jnahuel-developer/Probador-de-cables/Cables/02. Terminados - PDF/MAZ000157 - Diagrama eléctrico.pdf

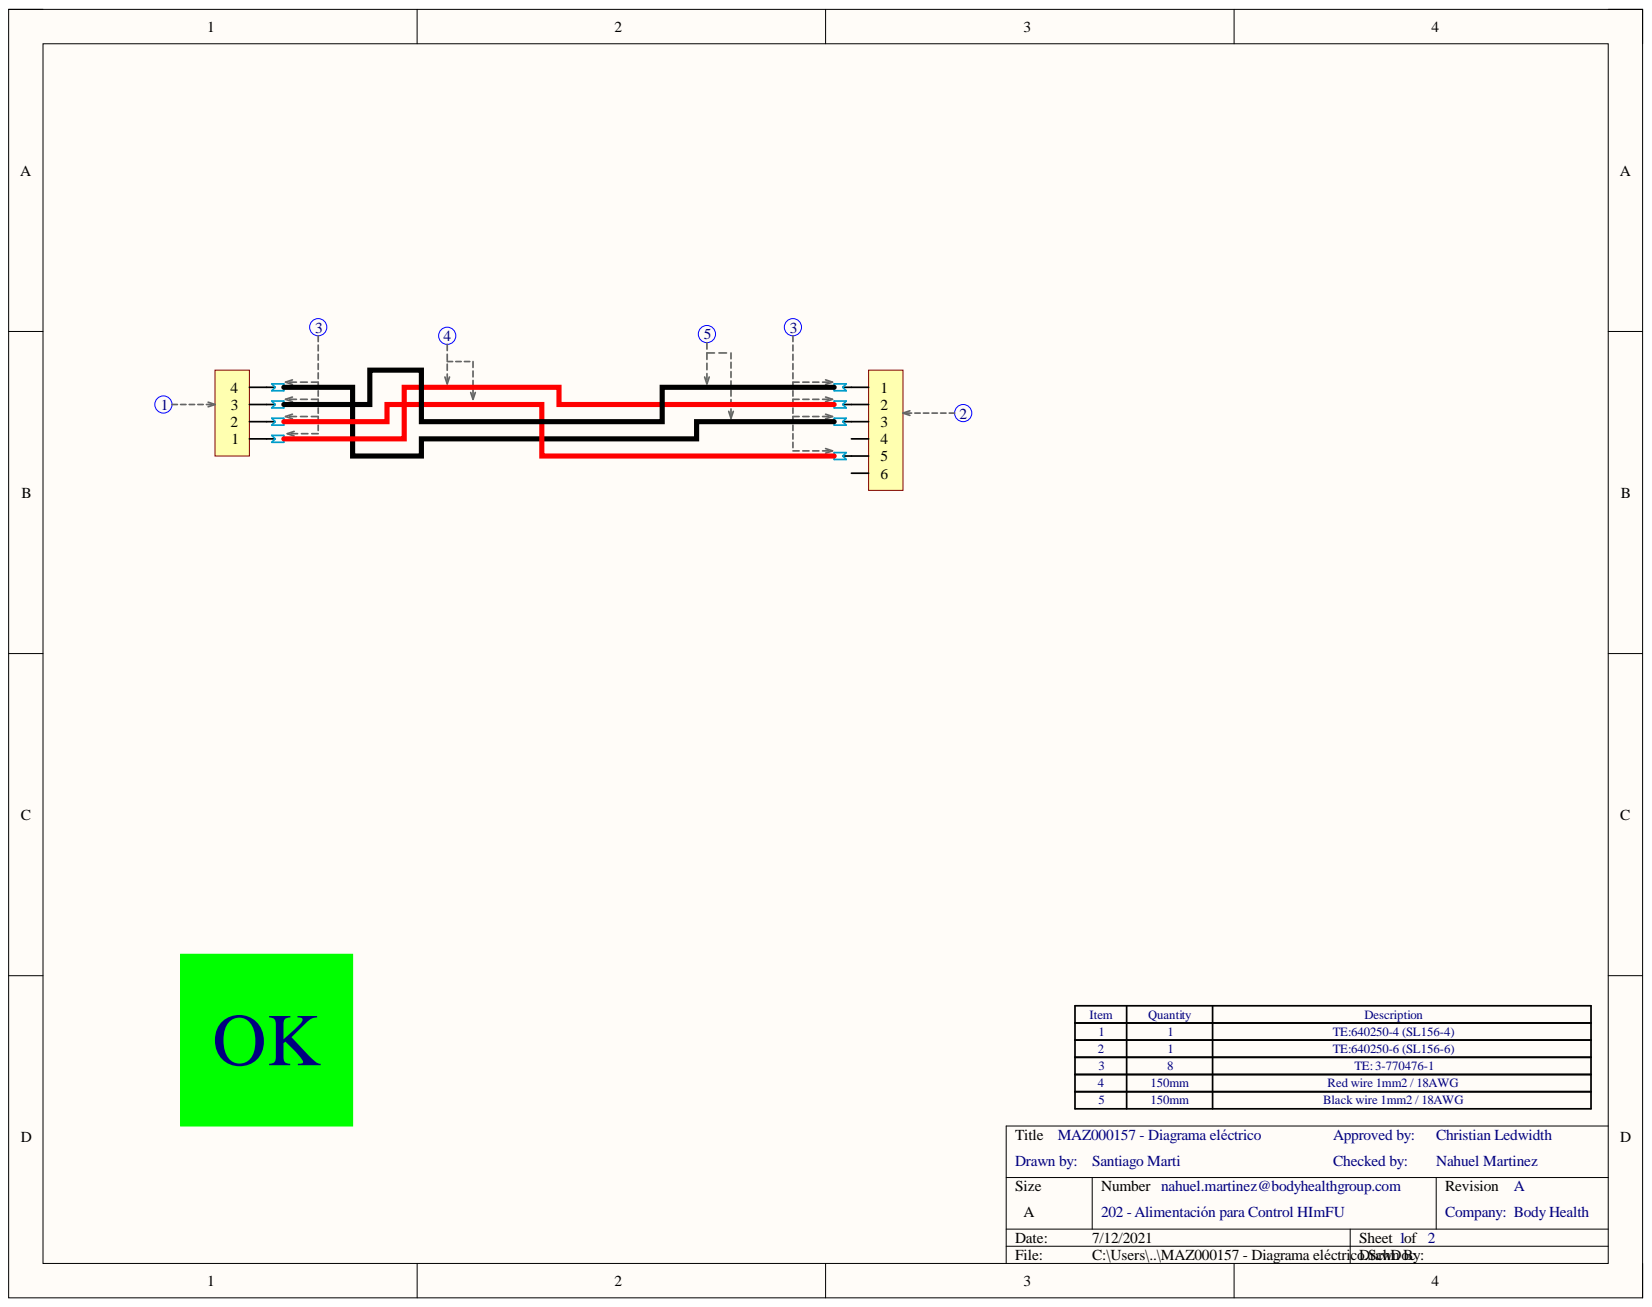
[picture p18: page 1]

Item | Quantity | Description
1 | 1 | TE:640250-4 (SL156-4)
2 | 1 | TE:640250-6 (SL156-6)
3 | 8 | TE: 3-770476-1
4 | 150mm | Red wire 1mm2 / 18AWG
5 | 150mm | Black wire 1mm2 / 18AWG

Size A | Number nahuel.martinez@bodyhealthgroup.com 202 - Alimentación para Control HImFU | Revision A Company: Body Health

Date: 7/12/2021 | Sheet of 1 2
File: C:\Users\..\MAZ000157 - Diagrama eléctricoDr.ScawhDon Bcy:
