jnahuel-developer/Probador-de-cables/Cables/02. Terminados - PDF/MAZ000158 - Diagrama eléctrico.pdf

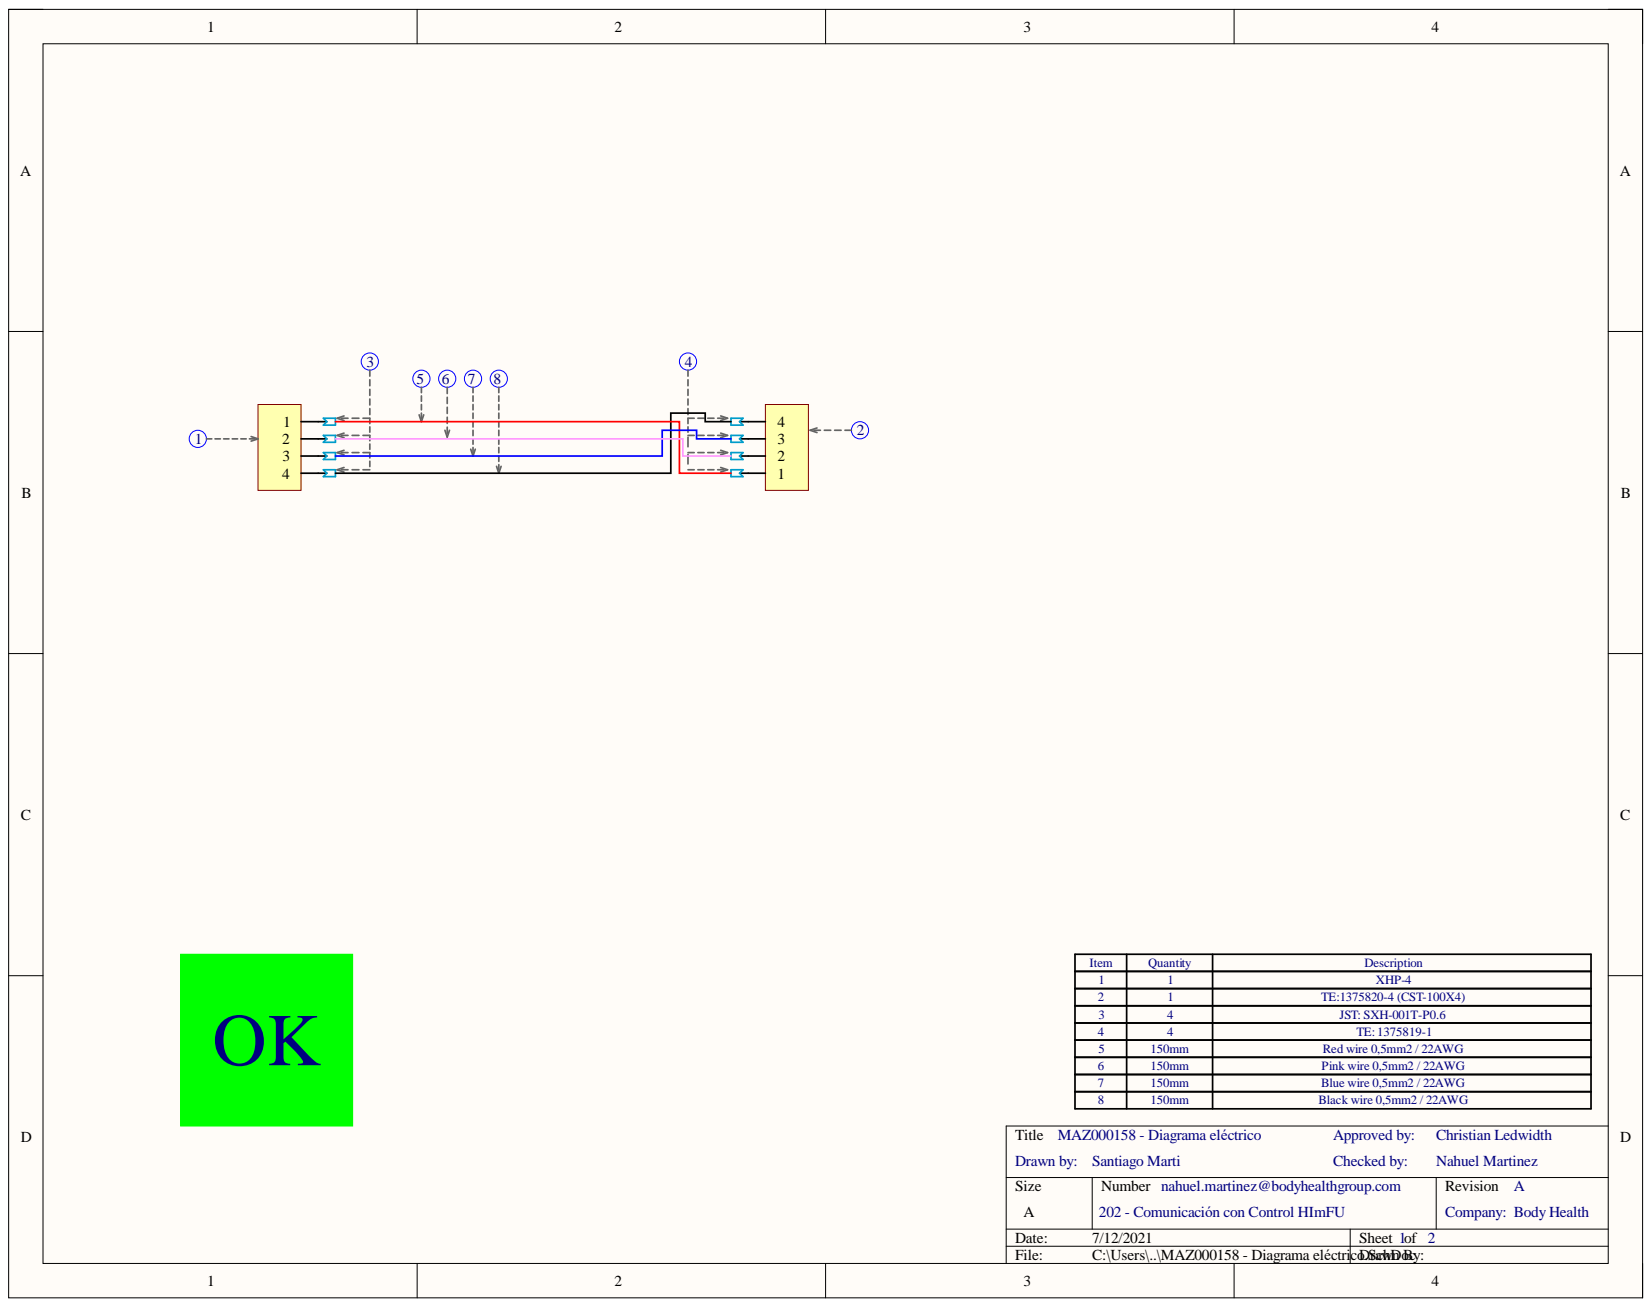
[picture p20: page 1]

1 | 1 | XHP-4
2 | 1 | TE:1375820-4 (CST-100X4)
3 | 4 | JST: SXH-001T-P0.6
4 | 4 | TE: 1375819-1
5 | 150mm | Red wire 0,5mm2 / 22AWG
6 | 150mm | Pink wire 0,5mm2 / 22AWG
7 | 150mm | Blue wire 0,5mm2 / 22AWG
8 | 150mm | Black wire 0,5mm2 / 22AWG

Size A | Number nahuel.martinez@bodyhealthgroup.com 202 - Comunicación con Control HImFU | Revision A Company: Body Health

Date: 7/12/2021 | Sheet of 1 2
File: C:\Users\..\MAZ000158 - Diagrama eléctricoDr.ScawhDon Bcy:
