jnahuel-developer/Probador-de-cables/Cables/02. Terminados - PDF/MAZ000159 - Diagrama eléctrico.pdf

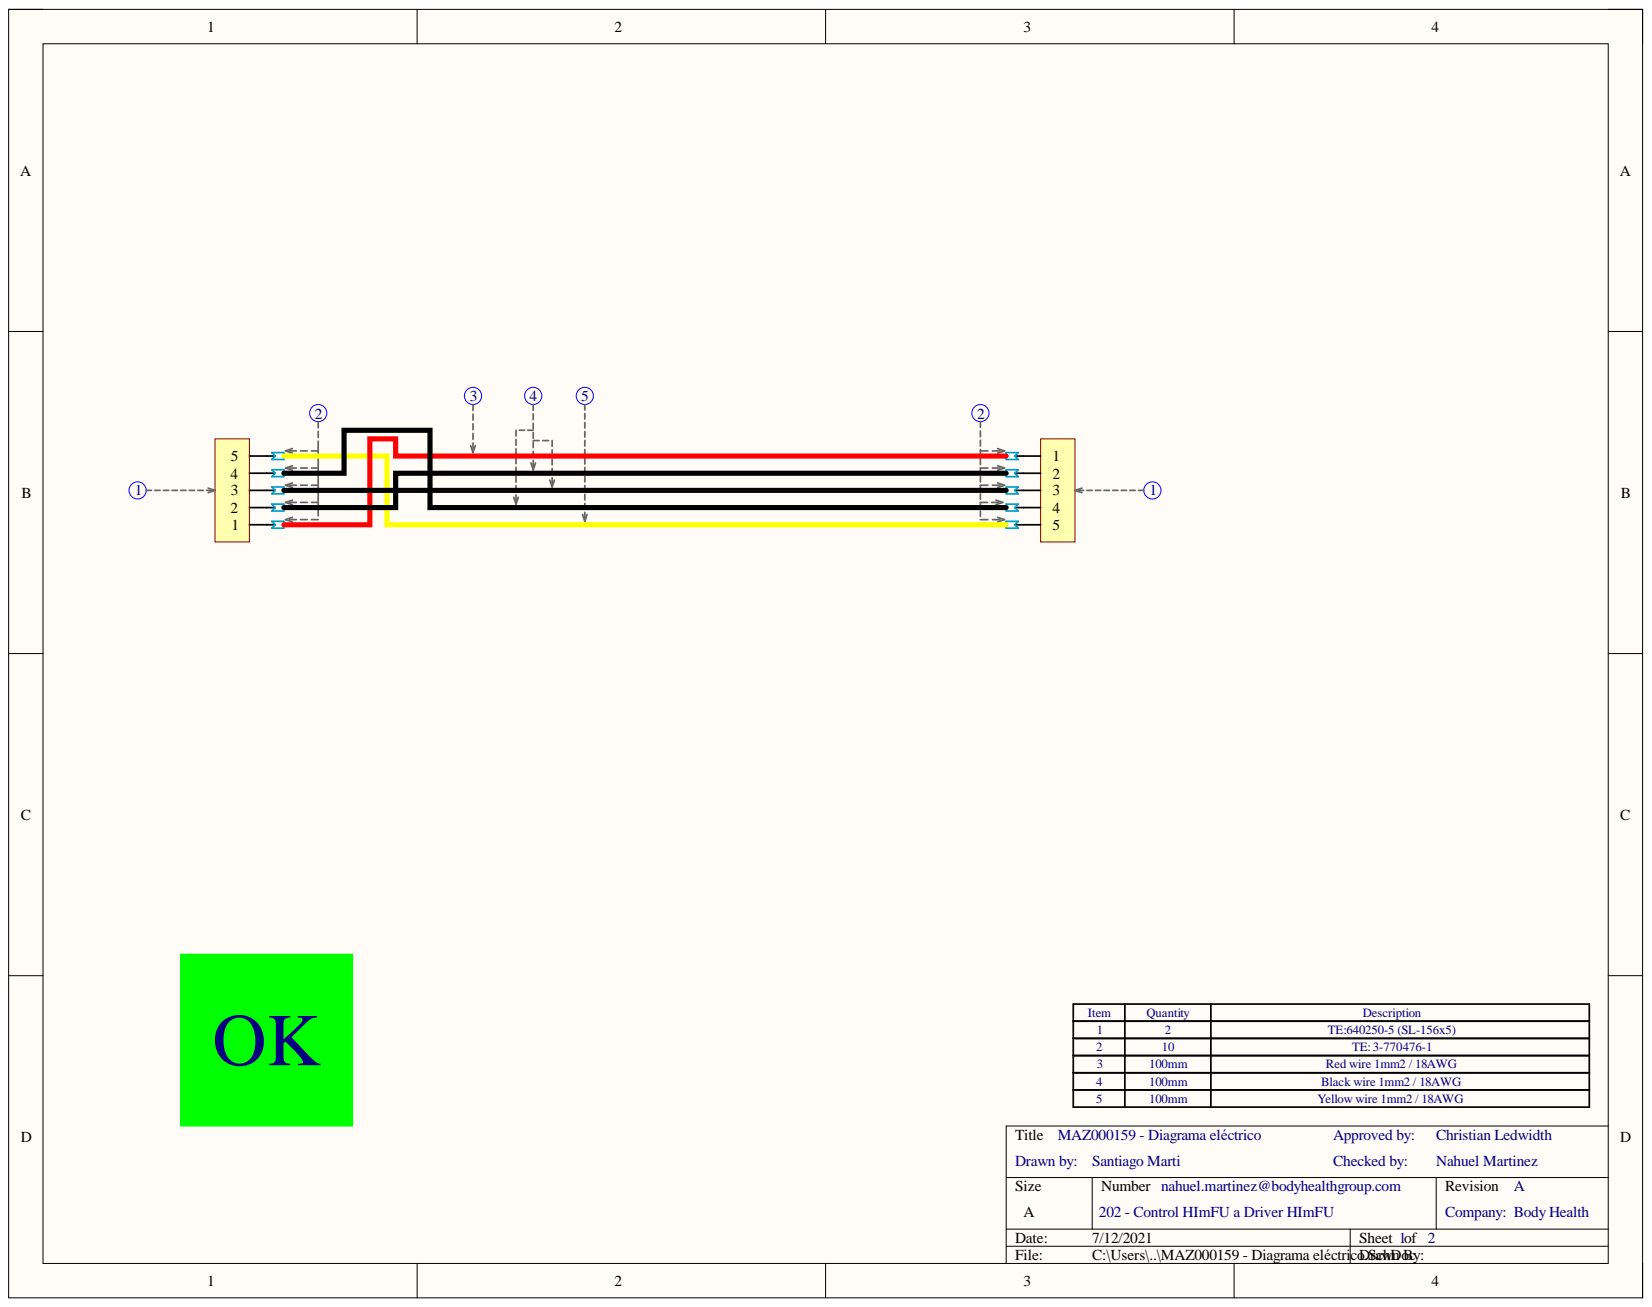
[picture p21: page 1]

Item | Quantity | Description
1 | 2 | TE:640250-5 (SL-156x5)
2 | 10 | TE: 3-770476-1
3 | 100mm | Red wire 1mm2 / 18AWG
4 | 100mm | Black wire 1mm2 / 18AWG
5 | 100mm | Yellow wire 1mm2 / 18AWG

Size A | Number nahuel.martinez@bodyhealthgroup.com 202 - Control HImFU a Driver HImFU | Revision A Company: Body Health

Date: 7/12/2021 | Sheet of 1 2
File: C:\Users\..\MAZ000159 - Diagrama eléctricoDr.ScawhDon Bcy:
