jnahuel-developer/Probador-de-cables/Cables/02. Terminados - PDF/MAZ000159 - Diagrama físico.pdf

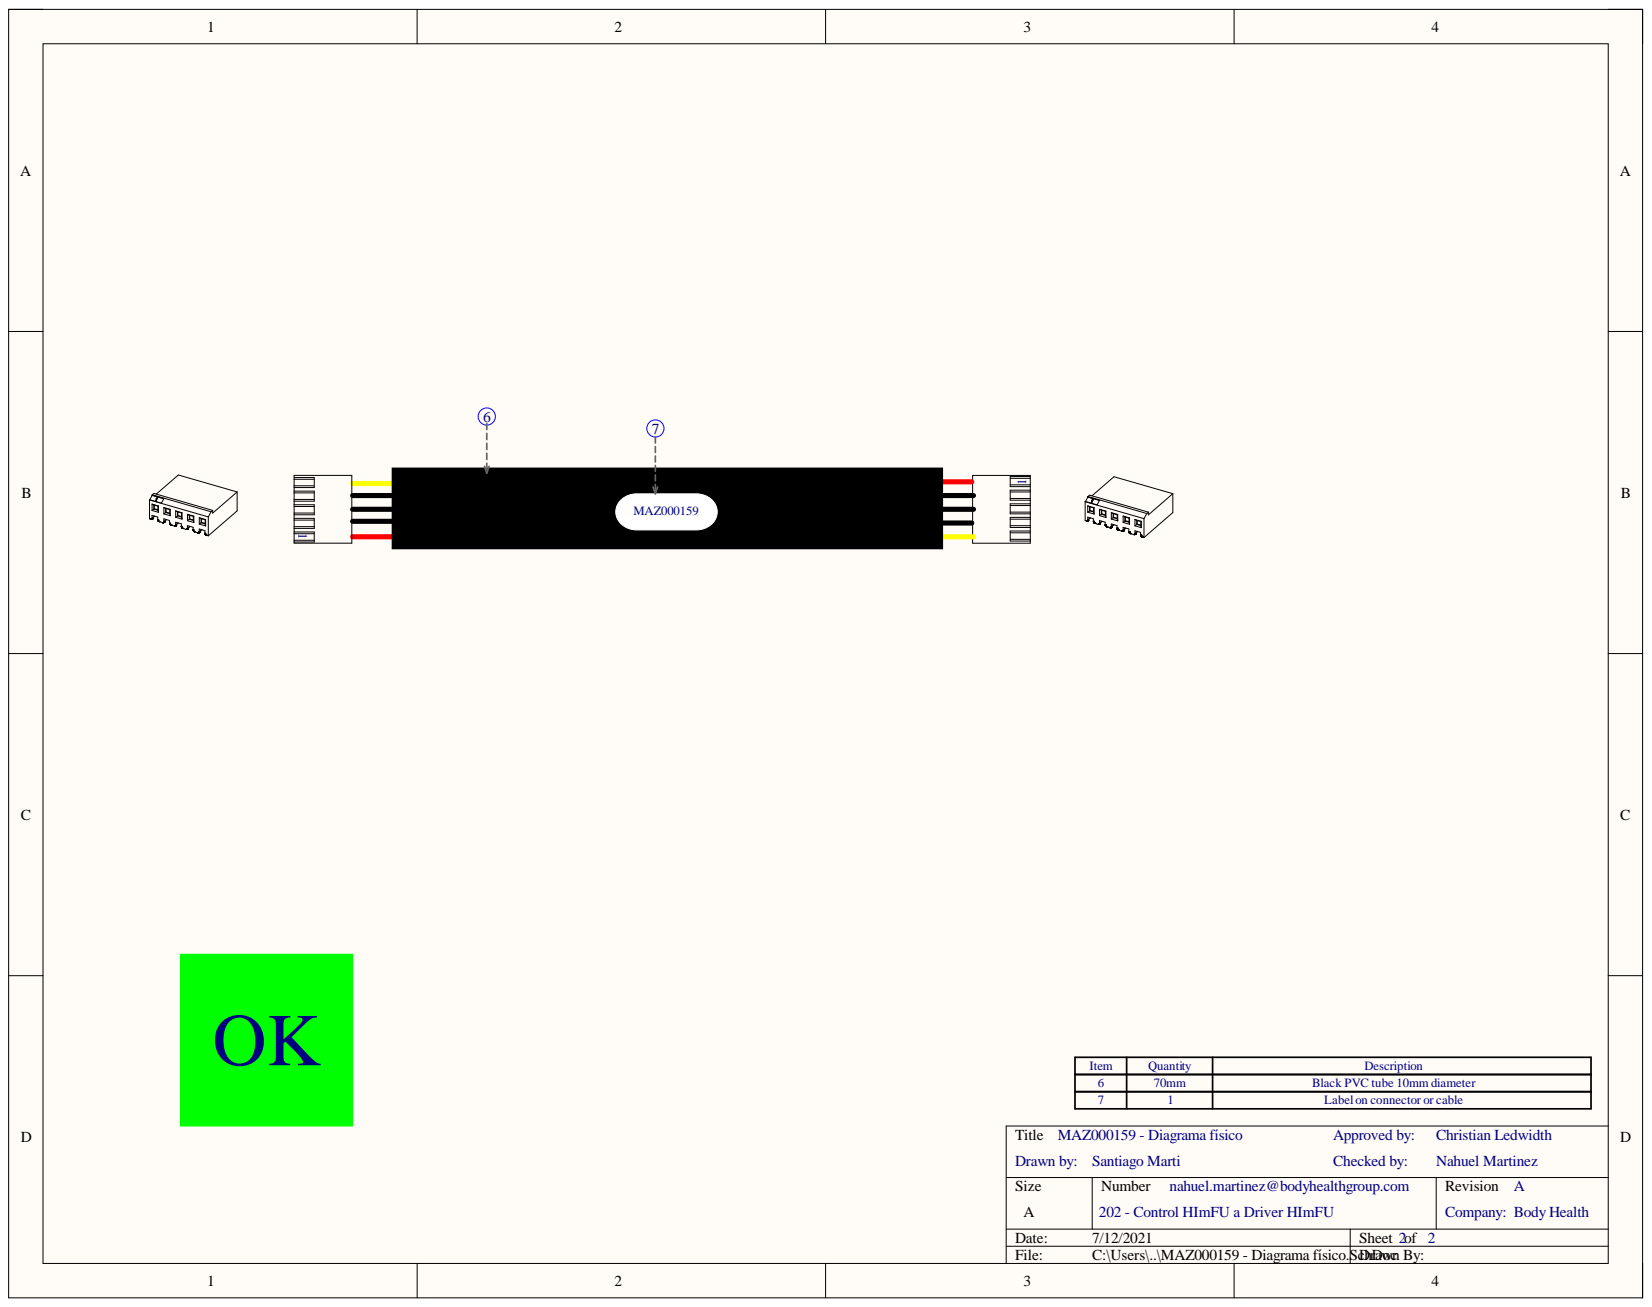
[picture p22: page 1]

Item | Quantity | Description
6 | 70mm | Black PVC tube 10mm diameter
7 | 1 | Label on connector or cable

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

Date: 7/12/2021 | Sheet of 2 2
File: C:\Users\..\MAZ000159 - Diagrama físico.ScDrhDoawcn By:
