jnahuel-developer/Probador-de-cables/Cables/02. Terminados - PDF/MAZ000160 - Diagrama eléctrico.pdf

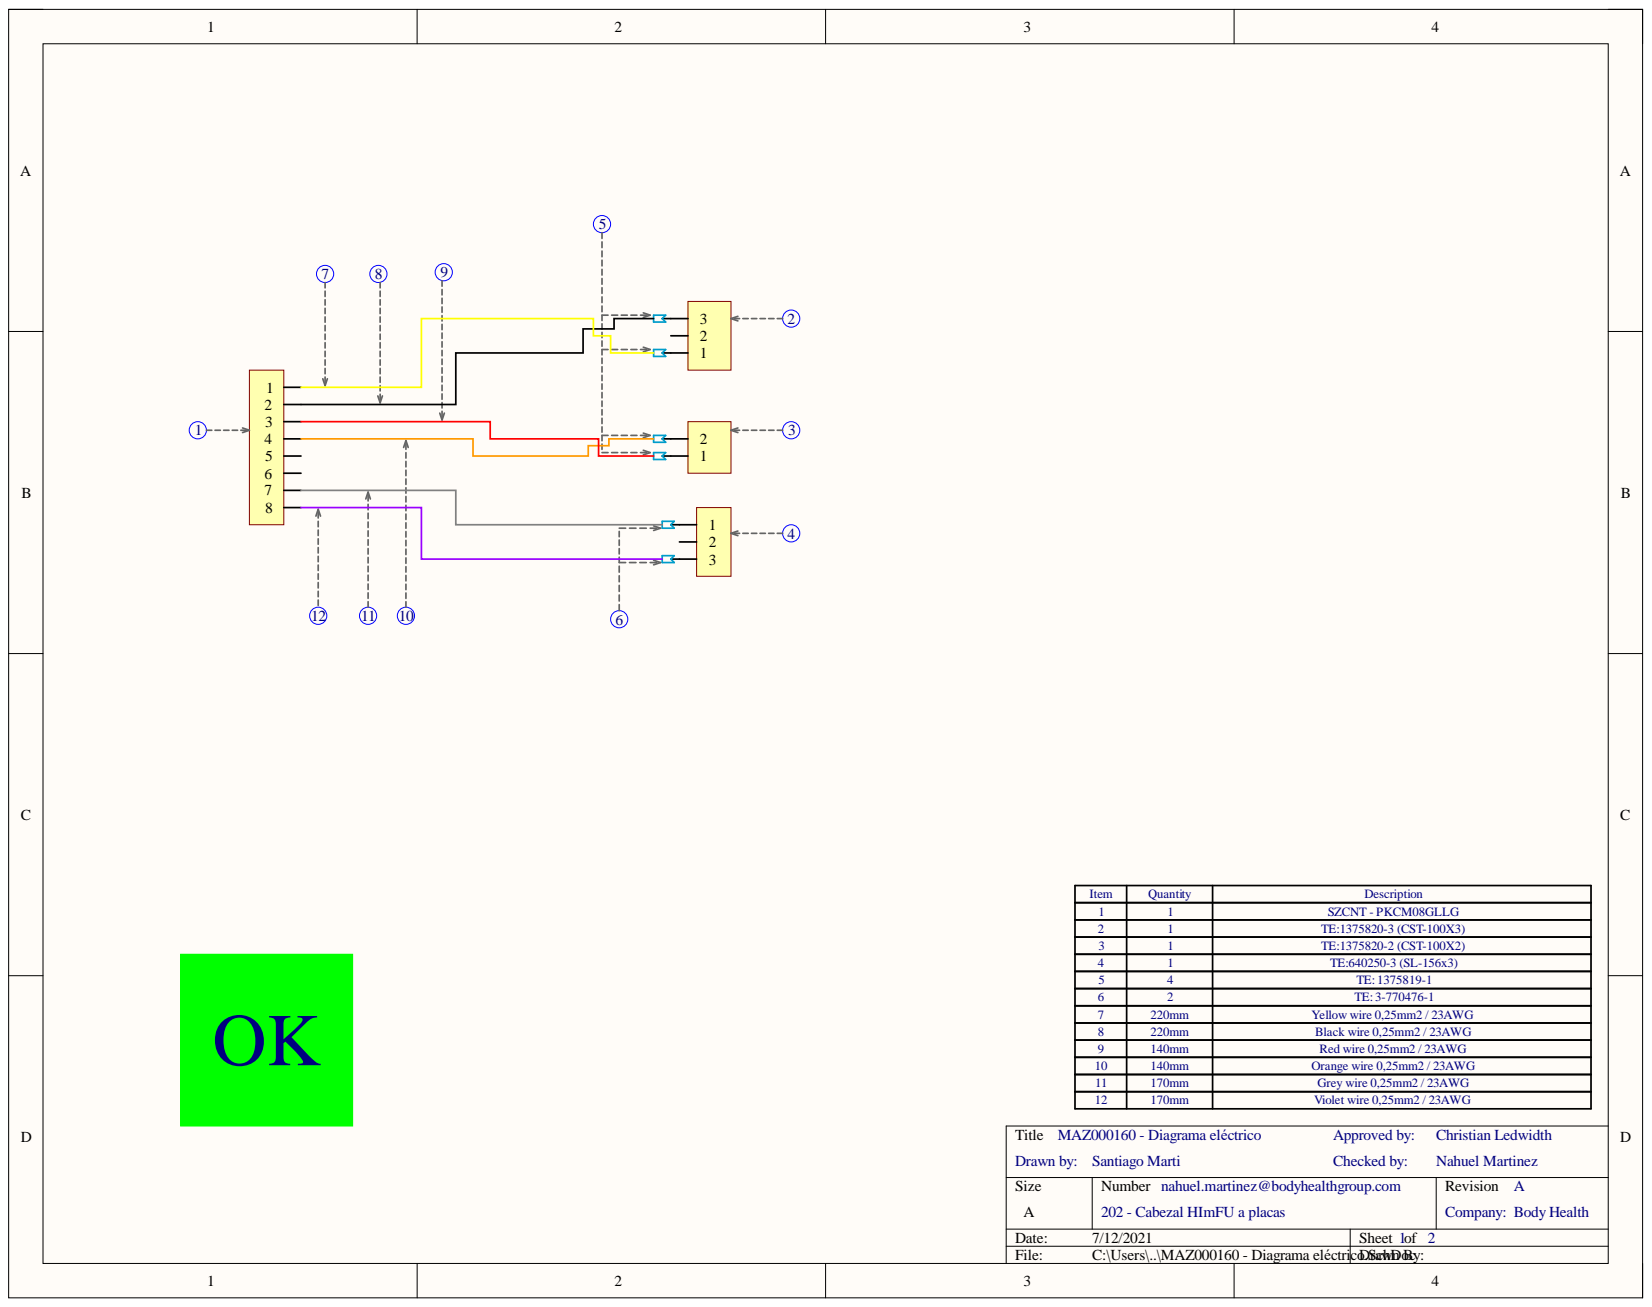
[picture p23: page 1]

Item | Quantity | Description
1 | 1 | SZCNT - PKCM08GLLG
2 | 1 | TE:1375820-3 (CST-100X3)
3 | 1 | TE:1375820-2 (CST-100X2)

5 | 4 | TE: 1375819-1
6 | 2 | TE: 3-770476-1
7 | 220mm | Yellow wire 0,25mm2 / 23AWG
8 | 220mm | Black wire 0,25mm2 / 23AWG
9 | 140mm | Red wire 0,25mm2 / 23AWG
10 | 140mm | Orange wire 0,25mm2 / 23AWG
11 | 170mm | Grey wire 0,25mm2 / 23AWG
12 | 170mm | Violet wire 0,25mm2 / 23AWG

Size A | Number nahuel.martinez@bodyhealthgroup.com 202 - Cabezal HImFU a placas | Revision A Company: Body Health

Date: 7/12/2021 | Sheet of 1 2
File: C:\Users\..\MAZ000160 - Diagrama eléctricoDr.ScawhDon Bcy:
