jnahuel-developer/Probador-de-cables/Cables/02. Terminados - PDF/MAZ000160 - Diagrama físico.pdf

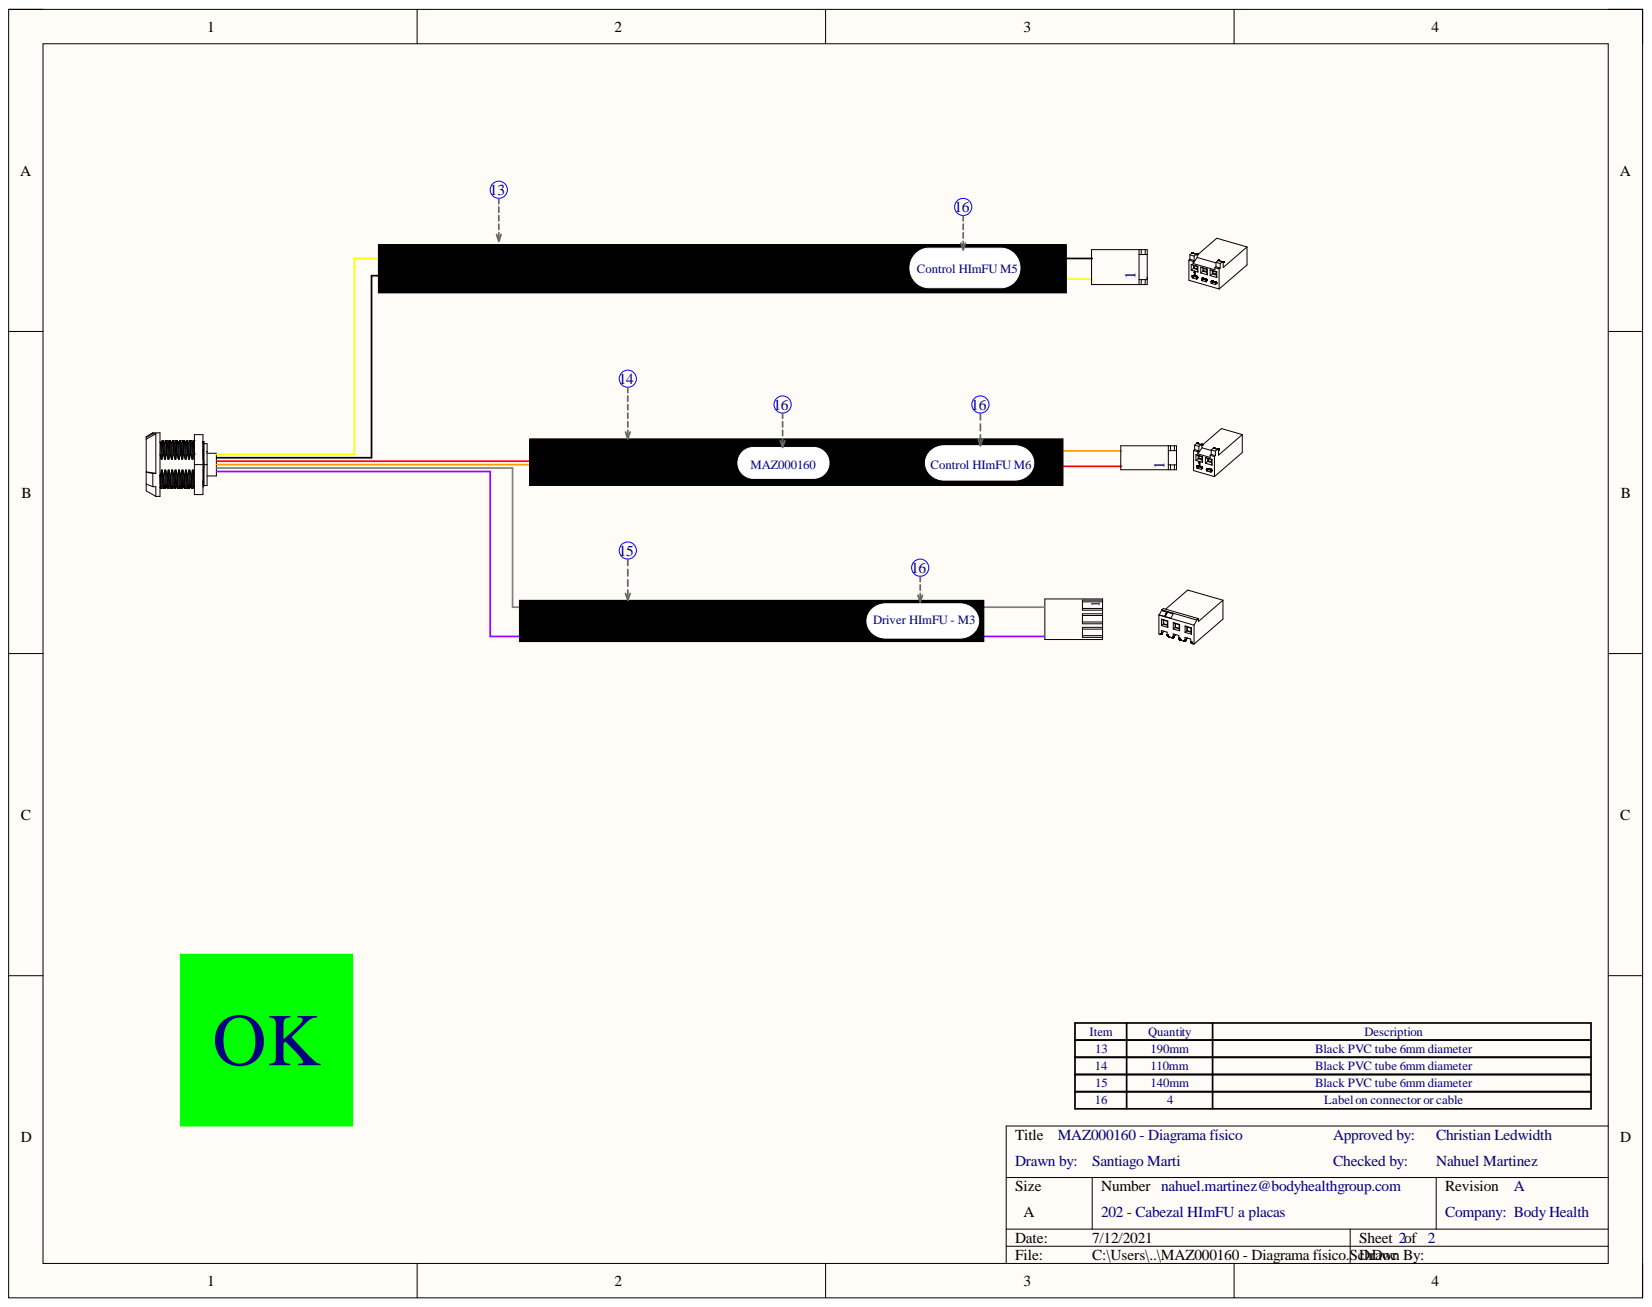
[picture p24: page 1]

Item | Quantity | Description
13 | 190mm | Black PVC tube 6mm diameter
14 | 110mm | Black PVC tube 6mm diameter
15 | 140mm | Black PVC tube 6mm diameter
16 | 4 | Label on connector or cable

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

Date: 7/12/2021 | Sheet of 2 2
File: C:\Users\..\MAZ000160 - Diagrama físico.ScDrhDoawcn By:
