jnahuel-developer/Probador-de-cables/Cables/02. Terminados - PDF/MAZ000161 - Diagrama eléctrico.pdf

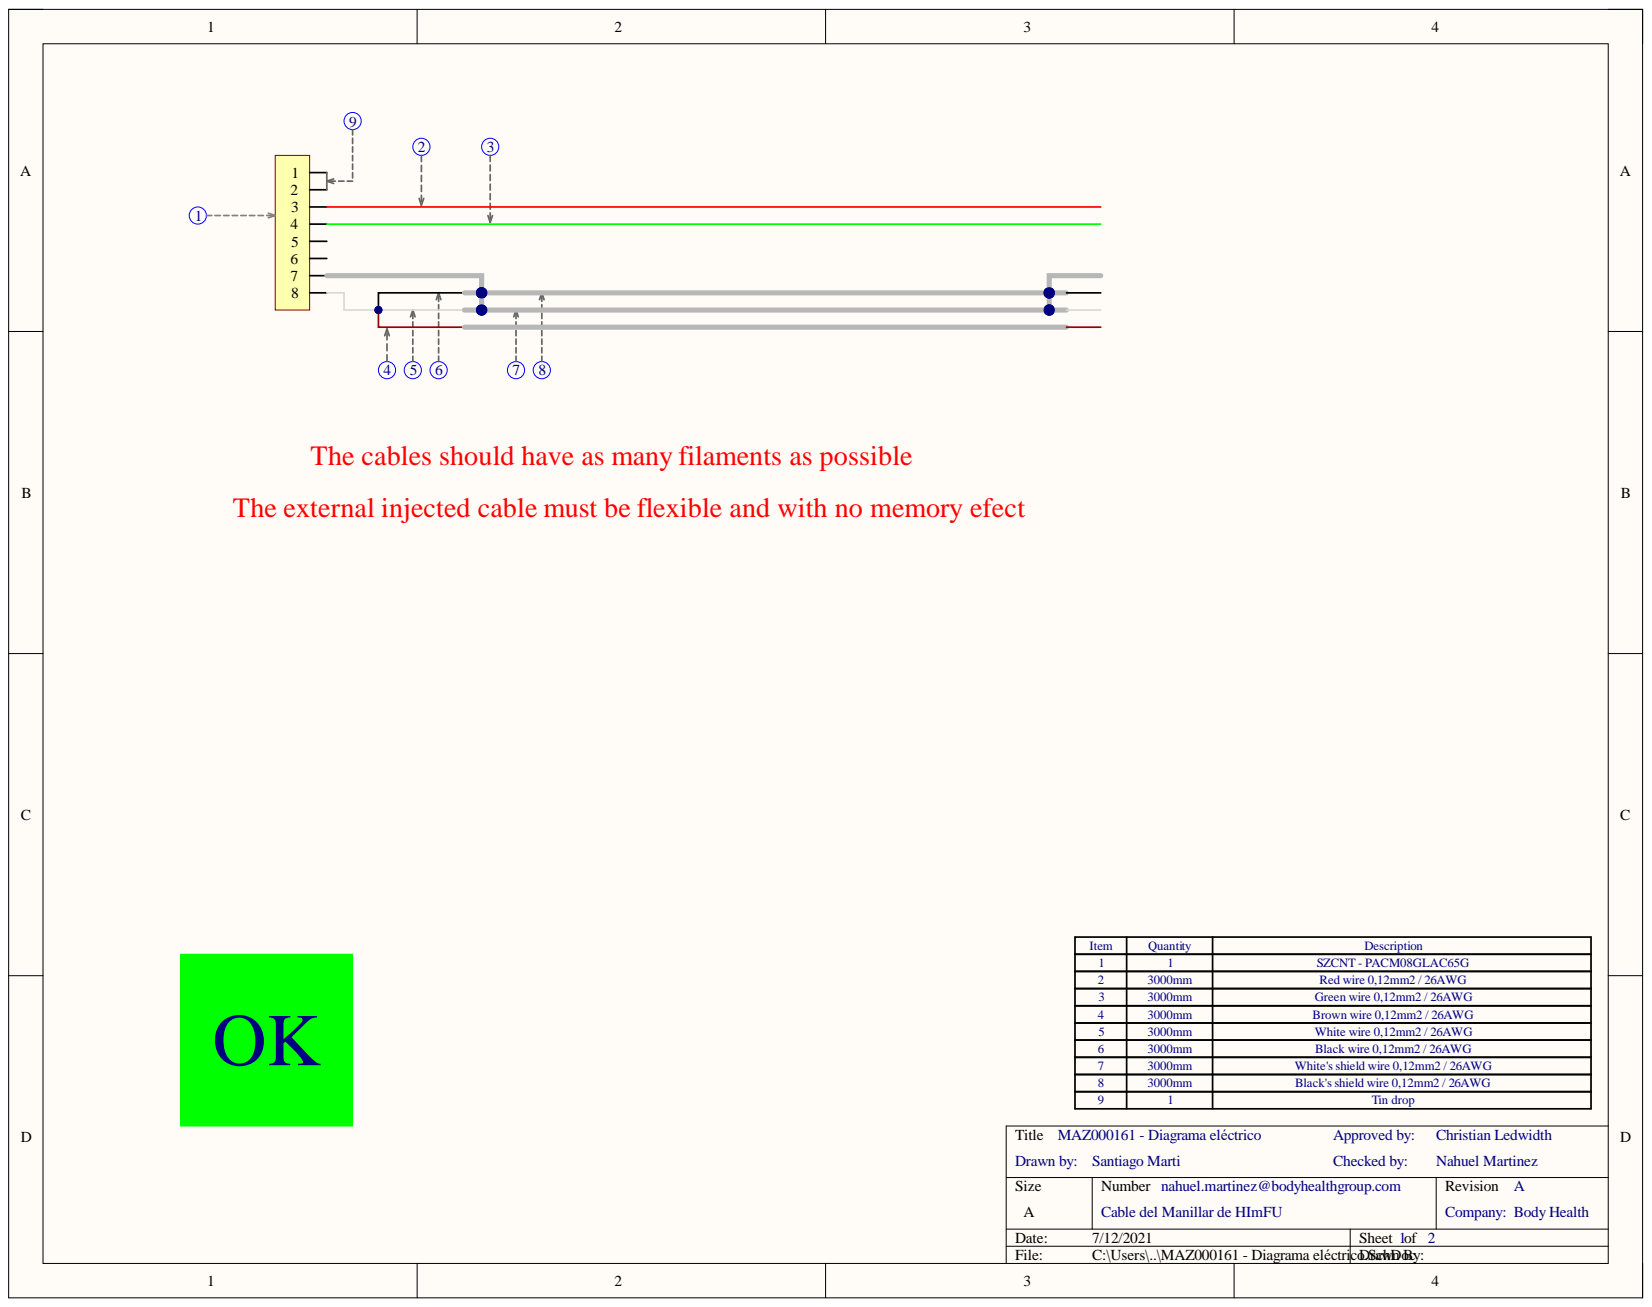
[picture p25: page 1]

The cables should have as many filaments as possible

The external injected cable must be flexible and with no memory efect

2 | 3000mm | Red wire 0,12mm2 / 26AWG
3 | 3000mm | Green wire 0,12mm2 / 26AWG
4 | 3000mm | Brown wire 0,12mm2 / 26AWG
5 | 3000mm | White wire 0,12mm2 / 26AWG
6 | 3000mm | Black wire 0,12mm2 / 26AWG
7 | 3000mm | White'sshield wire 0,12mm2 / 26AWG
8 | 3000mm | Black'sshield wire 0,12mm2 / 26AWG
9 | 1 | Tin drop

Size A | Number nahuel.martinez@bodyhealthgroup.com Cable del Manillar de HImFU | Revision A Company: Body Health

Date: 7/12/2021 | Sheet of 1 2
File: C:\Users\..\MAZ000161 - Diagrama eléctricoDr.ScawhDon Bcy:
