jnahuel-developer/Probador-de-cables/Cables/02. Terminados - PDF/MAZ000163 - Diagrama eléctrico.pdf

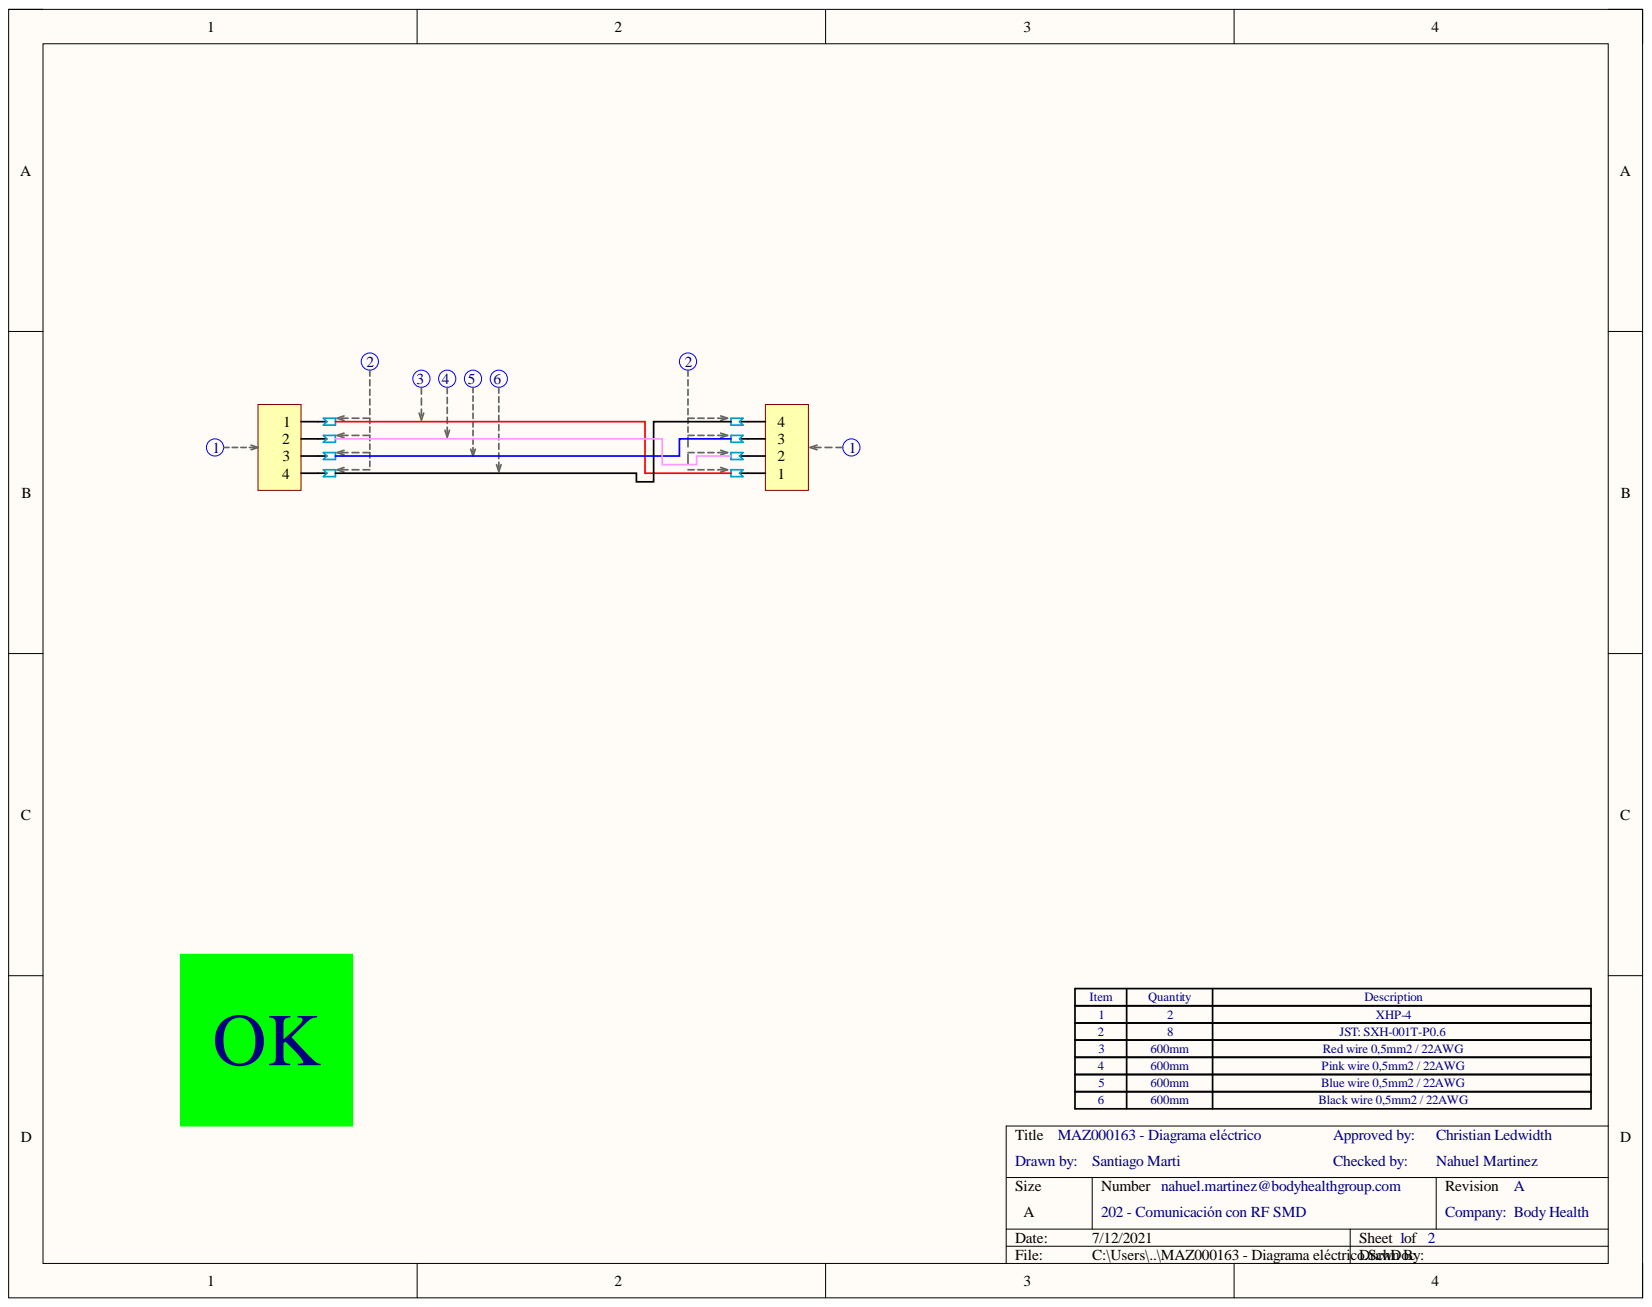
[picture p28: page 1]

Item | Quantity | Description
1 | 2 | XHP-4
2 | 8 | JST: SXH-001T-P0.6
3 | 600mm | Red wire 0,5mm2 / 22AWG
4 | 600mm | Pink wire 0,5mm2 / 22AWG
5 | 600mm | Blue wire 0,5mm2 / 22AWG
6 | 600mm | Black wire 0,5mm2 / 22AWG

Size A | Number nahuel.martinez@bodyhealthgroup.com 202 - Comunicación con RF SMD | Revision A Company: Body Health

Date: 7/12/2021 | Sheet of 1 2
File: C:\Users\..\MAZ000163 - Diagrama eléctricoDr.ScawhDon Bcy:
