jnahuel-developer/Probador-de-cables/Cables/02. Terminados - PDF/MAZ000164 - Diagrama eléctrico.pdf

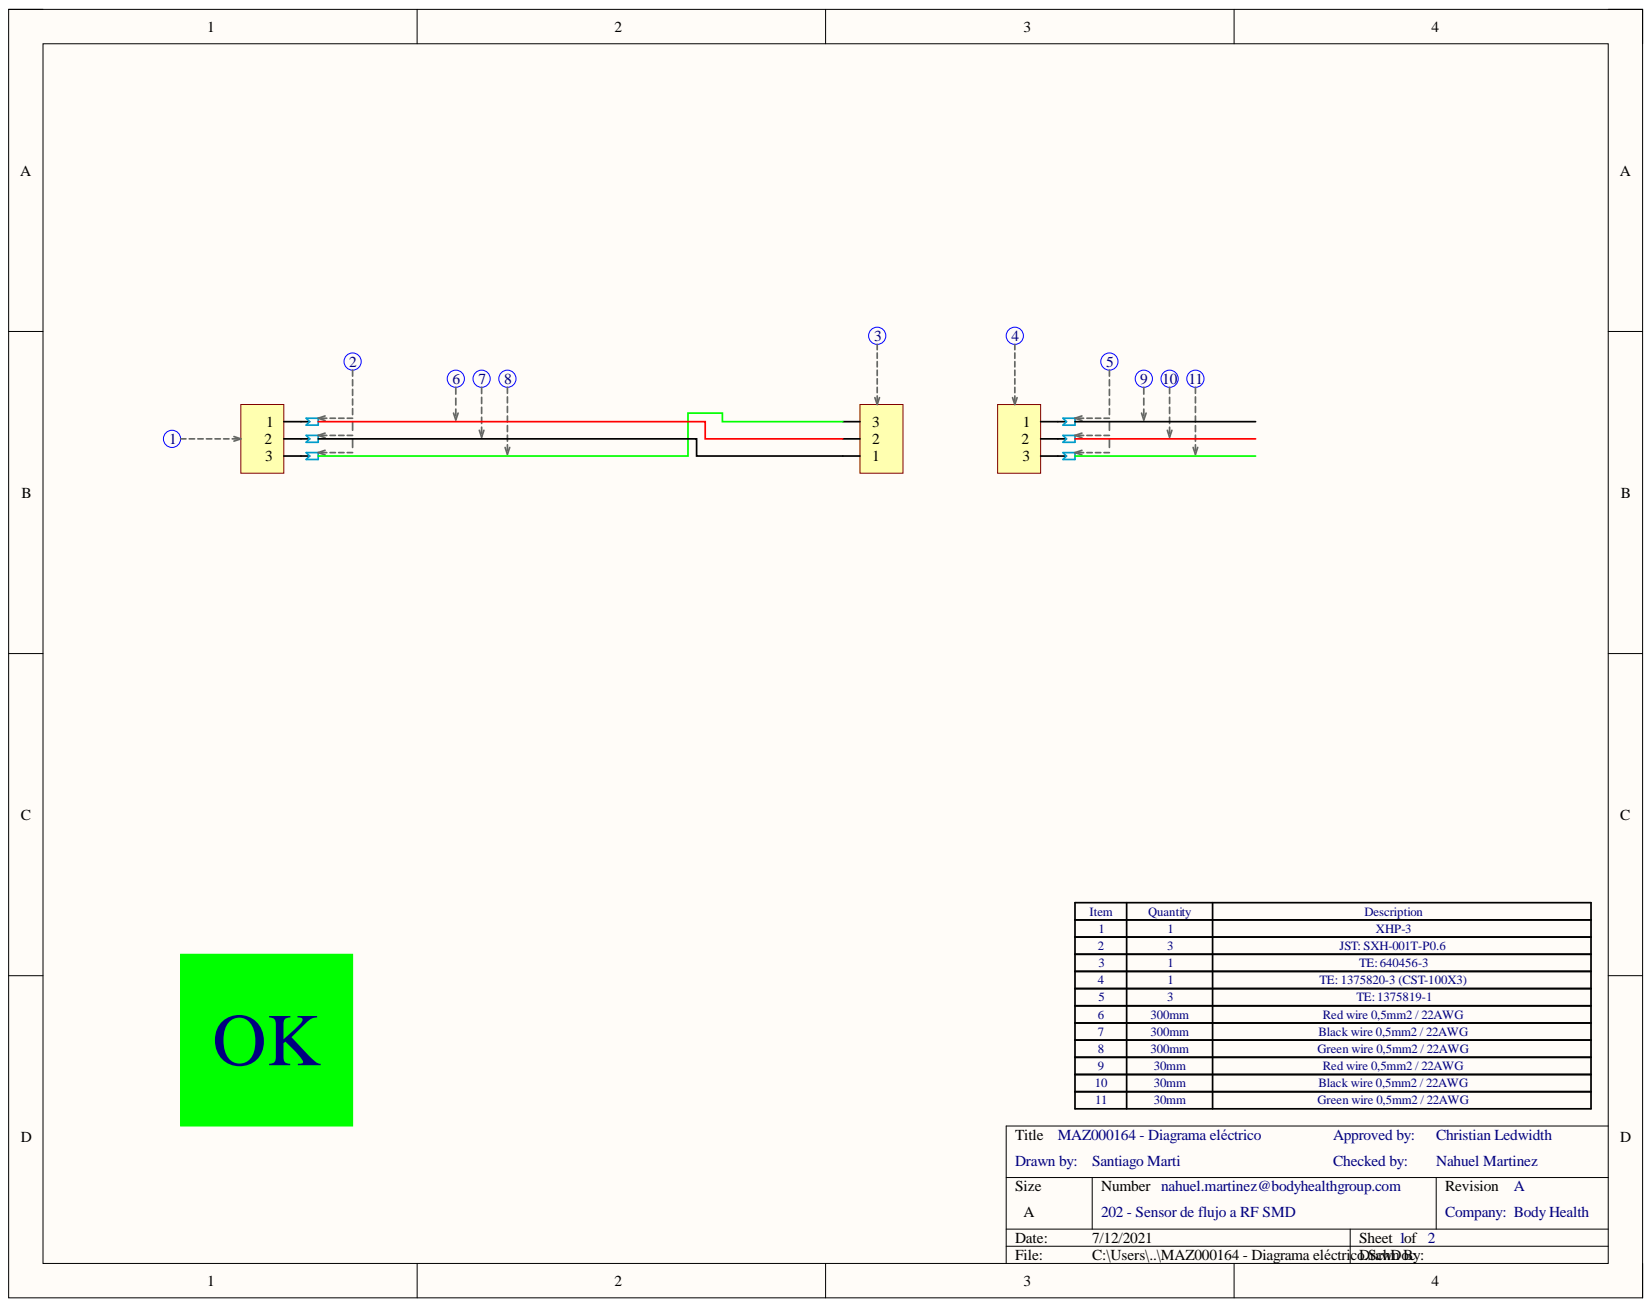
[picture p30: page 1]

Item | Quantity | Description
1 | 1 | XHP-3
2 | 3 | JST: SXH-001T-P0.6

4 | 1 | TE: 1375820-3 (CST-100X3)
5 | 3 | TE: 1375819-1
6 | 300mm | Red wire 0,5mm2 / 22AWG
7 | 300mm | Black wire 0,5mm2 / 22AWG
8 | 300mm | Green wire 0,5mm2 / 22AWG
9 | 30mm | Red wire 0,5mm2 / 22AWG
10 | 30mm | Black wire 0,5mm2 / 22AWG
11 | 30mm | Green wire 0,5mm2 / 22AWG

Size A | Number nahuel.martinez@bodyhealthgroup.com 202 - Sensor de flujo a RF SMD | Revision A Company: Body Health

Date: 7/12/2021 | Sheet of 1 2
File: C:\Users\..\MAZ000164 - Diagrama eléctricoDr.ScawhDon Bcy:
