jnahuel-developer/Probador-de-cables/Cables/02. Terminados - PDF/MAZ000165 - Diagrama eléctrico.pdf

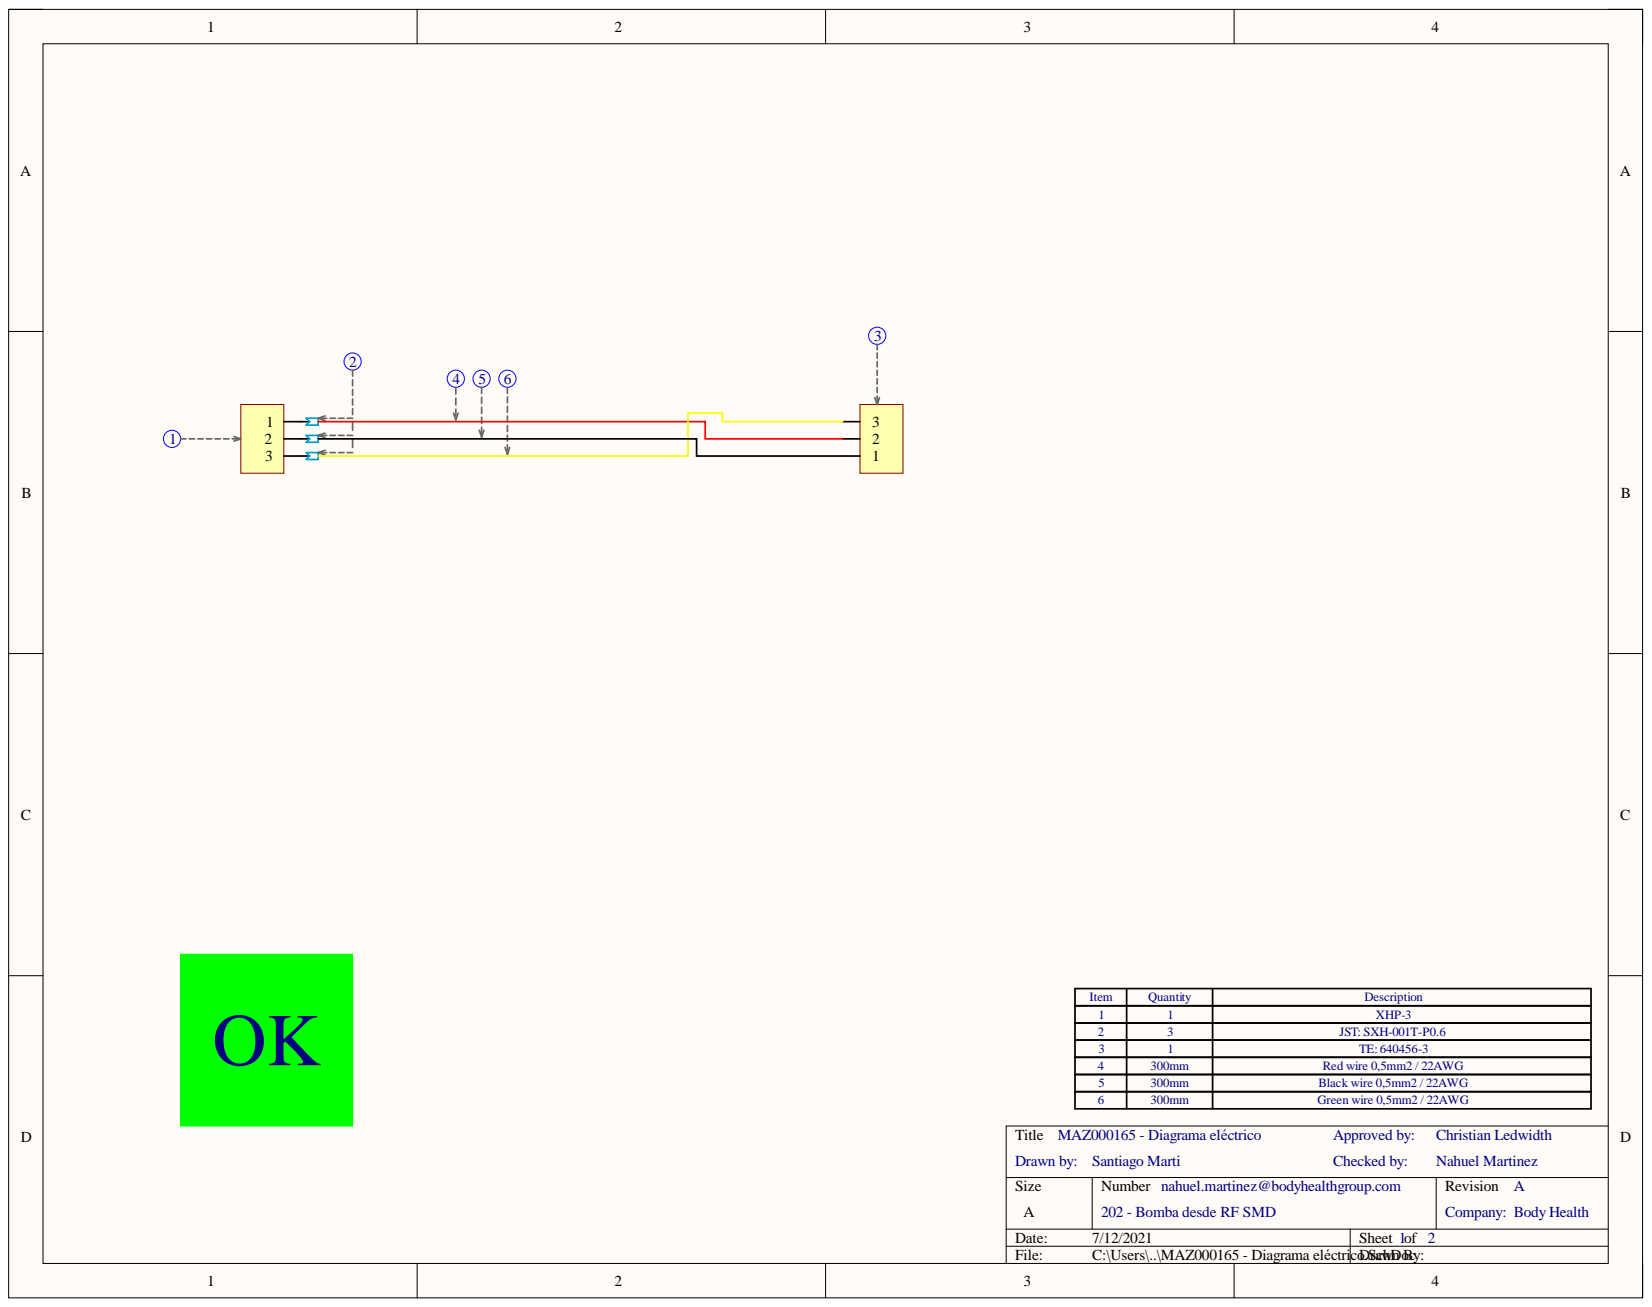
[picture p32: page 1]

Item | Quantity | Description
1 | 1 | XHP-3
2 | 3 | JST: SXH-001T-P0.6
3 | 1 | TE: 640456-3
4 | 300mm | Red wire 0,5mm2 / 22AWG
5 | 300mm | Black wire 0,5mm2 / 22AWG
6 | 300mm | Green wire 0,5mm2 / 22AWG

Size A | Number nahuel.martinez@bodyhealthgroup.com 202 - Bomba desde RF SMD | Revision A Company: Body Health

Date: 7/12/2021 | Sheet of 1 2
File: C:\Users\..\MAZ000165 - Diagrama eléctricoDr.ScawhDon Bcy:
