jnahuel-developer/Probador-de-cables/Cables/02. Terminados - PDF/MAZ000165 - Diagrama físico.pdf

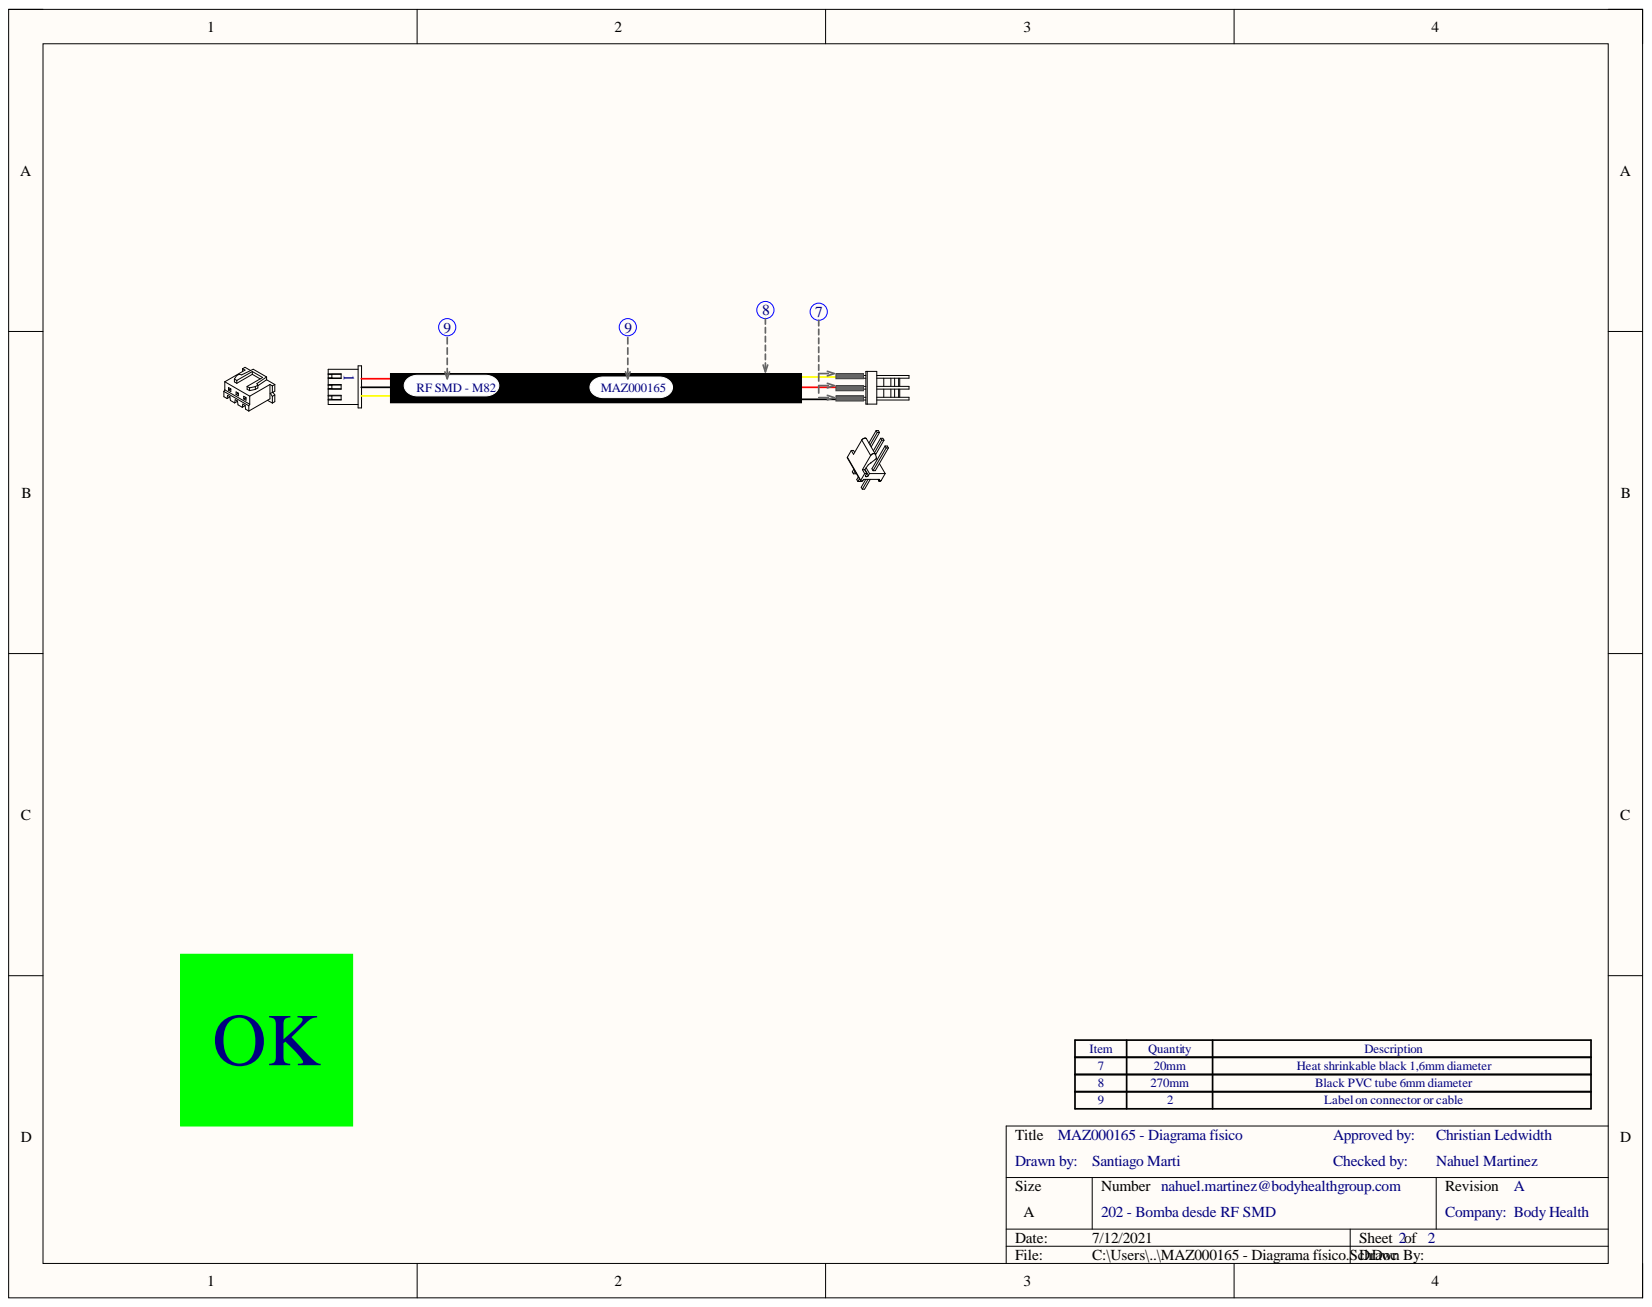
[picture p33: page 1]

Item | Quantity | Description
7 | 20mm | Heat shrinkable black 1,6mm diameter
8 | 270mm | Black PVC tube 6mm diameter
9 | 2 | Label on connector or cable

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

Date: 7/12/2021 | Sheet of 2 2
File: C:\Users\..\MAZ000165 - Diagrama físico.ScDrhDoawcn By:
