jnahuel-developer/Probador-de-cables/Cables/02. Terminados - PDF/MAZ000166 - Diagrama eléctrico.pdf

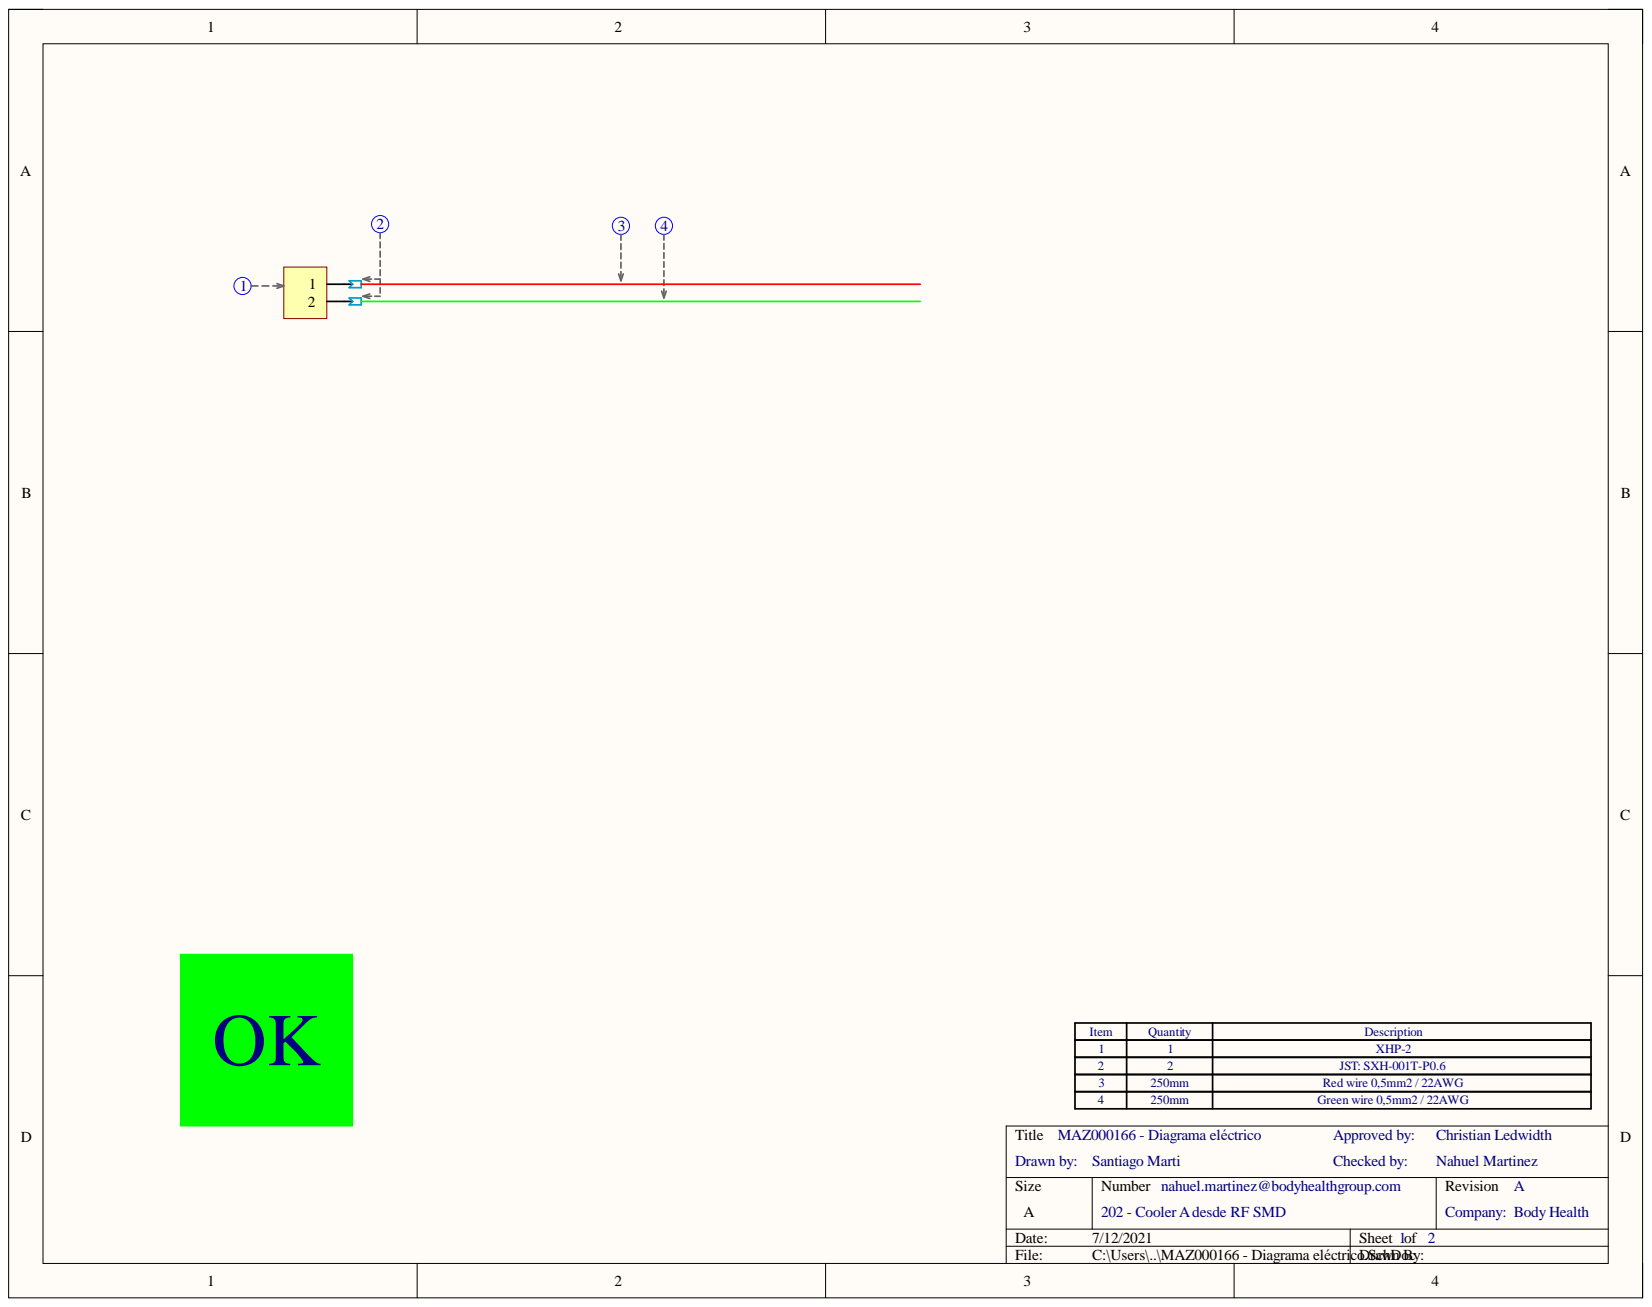
[picture p34: page 1]

Item | Quantity | Description
1 | 1 | XHP-2
2 | 2 | JST: SXH-001T-P0.6
3 | 250mm | Red wire 0,5mm2 / 22AWG
4 | 250mm | Green wire 0,5mm2 / 22AWG

Size A | Number nahuel.martinez@bodyhealthgroup.com 202 - Cooler A desde RF SMD | Revision A Company: Body Health

Date: 7/12/2021 | Sheet of 1 2
File: C:\Users\..\MAZ000166 - Diagrama eléctricoDr.ScawhDon Bcy:
