jnahuel-developer/Probador-de-cables/Cables/02. Terminados - PDF/MAZ000166 - Diagrama físico.pdf

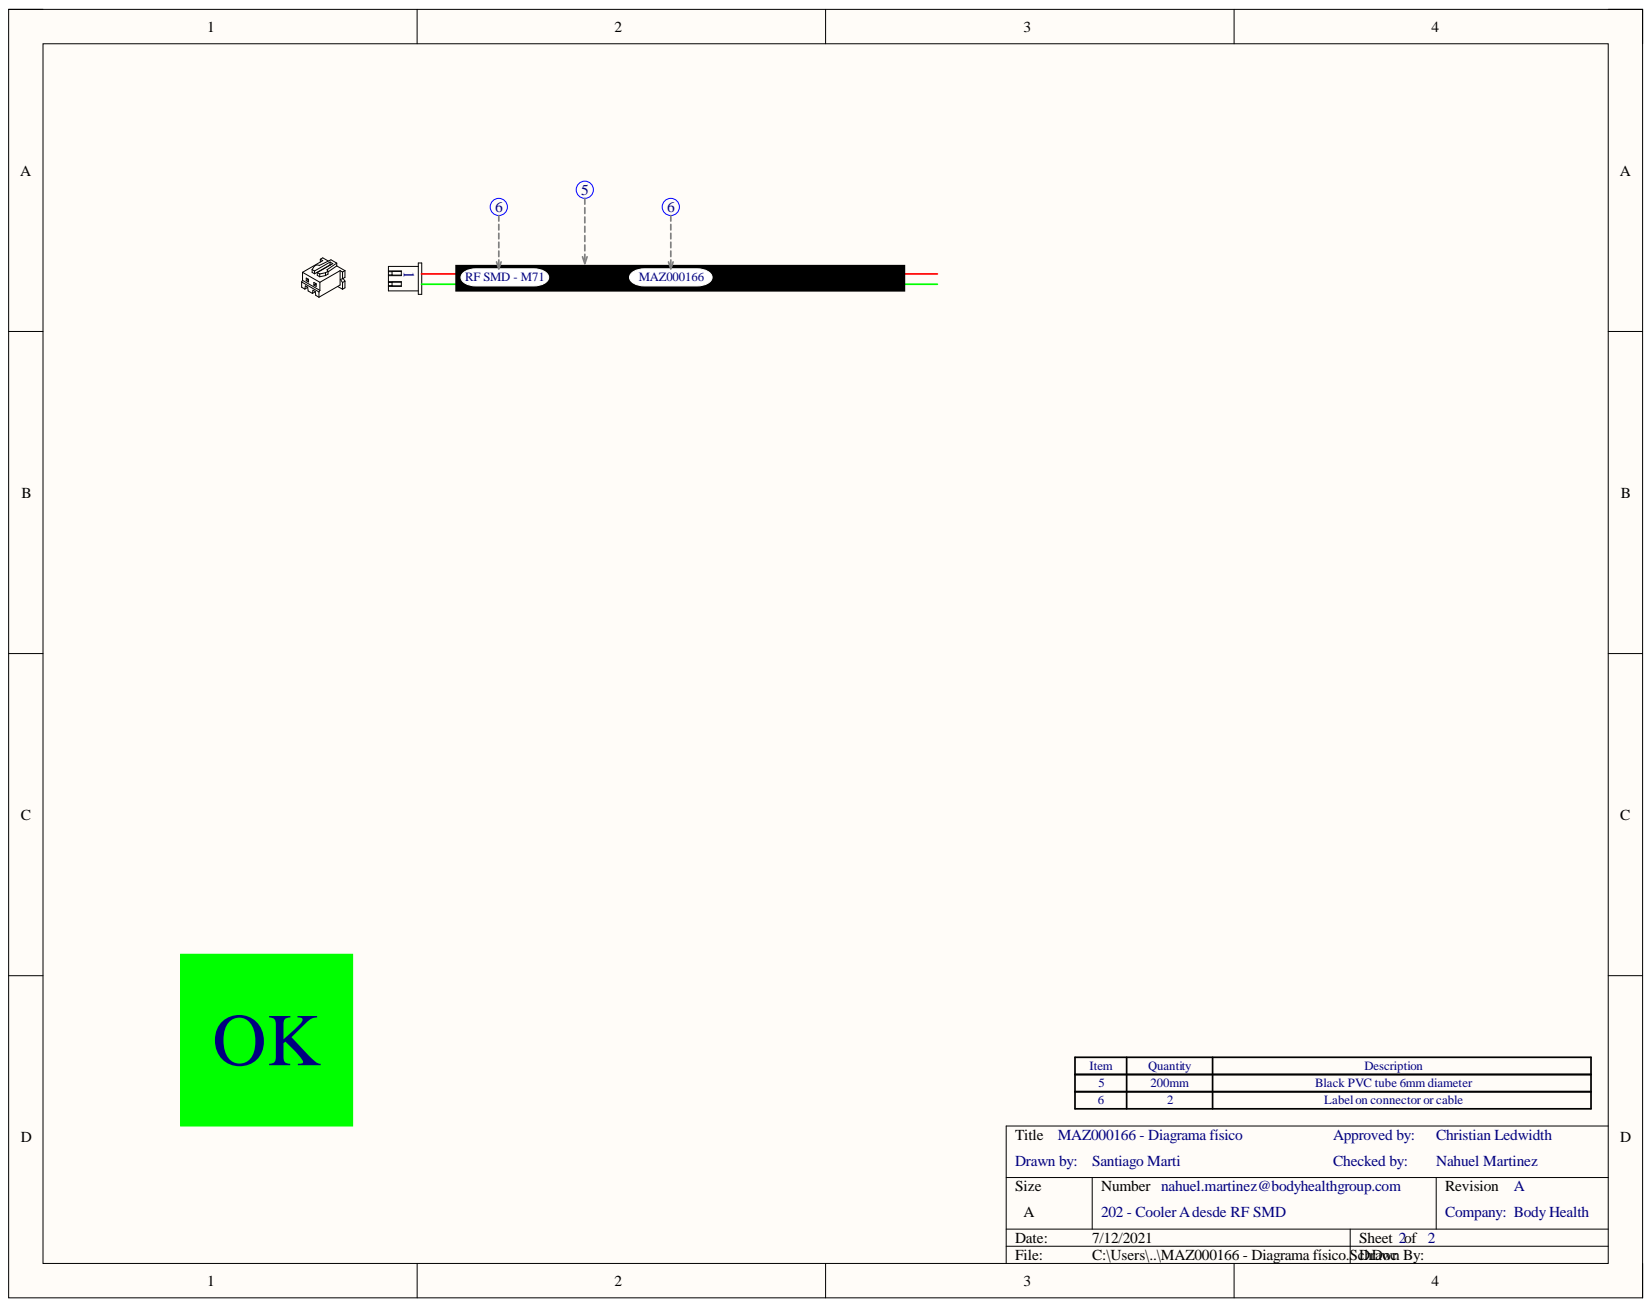
[picture p35: page 1]

Item | Quantity | Description
5 | 200mm | Black PVC tube 6mm diameter
6 | 2 | Label on connector or cable

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

Date: 7/12/2021 | Sheet of 2 2
File: C:\Users\..\MAZ000166 - Diagrama físico.ScDrhDoawcn By:
