jnahuel-developer/Probador-de-cables/Cables/02. Terminados - PDF/MAZ000168 - Diagrama físico.pdf

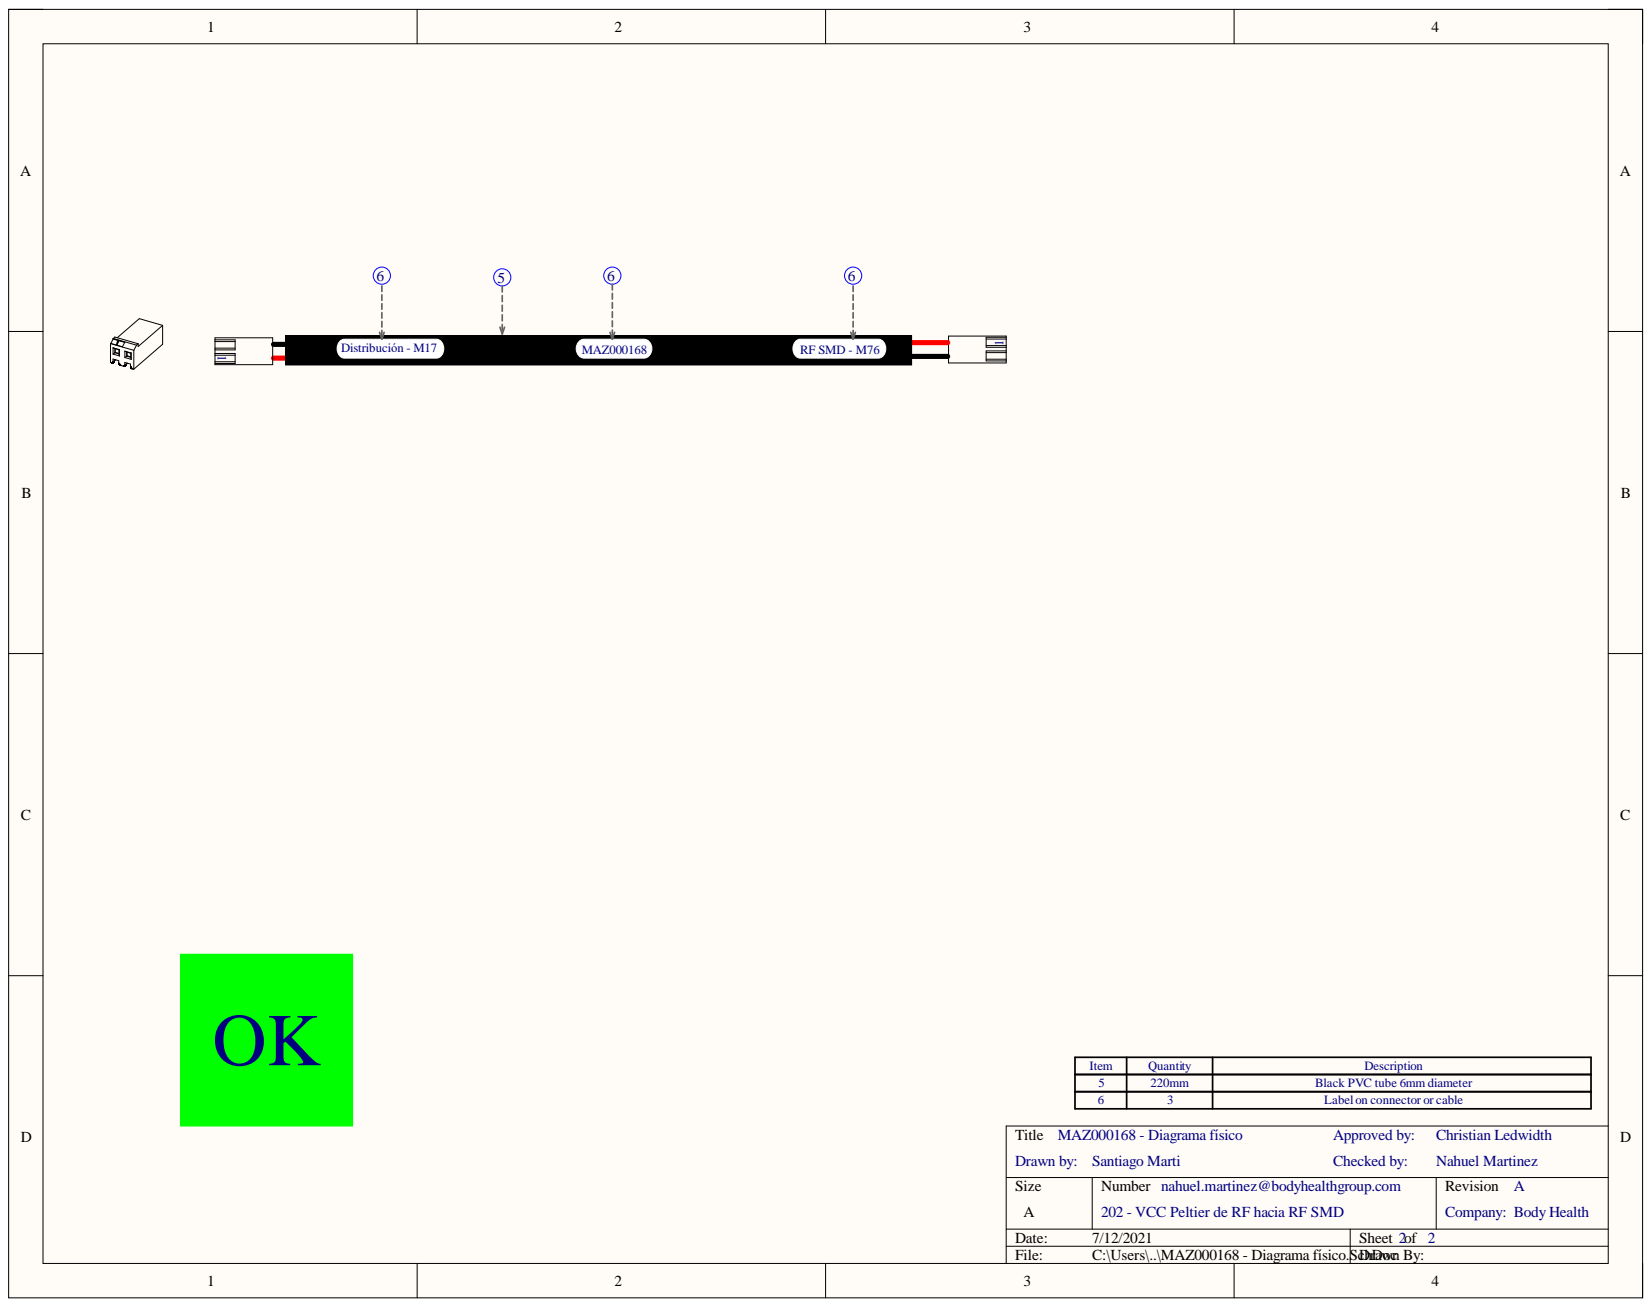
[picture p36: page 1]
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

Size A | Number nahuel.martinez@bodyhealthgroup.com 202 - VCC Peltier de RF hacia RF SMD | Revision A Company: Body Health

Date: 7/12/2021 | Sheet of 2 2
File: C:\Users\..\MAZ000168 - Diagrama físico.ScDrhDoawcn By:
