jnahuel-developer/Probador-de-cables/Cables/02. Terminados - PDF/MAZ000169 - Diagrama eléctrico.pdf

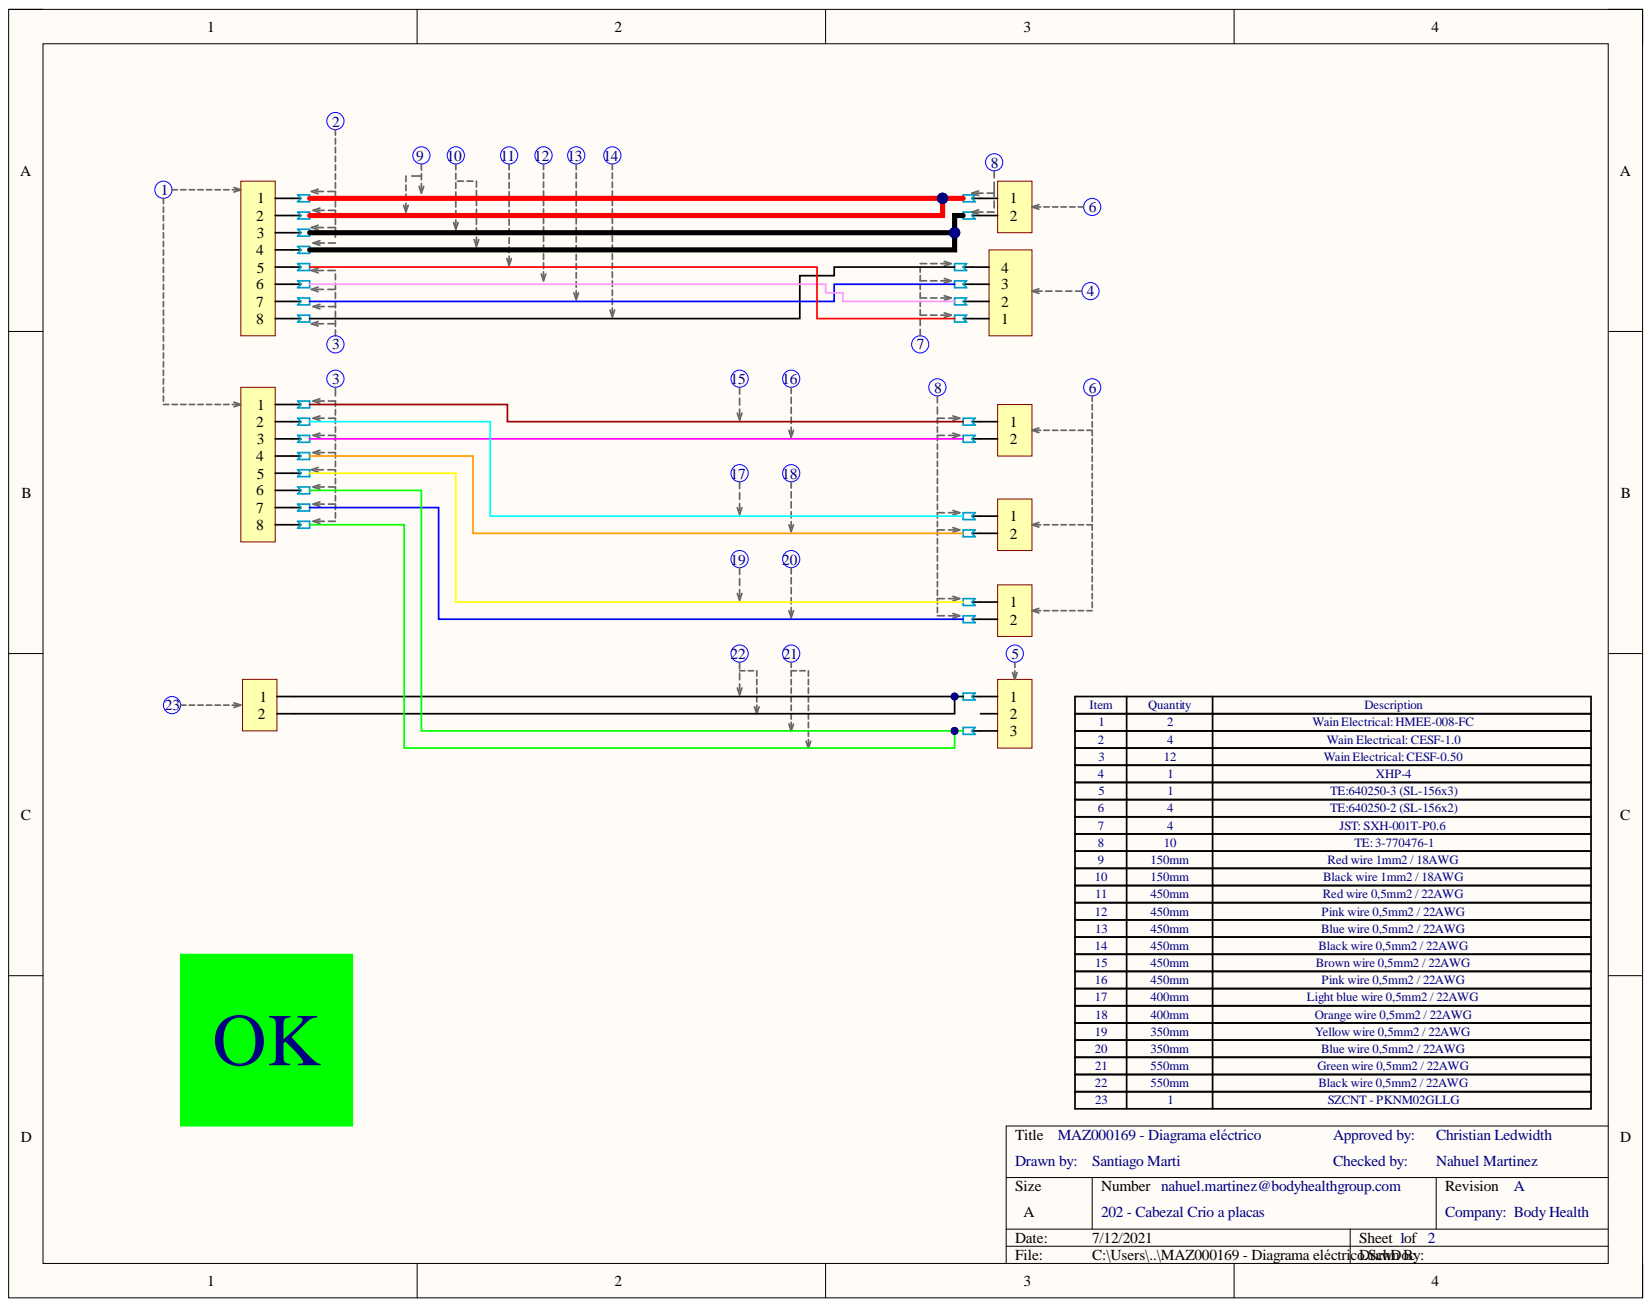
[picture p37: page 1]

Item | Quantity | Description
1 | 2 | Wain Electrical:HMEE-008-FC
2 | 4 | Wain Electrical: CESF-1.0
3 | 12 | Wain Electrical:CESF-0.50
4 | 1 | XHP-4
5 | 1 | TE:640250-3 (SL-156x3)
6 | 4 | TE:640250-2 (SL-156x2)
7 | 4 | JST: SXH-001T-P0.6
8 | 10 | TE: 3-770476-1
9 | 150mm | Red wire 1mm2 / 18AWG
10 | 150mm | Black wire 1mm2 / 18AWG
11 | 450mm | Red wire 0,5mm2 / 22AWG
12 | 450mm | Pink wire 0,5mm2 / 22AWG
13 | 450mm | Blue wire 0,5mm2 / 22AWG
14 | 450mm | Black wire 0,5mm2 / 22AWG

16 | 450mm | Pink wire 0,5mm2 / 22AWG
17 | 400mm | Light blue wire 0,5mm2 / 22AWG
18 | 400mm | Orange wire 0,5mm2 / 22AWG

20 | 350mm | Blue wire 0,5mm2 / 22AWG
21 | 550mm | Green wire 0,5mm2 / 22AWG

Size A | Number nahuel.martinez@bodyhealthgroup.com 202 - Cabezal Crio a placas | Revision A Company: Body Health

Date: 7/12/2021 | Sheet of 1 2
File: C:\Users\..\MAZ000169 - Diagrama eléctricoDr.ScawhDon Bcy:
