jnahuel-developer/Probador-de-cables/Cables/02. Terminados - PDF/MAZ000169 - Diagrama físico.pdf

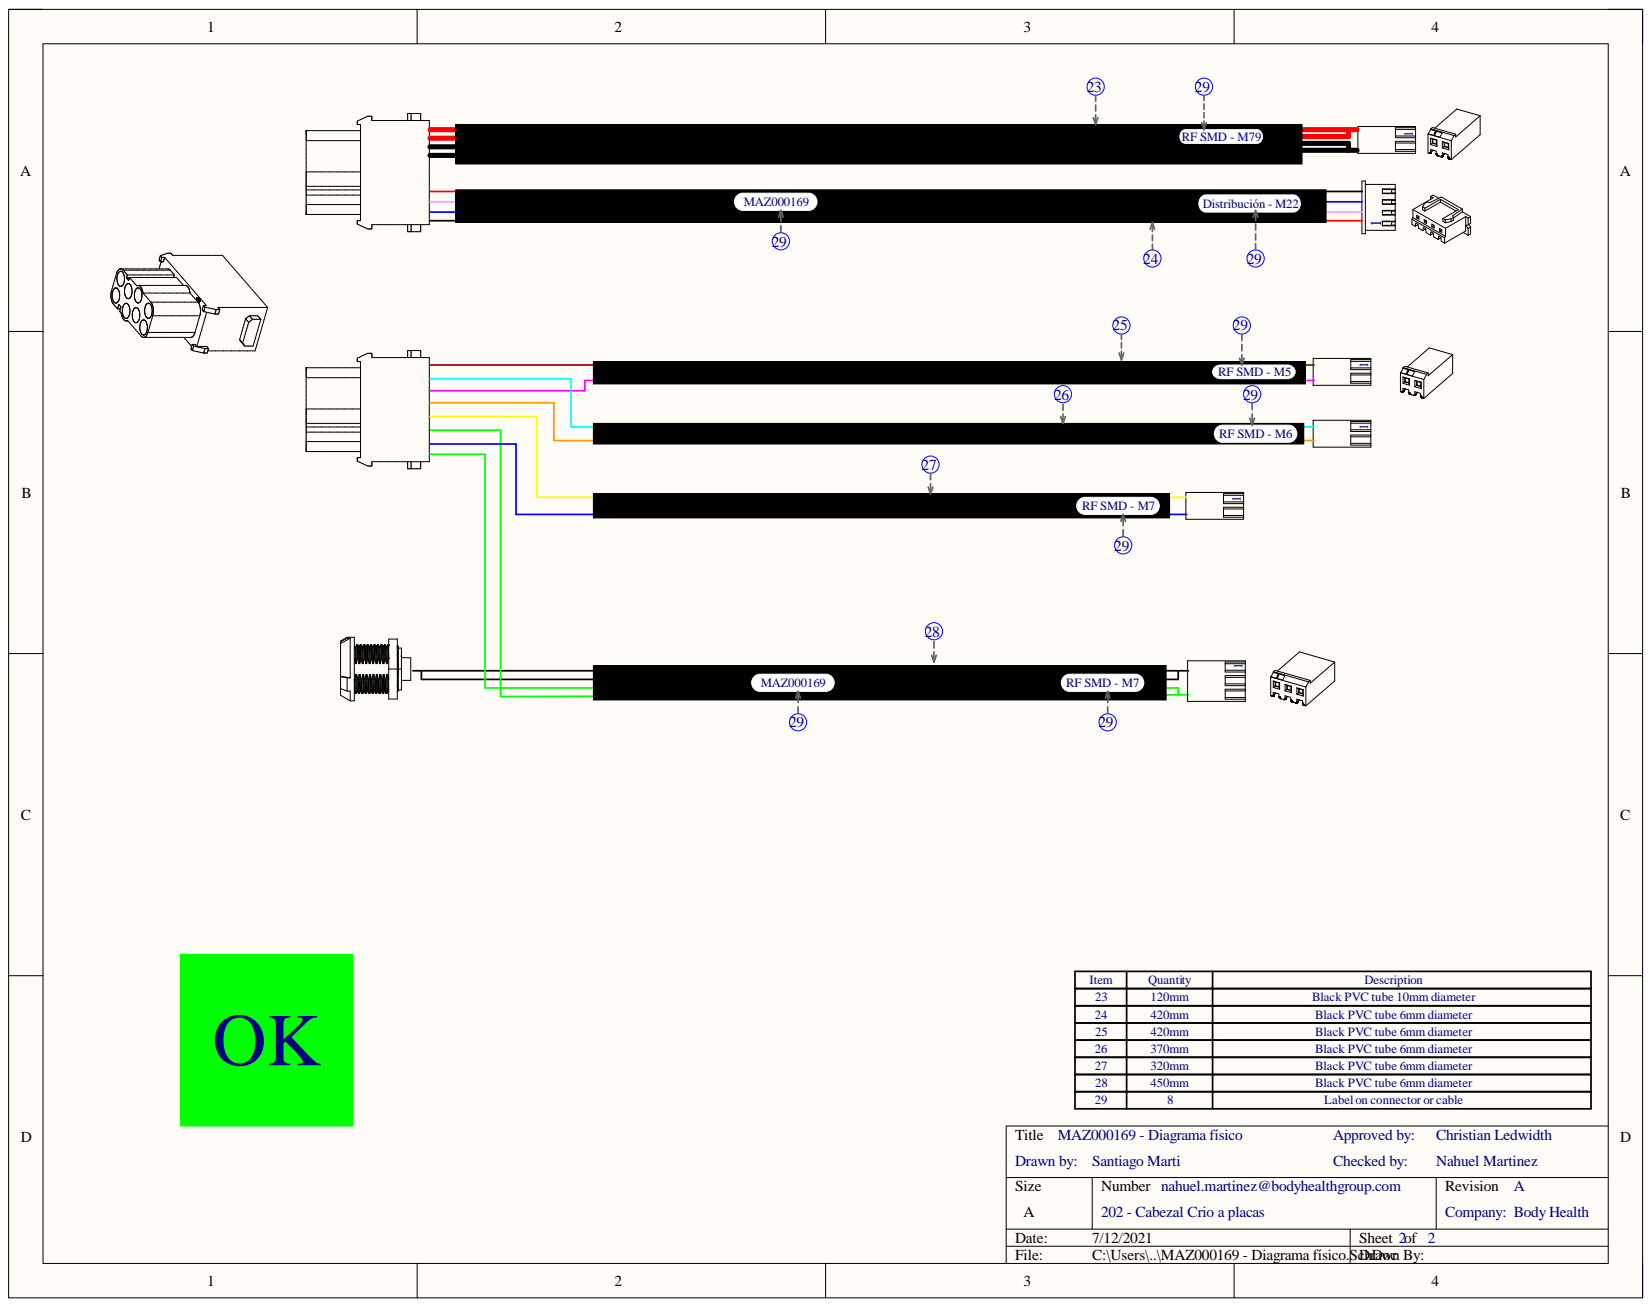
[picture p38: page 1]

MAZ000169

Distribución - M22

Item | Quantity | Description
23 | 120mm | Black PVC tube 10mm diameter
24 | 420mm | Black PVC tube 6mm diameter
25 | 420mm | Black PVC tube 6mm diameter

Black PVC tube 6mm diameter

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

Date: 7/12/2021 | Sheet of 2 2
File: C:\Users\..\MAZ000169 - Diagrama físico.ScDrhDoawcn By:
