jnahuel-developer/Probador-de-cables/Cables/02. Terminados - PDF/MAZ000170 - Diagrama eléctrico.pdf

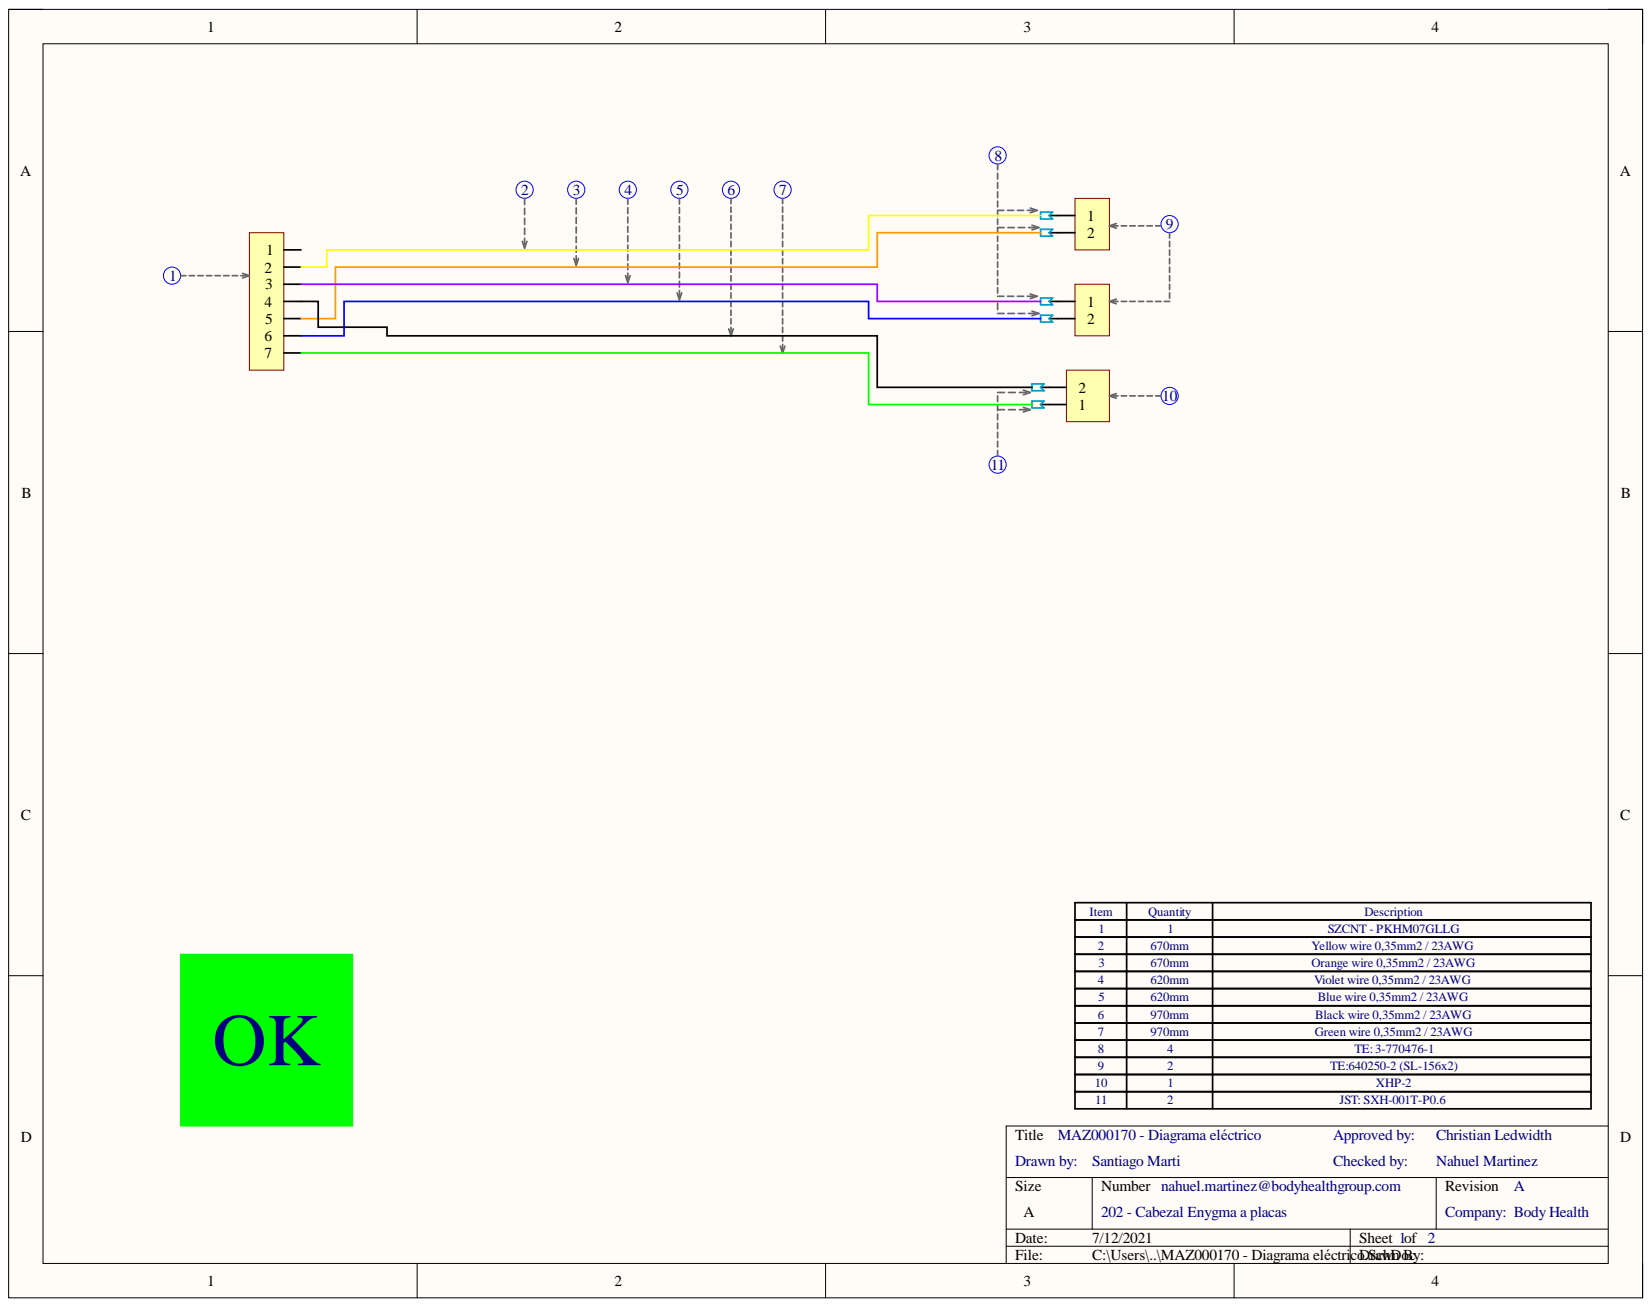
[picture p39: page 1]

Item | Quantity | Description
1 | 1 | SZCNT - PKHM07GLLG
2 | 670mm | Yellow wire 0,35mm2 / 23AWG

4 | 620mm | Violet wire 0,35mm2 / 23AWG
5 | 620mm | Blue wire 0,35mm2 / 23AWG
6 | 970mm | Black wire 0,35mm2 / 23AWG
7 | 970mm | Green wire 0,35mm2 / 23AWG
8 | 4 | TE: 3-770476-1
9 | 2 | TE:640250-2 (SL-156x2)
10 | 1 | XHP-2
11 | 2 | JST: SXH-001T-P0.6

Size A | Number nahuel.martinez@bodyhealthgroup.com 202 - Cabezal Enygma a placas | Revision A Company: Body Health

Date: 7/12/2021 | Sheet of 1 2
File: C:\Users\..\MAZ000170 - Diagrama eléctricoDr.ScawhDon Bcy:
