jnahuel-developer/Probador-de-cables/Cables/02. Terminados - PDF/MAZ000170 - Diagrama físico.pdf

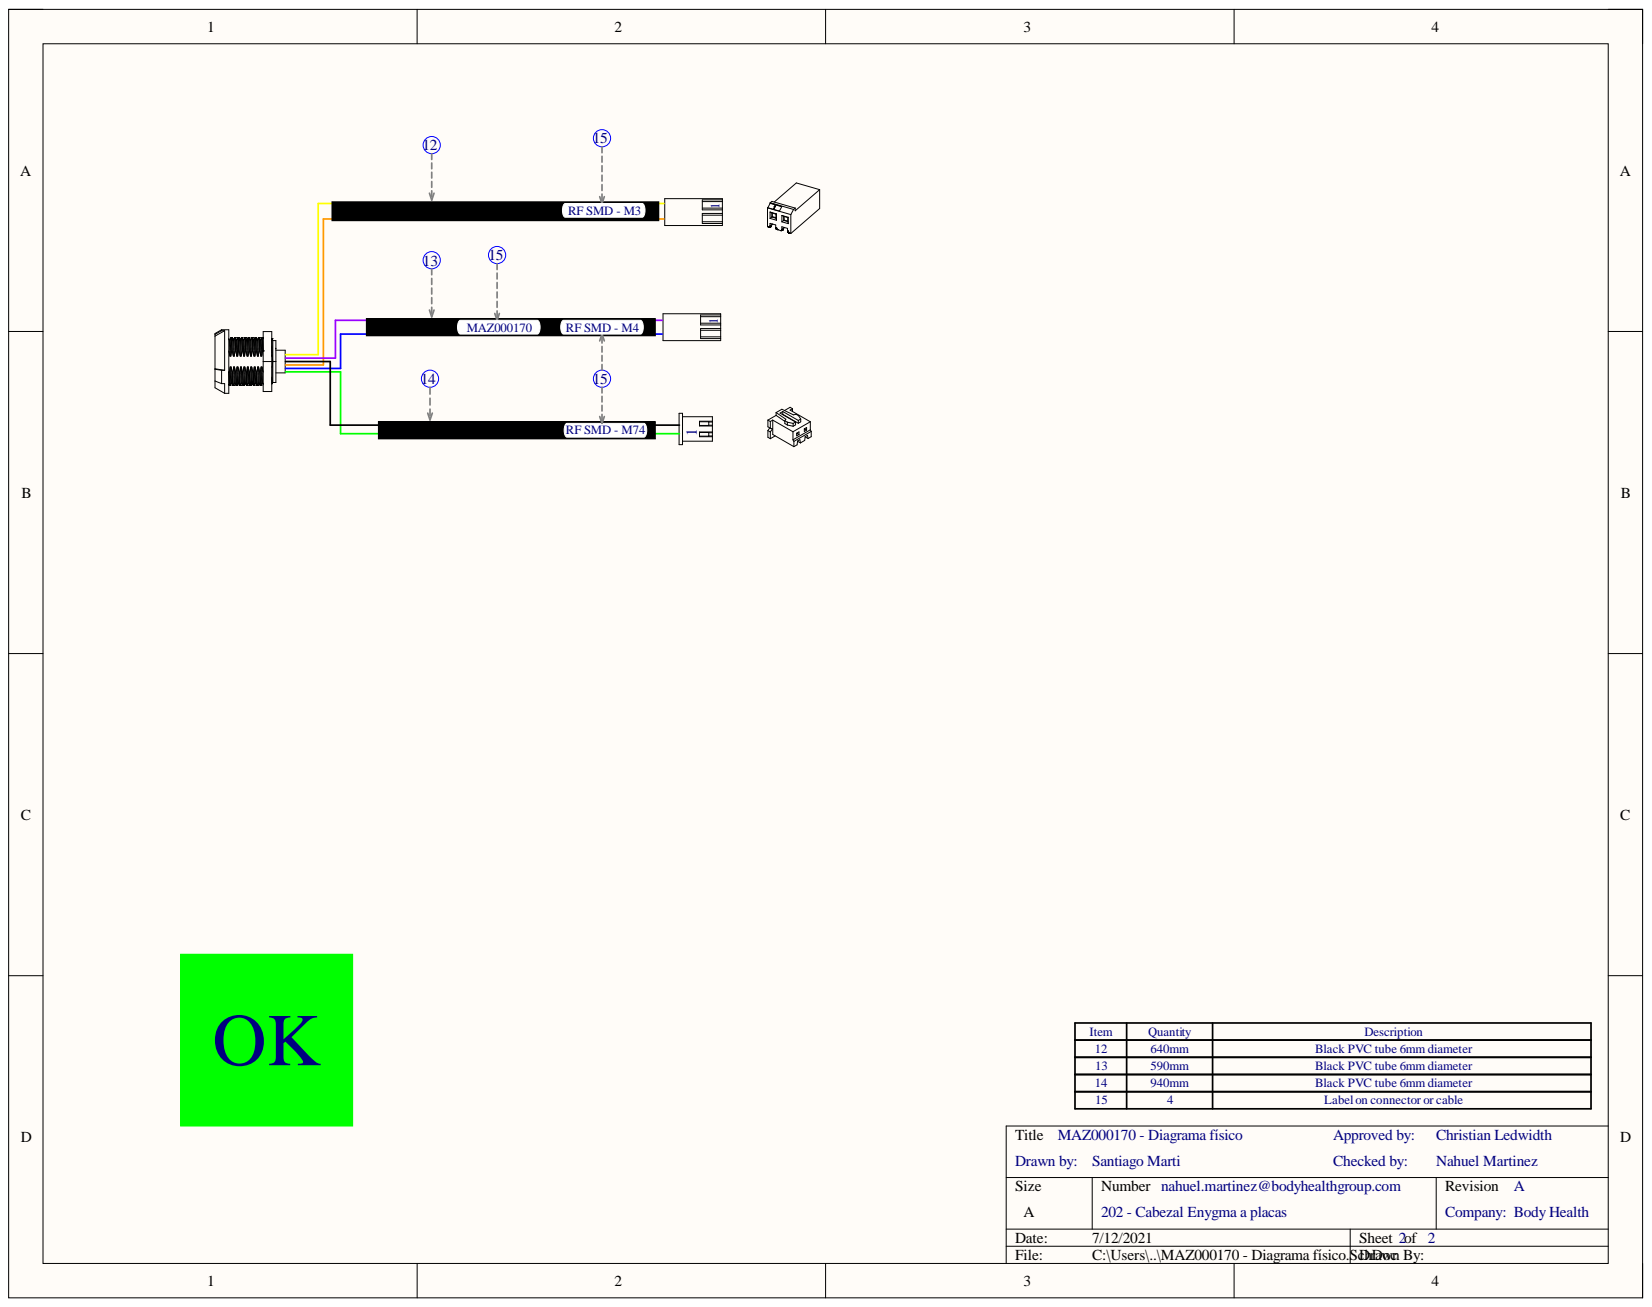
[picture p40: page 1]

Item | Quantity | Description
12 | 640mm | Black PVC tube 6mm diameter
13 | 590mm | Black PVC tube 6mm diameter
14 | 940mm | Black PVC tube 6mm diameter
15 | 4 | Label on connector or cable

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

Date: 7/12/2021 | Sheet of 2 2
File: C:\Users\..\MAZ000170 - Diagrama físico.ScDrhDoawcn By:
