jnahuel-developer/Probador-de-cables/Cables/02. Terminados - PDF/MAZ000171 - Diagrama eléctrico.pdf

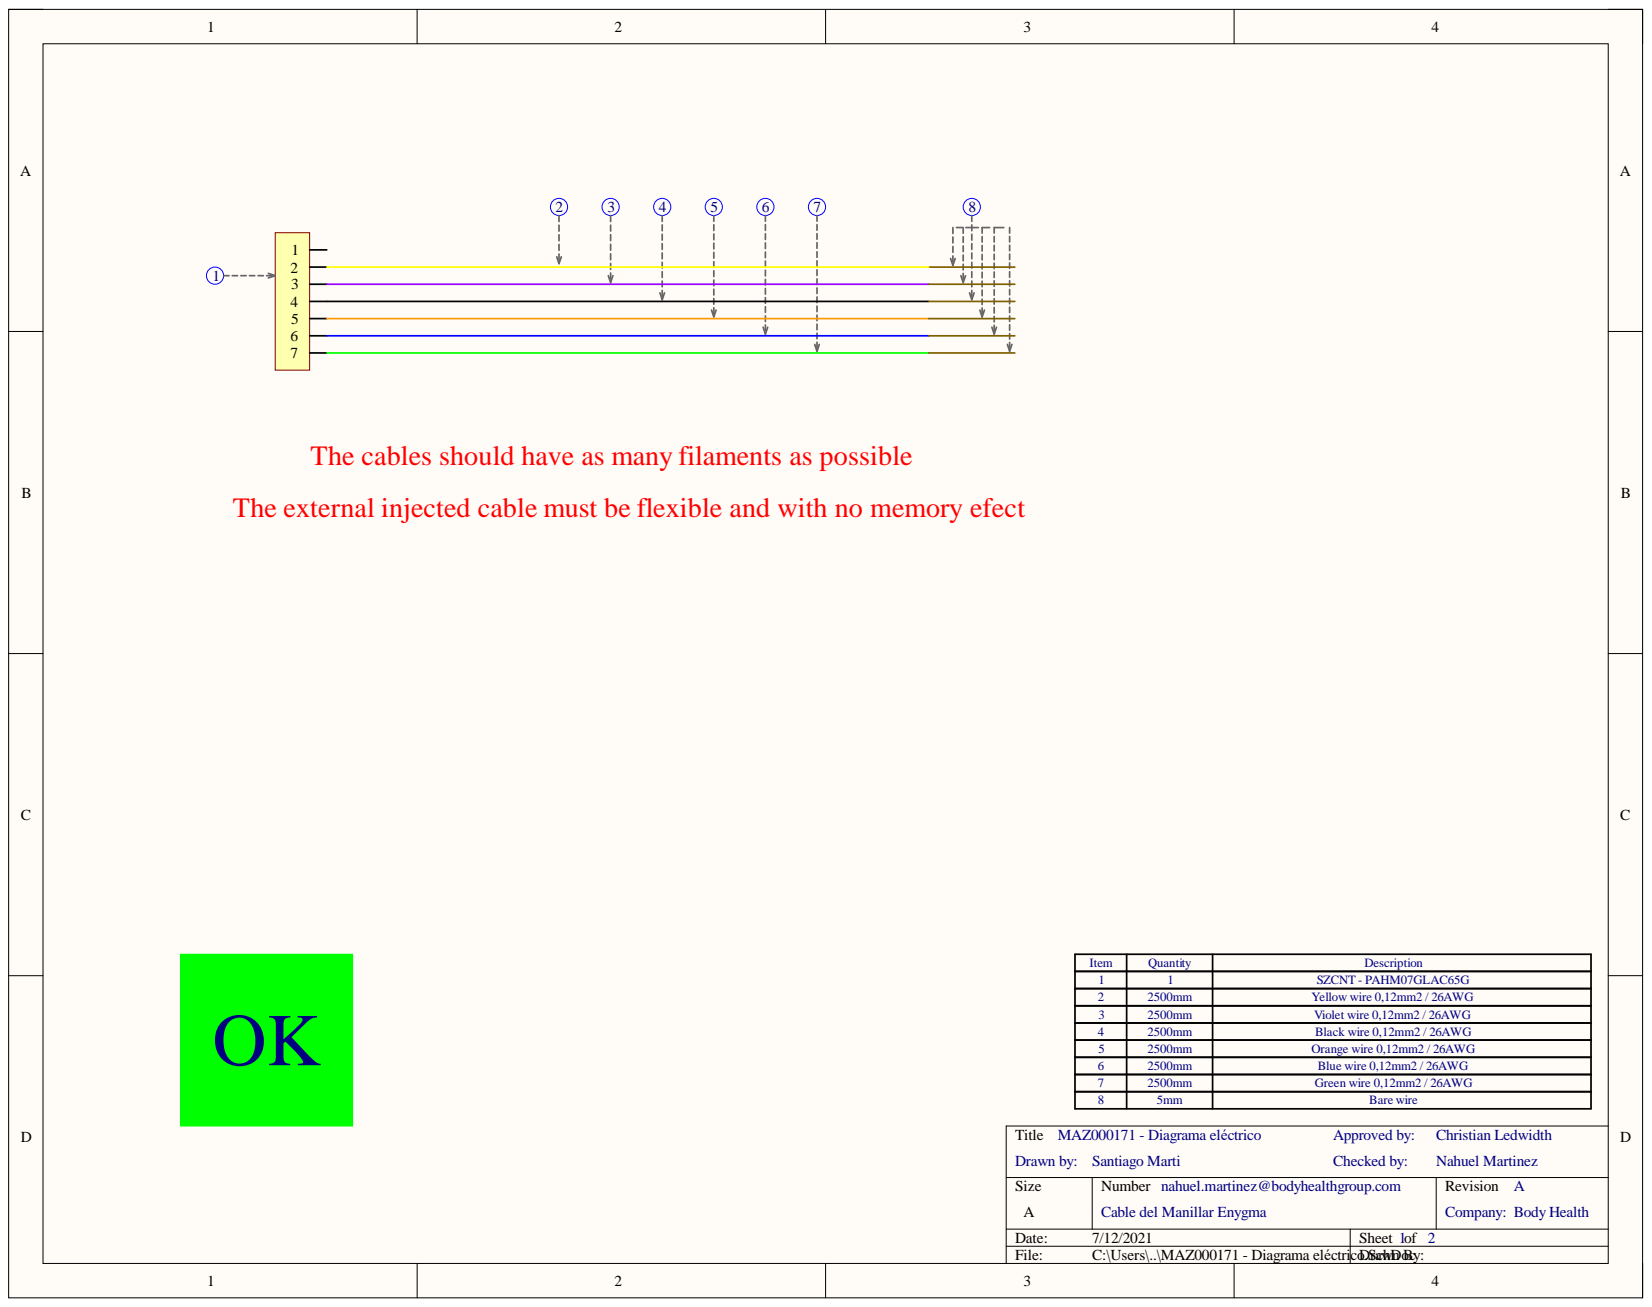
[picture p41: page 1]

The cables should have as many filaments as possible

The external injected cable must be flexible and with no memory efect

1 | 1 | SZCNT - PAHM07GLAC65G
2 | 2500mm | Yellow wire 0,12mm2 / 26AWG
3 | 2500mm | Violet wire 0,12mm2 / 26AWG
4 | 2500mm | Black wire 0,12mm2 / 26AWG
5 | 2500mm | Orange wire 0,12mm2 / 26AWG
6 | 2500mm | Blue wire 0,12mm2 / 26AWG
7 | 2500mm | Green wire 0,12mm2 / 26AWG
8 | 5mm | Bare wire

Size A | Number nahuel.martinez@bodyhealthgroup.com Cable del Manillar Enygma | Revision A Company: Body Health

Date: 7/12/2021 | Sheet of 1 2
File: C:\Users\..\MAZ000171 - Diagrama eléctricoDr.ScawhDon Bcy:
