jnahuel-developer/Probador-de-cables/Cables/02. Terminados - PDF/MAZ000171 - Diagrama físico.pdf

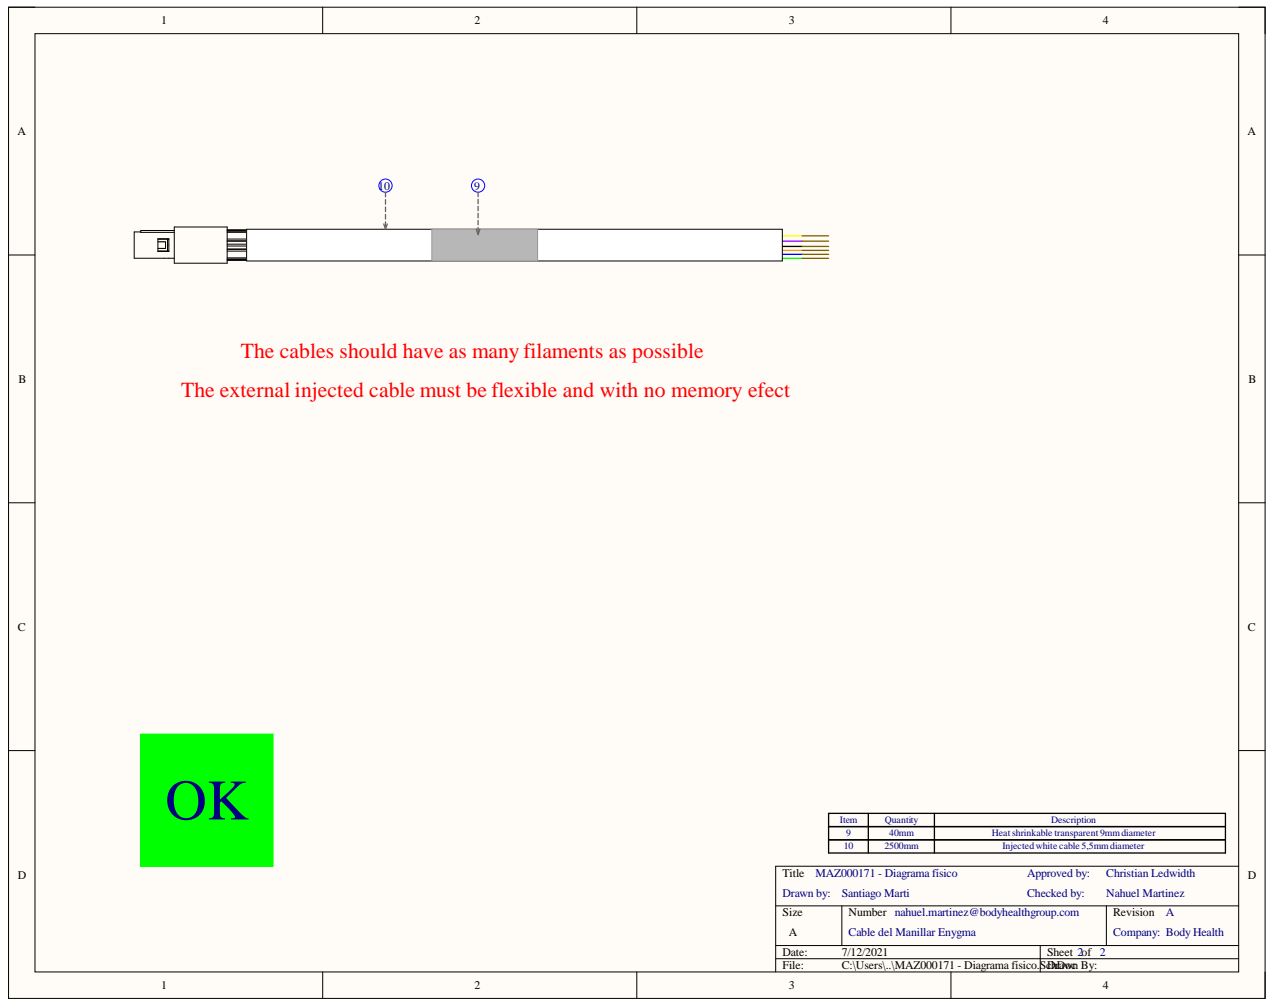
[picture p42: page 1]

The cables should have as many filaments as possible

The external injected cable must be flexible and with no memory efect

Item | Quantity | Description
9 | 40mm | Heatshrinkable transparent 9mmdiameter
10 | 2500mm | Injected white cable 5,5mmdiameter

Size A | Number nahuel.martinez@bodyhealthgroup.com Cable del Manillar Enygma | Revision A Company: Body Health

Date: 7/12/2021 | Sheet of 2 2
File: C:\Users\..\MAZ000171 - Diagrama físico.ScDrhDoawcn By:
