jnahuel-developer/Probador-de-cables/Cables/02. Terminados - PDF/MAZ000172 - Diagrama eléctrico.pdf

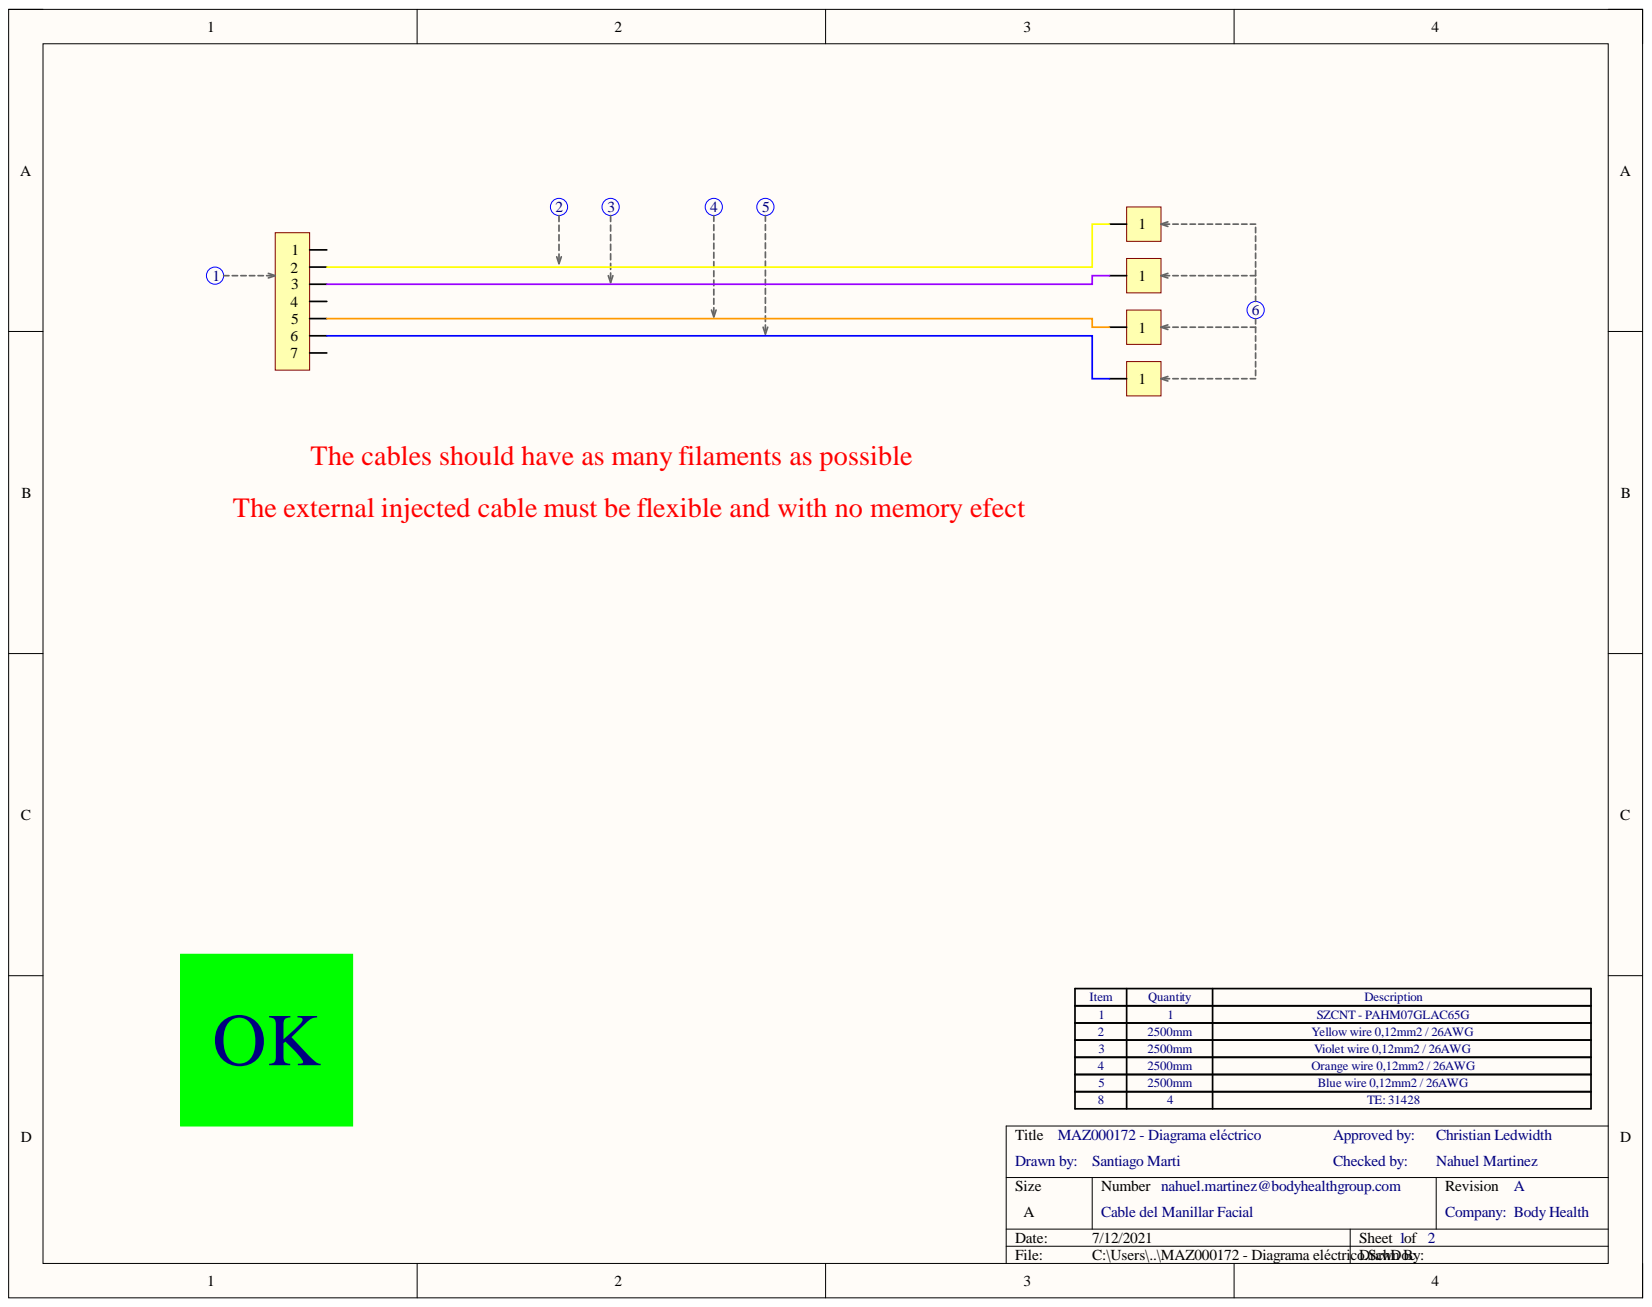
[picture p43: page 1]

The cables should have as many filaments as possible

The external injected cable must be flexible and with no memory efect

Item | Quantity | Description
1 | 1 | SZCNT - PAHM07GLAC65G
2 | 2500mm | Yellow wire 0,12mm2 / 26AWG
3 | 2500mm | Violet wire 0,12mm2 / 26AWG
4 | 2500mm | Orange wire 0,12mm2 / 26AWG
5 | 2500mm | Blue wire 0,12mm2 / 26AWG
8 | 4 | TE: 31428

Size A | Number nahuel.martinez@bodyhealthgroup.com Cable del Manillar Facial | Revision A Company: Body Health

Date: 7/12/2021 | Sheet of 1 2
File: C:\Users\..\MAZ000172 - Diagrama eléctricoDr.ScawhDon Bcy:
