jnahuel-developer/Probador-de-cables/Cables/02. Terminados - PDF/MAZ000173 - Diagrama eléctrico.pdf

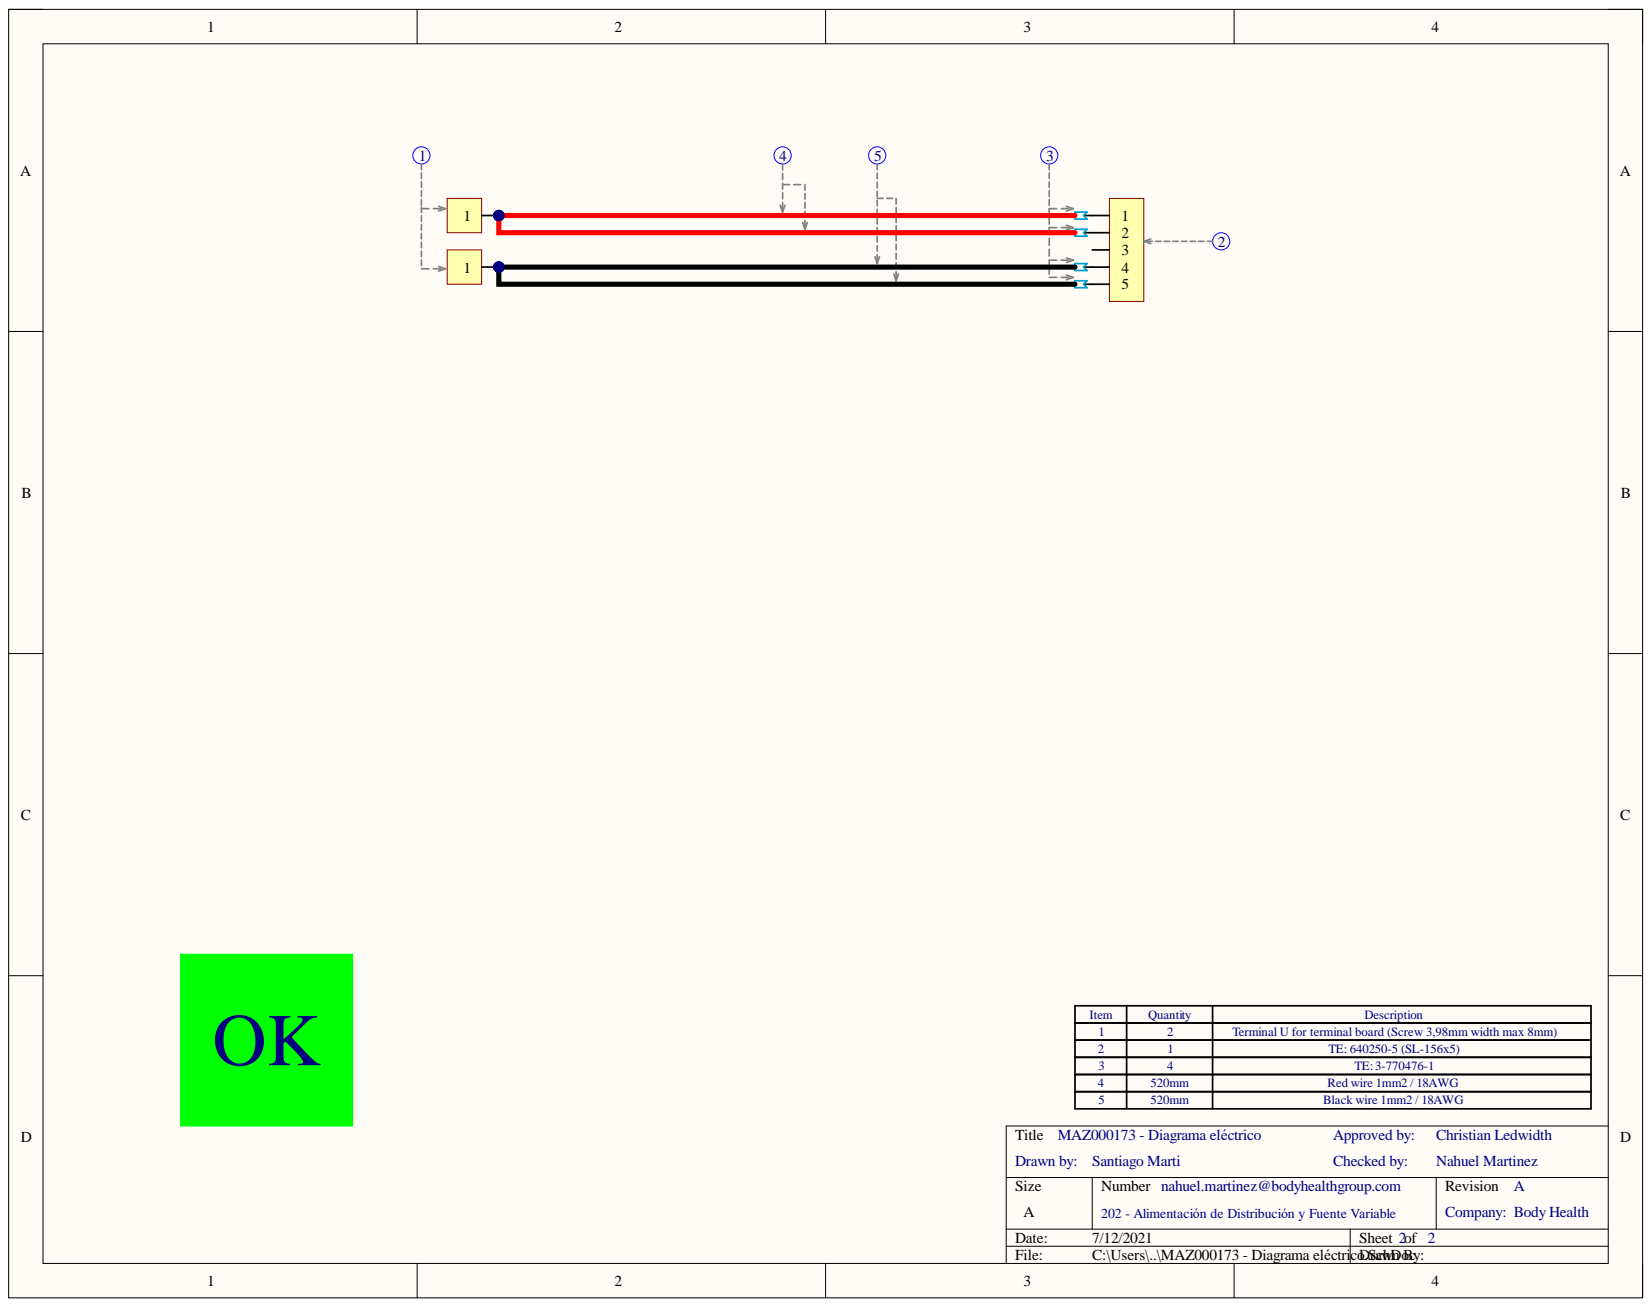
[picture p44: page 1]

Item | Quantity | Description
1 | 2 | Terminal U for terminal board (Screw 3,98mm width max 8mm)
2 | 1 | TE: 640250-5 (SL-156x5)
3 | 4 | TE: 3-770476-1
4 | 520mm | Red wire 1mm2 / 18AWG
5 | 520mm | Black wire 1mm2 / 18AWG

Size A | Number nahuel.martinez@bodyhealthgroup.com 202 - Alimentación de Distribución y Fuente Variable | Revision A Company: Body Health

Date: 7/12/2021 | Sheet of 2 2
File: C:\Users\..\MAZ000173 - Diagrama eléctricoDr.ScawhDon Bcy:
