jnahuel-developer/Probador-de-cables/Cables/02. Terminados - PDF/MAZ000173 - Diagrama físico.pdf

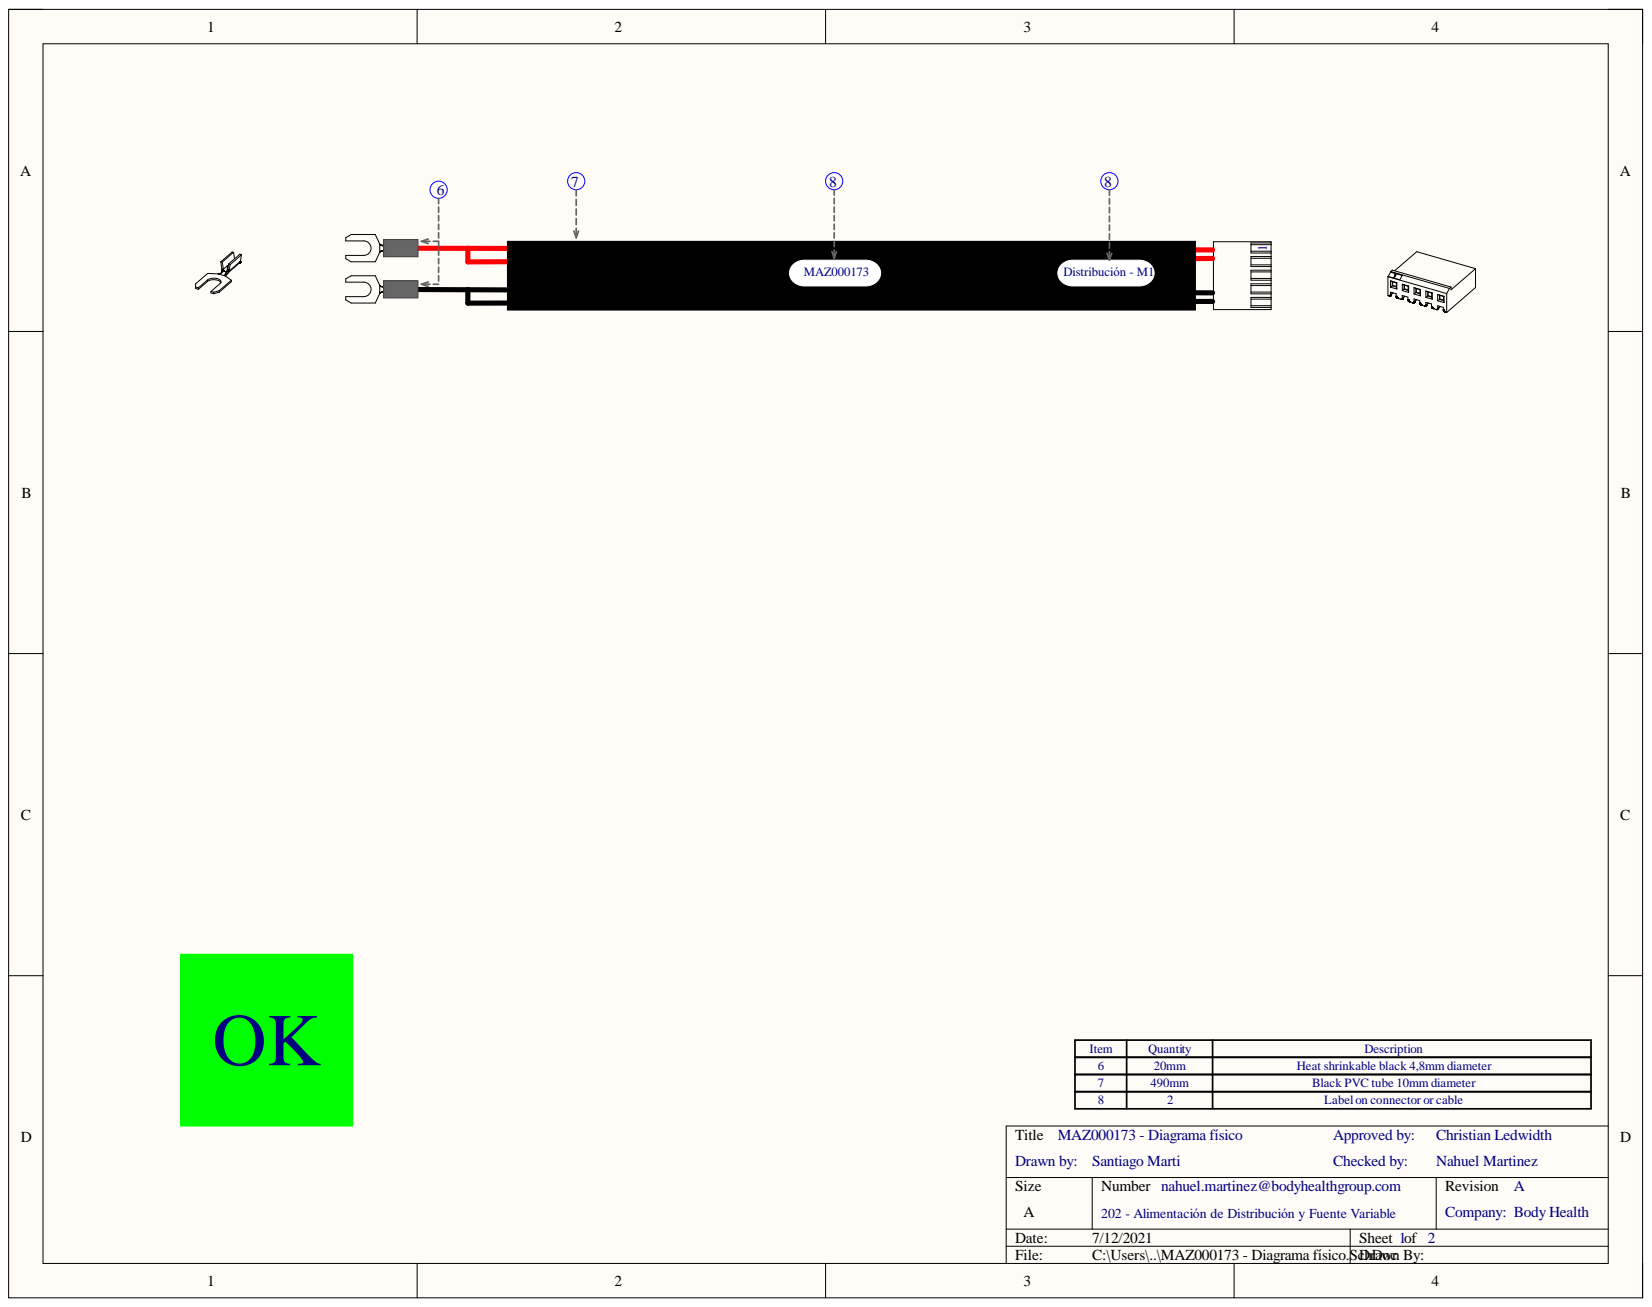
[picture p45: page 1]

Item | Quantity | Description
6 | 20mm | Heat shrinkable black 4,8mm diameter
7 | 490mm | Black PVC tube 10mm diameter
8 | 2 | Label on connector or cable

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

Date: 7/12/2021 | Sheet of 1 2
File: C:\Users\..\MAZ000173 - Diagrama físico.ScDrhDoawcn By:
