jnahuel-developer/Probador-de-cables/Cables/02. Terminados - PDF/MAZ000174 - Diagrama eléctrico.pdf

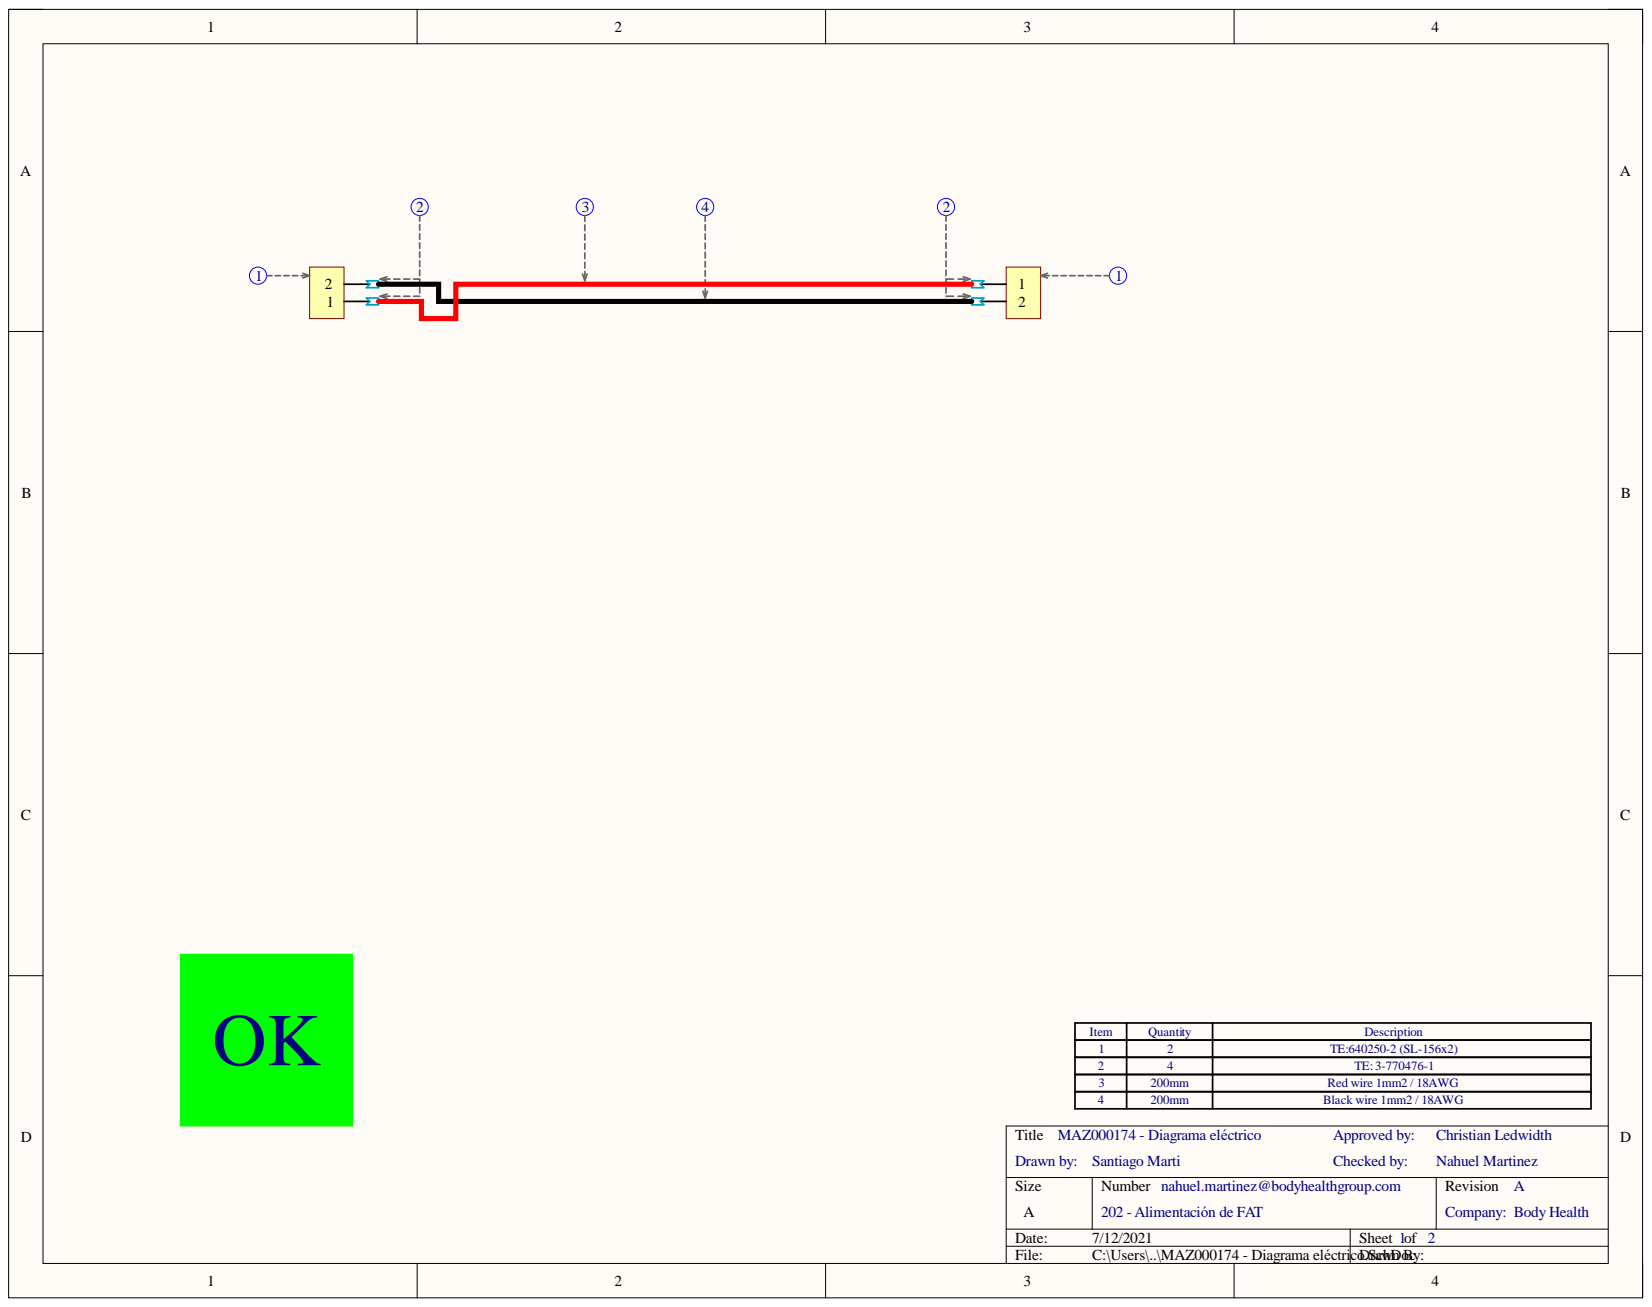
[picture p46: page 1]

Item | Quantity | Description
1 | 2 | TE:640250-2 (SL-156x2)
2 | 4 | TE: 3-770476-1
3 | 200mm | Red wire 1mm2 / 18AWG
4 | 200mm | Black wire 1mm2 / 18AWG

Size A | Number nahuel.martinez@bodyhealthgroup.com 202 - Alimentación de FAT | Revision A Company: Body Health

Date: 7/12/2021 | Sheet of 1 2
File: C:\Users\..\MAZ000174 - Diagrama eléctricoDr.ScawhDon Bcy:
