jnahuel-developer/Probador-de-cables/Cables/02. Terminados - PDF/MAZ000175 - Diagrama eléctrico.pdf

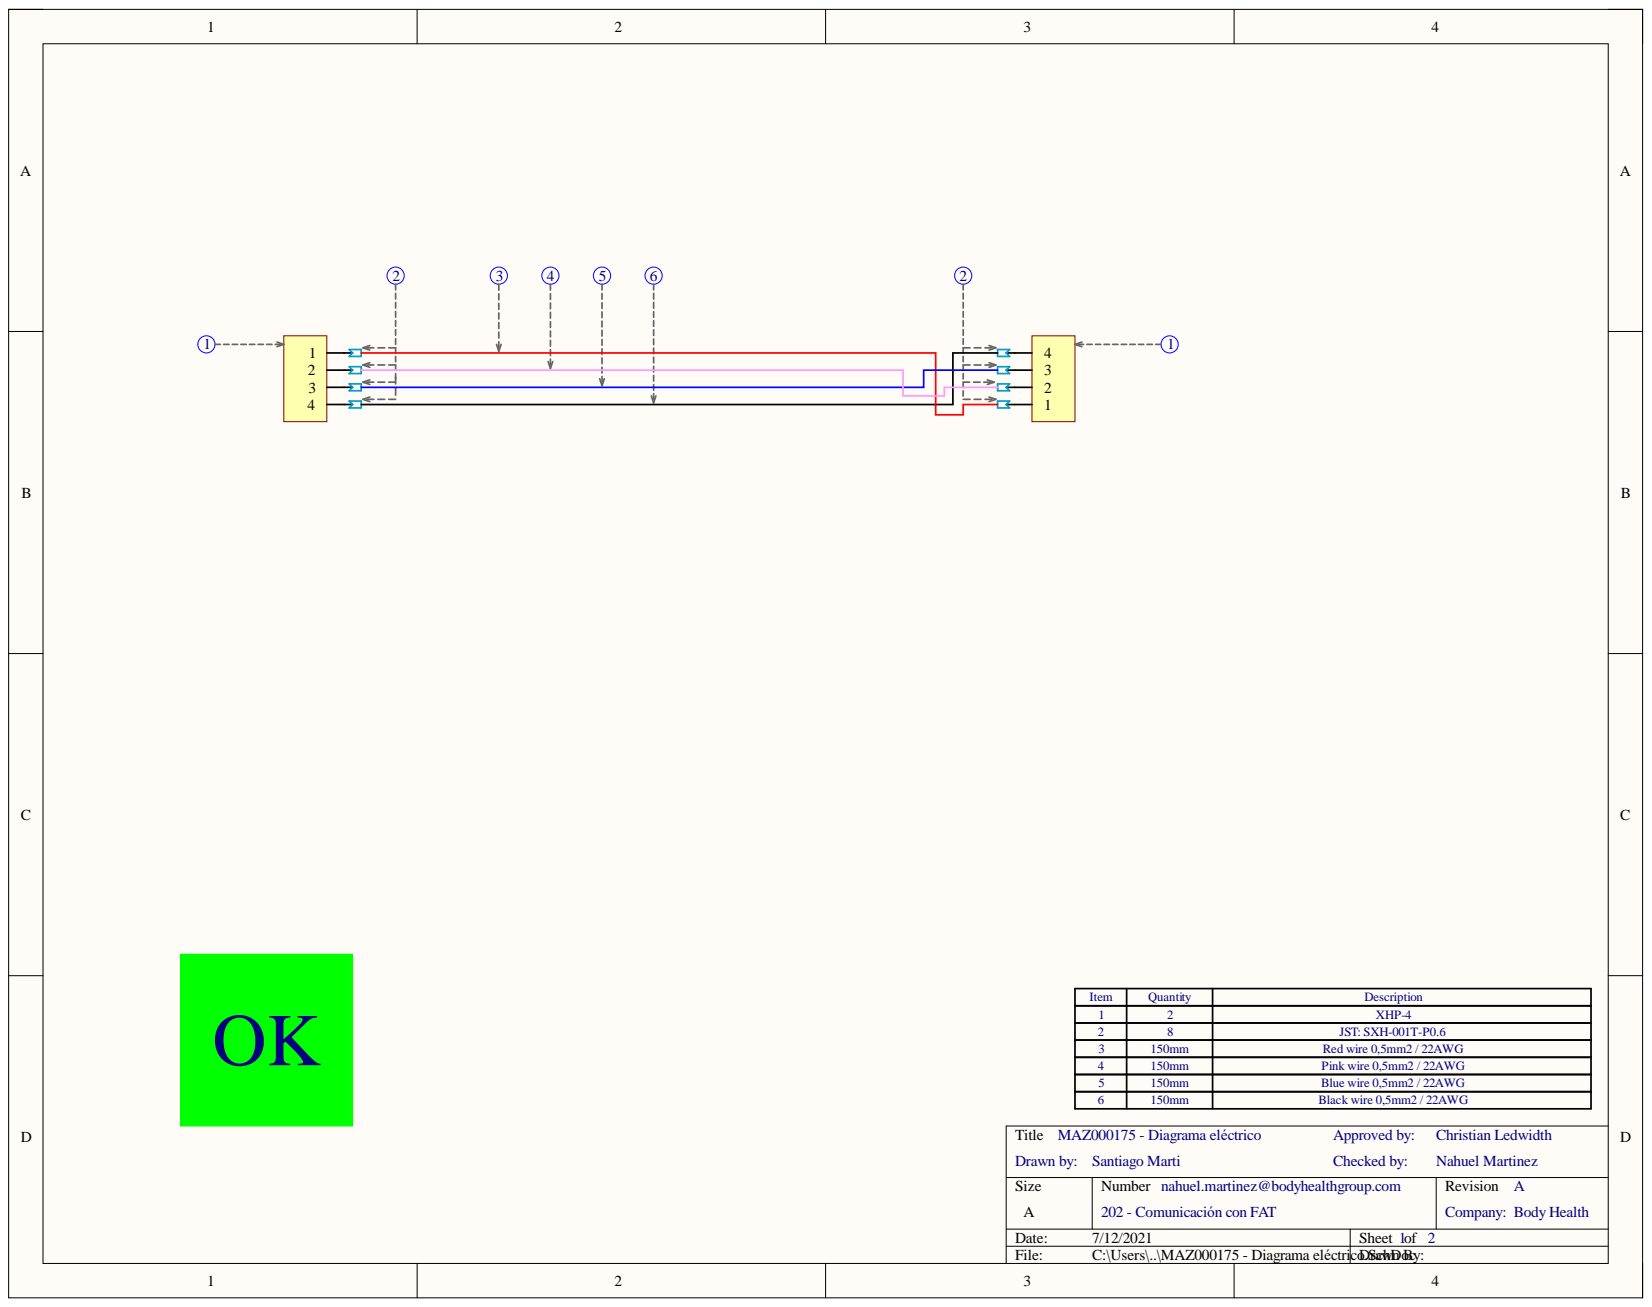
[picture p47: page 1]

Item | Quantity | Description
1 | 2 | XHP-4
2 | 8 | JST: SXH-001T-P0.6
3 | 150mm | Red wire 0,5mm2 / 22AWG
4 | 150mm | Pink wire 0,5mm2 / 22AWG
5 | 150mm | Blue wire 0,5mm2 / 22AWG
6 | 150mm | Black wire 0,5mm2 / 22AWG

Size A | Number nahuel.martinez@bodyhealthgroup.com 202 - Comunicación con FAT | Revision A Company: Body Health

Date: 7/12/2021 | Sheet of 1 2
File: C:\Users\..\MAZ000175 - Diagrama eléctricoDr.ScawhDon Bcy:
