jnahuel-developer/Probador-de-cables/Cables/02. Terminados - PDF/MAZ000175 - Diagrama físico.pdf

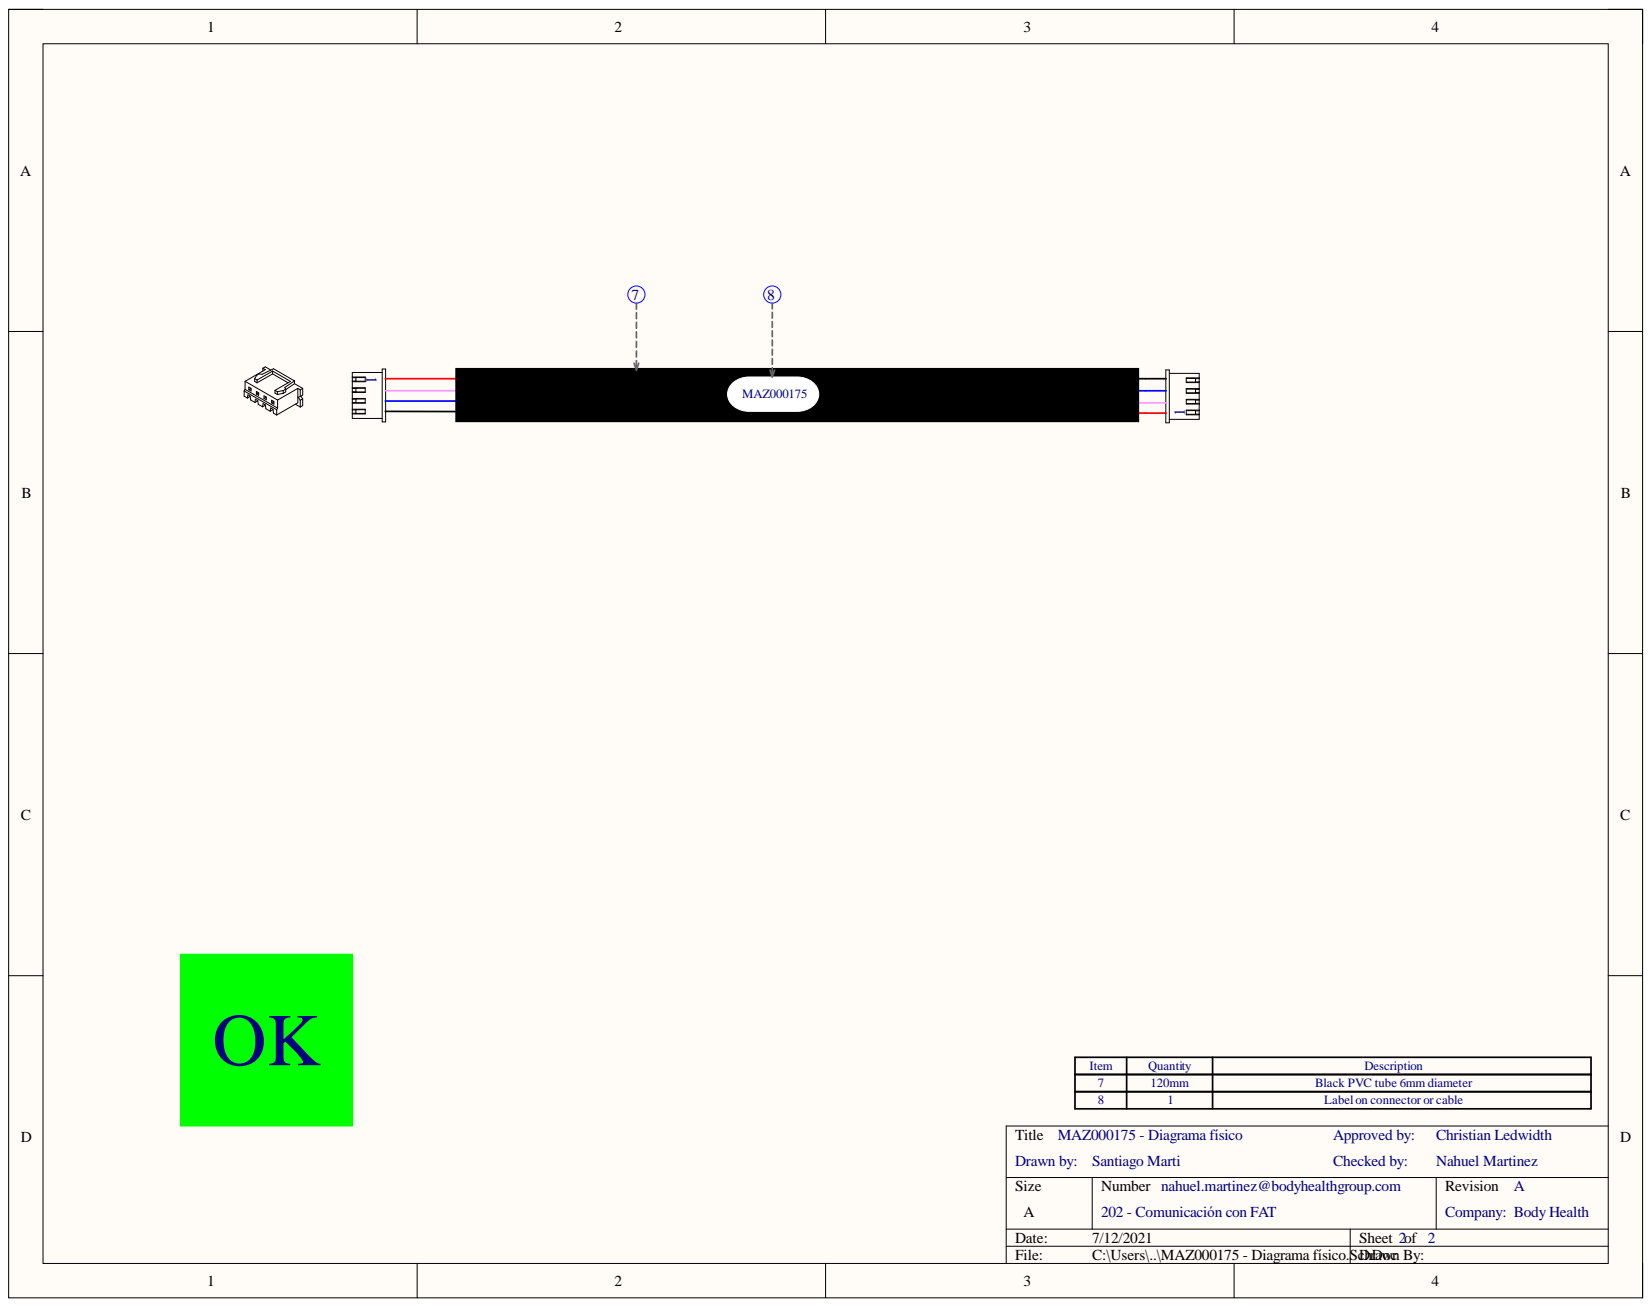
[picture p48: page 1]

Item | Quantity | Description
7 | 120mm | Black PVC tube 6mm diameter
8 | 1 | Label on connector or cable

Size A | Number nahuel.martinez@bodyhealthgroup.com 202 - Comunicación con FAT | Revision A Company: Body Health

Date: 7/12/2021 | Sheet of 2 2
File: C:\Users\..\MAZ000175 - Diagrama físico.ScDrhDoawcn By:
