jnahuel-developer/Probador-de-cables/Cables/02. Terminados - PDF/MAZ000176 - Diagrama eléctrico.pdf

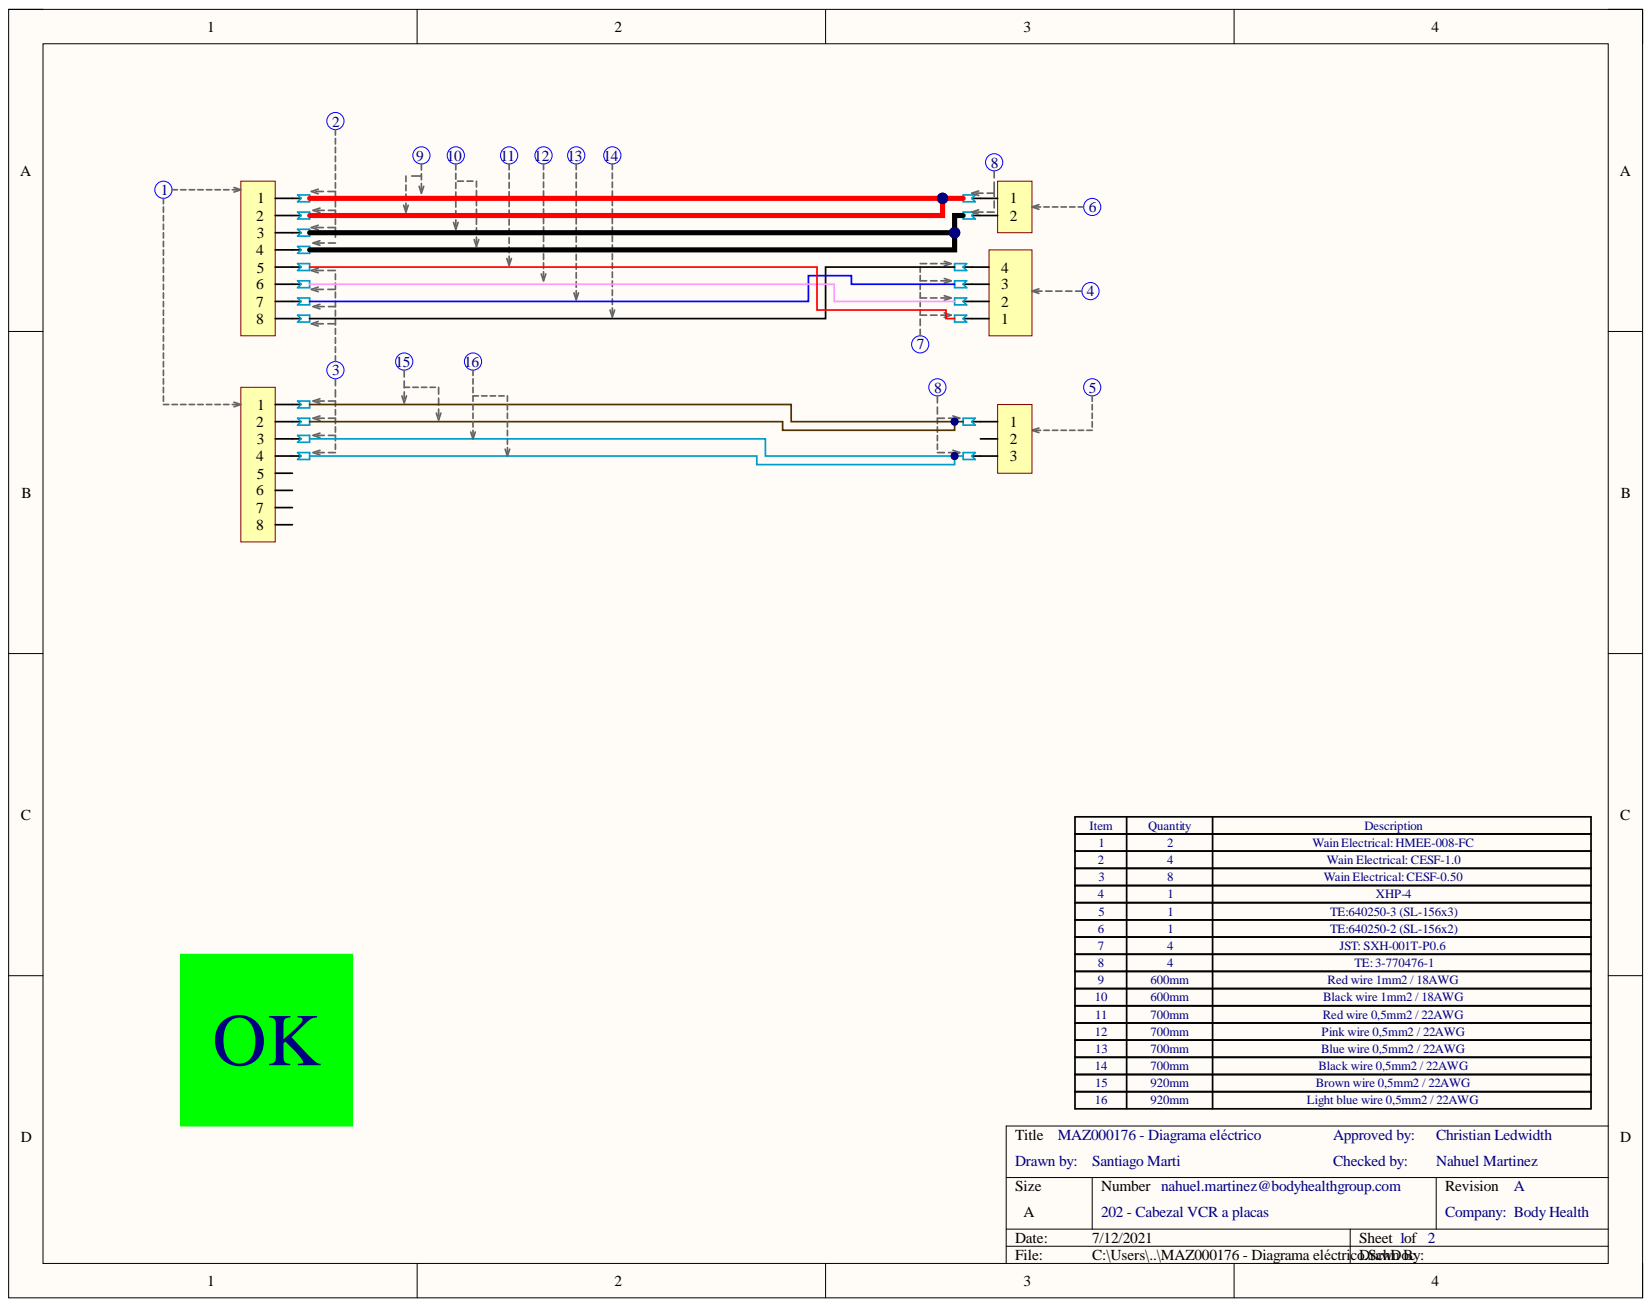
[picture p49: page 1]

Item | Quantity | Description
1 | 2 | Wain Electrical:HMEE-008-FC
2 | 4 | Wain Electrical: CESF-1.0
3 | 8 | Wain Electrical:CESF-0.50
4 | 1 | XHP-4
5 | 1 | TE:640250-3 (SL-156x3)
6 | 1 | TE:640250-2 (SL-156x2)
7 | 4 | JST: SXH-001T-P0.6

9 | 600mm | Red wire 1mm2 / 18AWG
10 | 600mm | Black wire 1mm2 / 18AWG
11 | 700mm | Red wire 0,5mm2 / 22AWG
12 | 700mm | Pink wire 0,5mm2 / 22AWG
13 | 700mm | Blue wire 0,5mm2 / 22AWG
14 | 700mm | Black wire 0,5mm2 / 22AWG
15 | 920mm | Brown wire 0,5mm2 / 22AWG
16 | 920mm | Light blue wire 0,5mm2 / 22AWG

Size A | Number nahuel.martinez@bodyhealthgroup.com 202 - Cabezal VCR a placas | Revision A Company: Body Health

Date: 7/12/2021 | Sheet of 1 2
File: C:\Users\..\MAZ000176 - Diagrama eléctricoDr.ScawhDon Bcy:
