jnahuel-developer/Probador-de-cables/Cables/02. Terminados - PDF/MAZ000176 - Diagrama físico.pdf

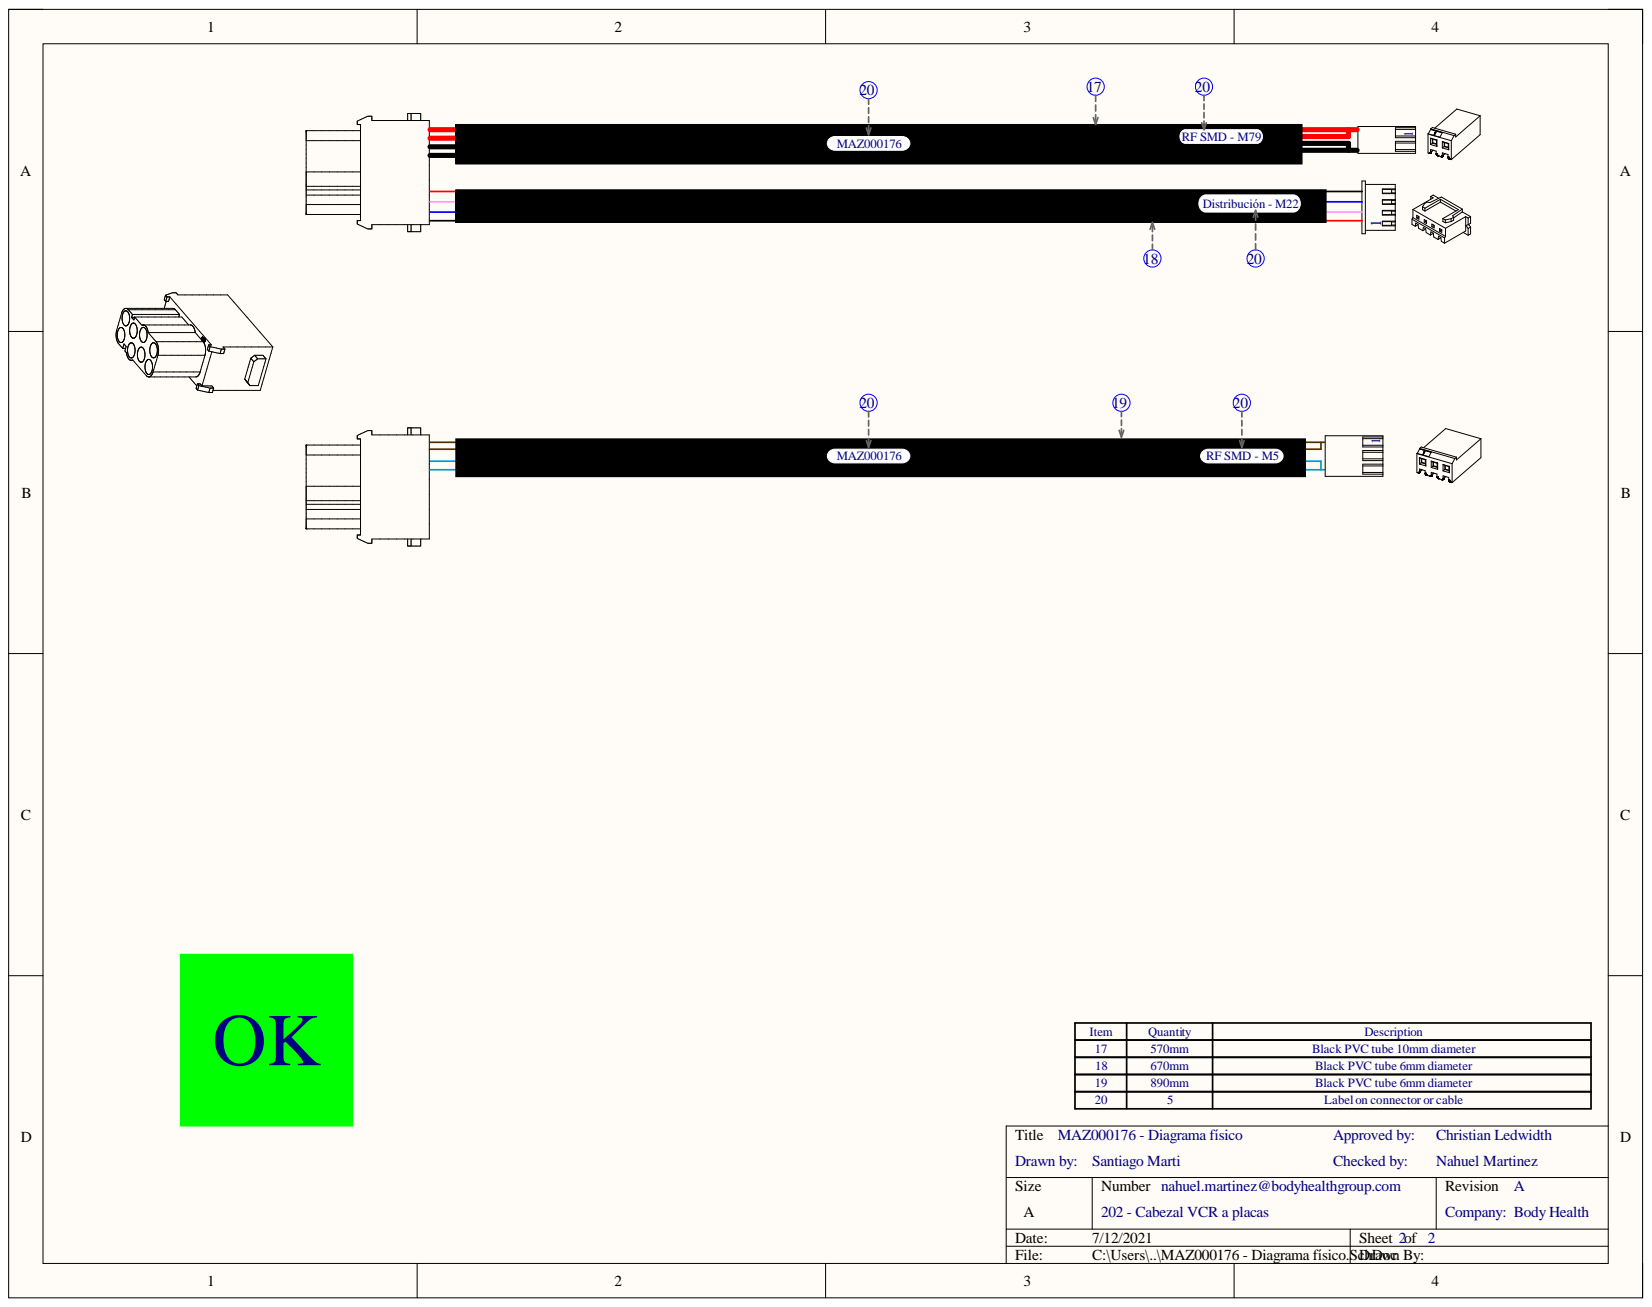
[picture p50: page 1]

RF SMD - M79

MAZ000176

Item | Quantity | Description
17 | 570mm | Black PVC tube 10mm diameter
18 | 670mm | Black PVC tube 6mm diameter
19 | 890mm | Black PVC tube 6mm diameter
20 | 5 | Label on connector or cable

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

Date: 7/12/2021 | Sheet of 2 2
File: C:\Users\..\MAZ000176 - Diagrama físico.ScDrhDoawcn By:
