jnahuel-developer/Probador-de-cables/Cables/02. Terminados - PDF/MAZ000177 - Diagrama eléctrico.pdf

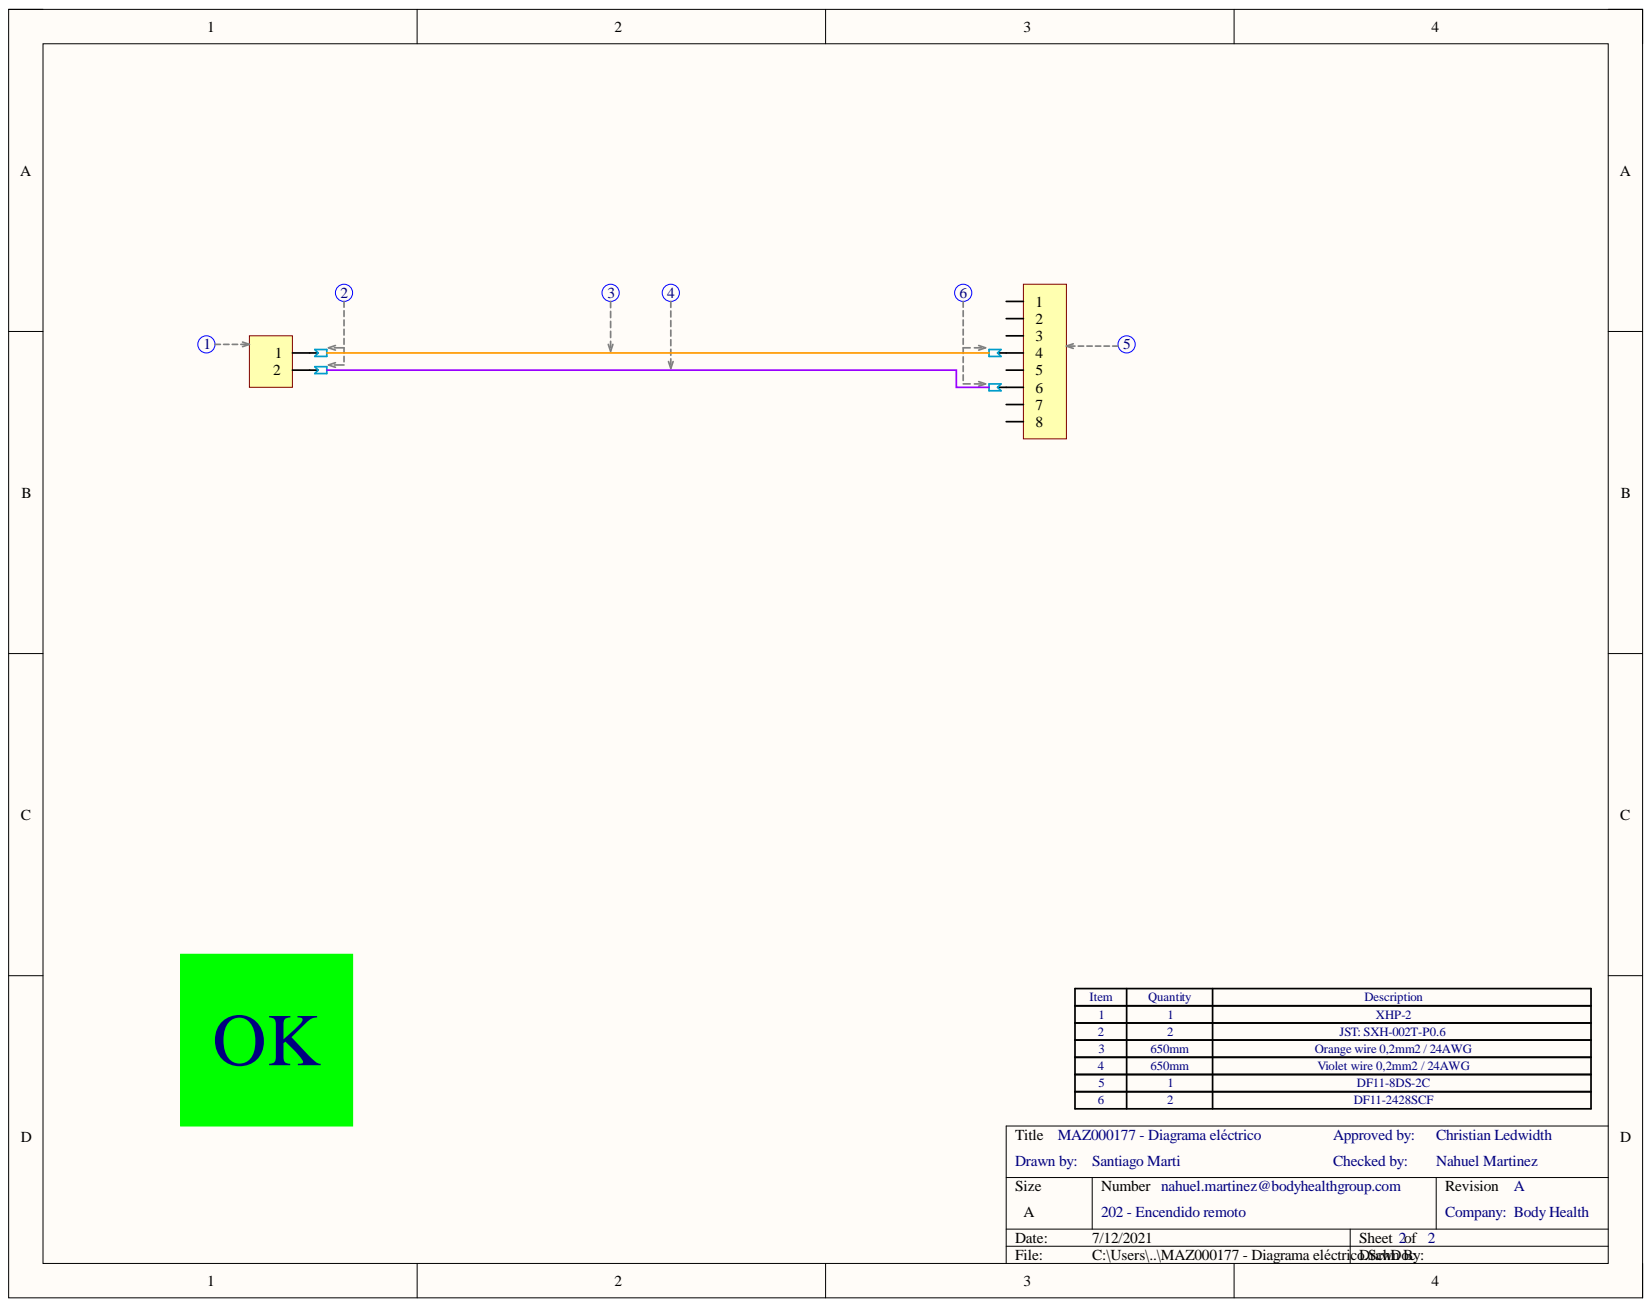
[picture p51: page 1]

Item | Quantity | Description
1 | 1 | XHP-2
2 | 2 | JST: SXH-002T-P0.6
3 | 650mm | Orange wire 0,2mm2 / 24AWG
4 | 650mm | Violet wire 0,2mm2 / 24AWG
5 | 1 | DF11-8DS-2C
6 | 2 | DF11-2428SCF

Size A | Number nahuel.martinez@bodyhealthgroup.com 202 - Encendido remoto | Revision A Company: Body Health

Date: 7/12/2021 | Sheet of 2 2
File: C:\Users\..\MAZ000177 - Diagrama eléctricoDr.ScawhDon Bcy:
