jnahuel-developer/Probador-de-cables/Cables/02. Terminados - PDF/MAZ000178 - Diagrama eléctrico.pdf

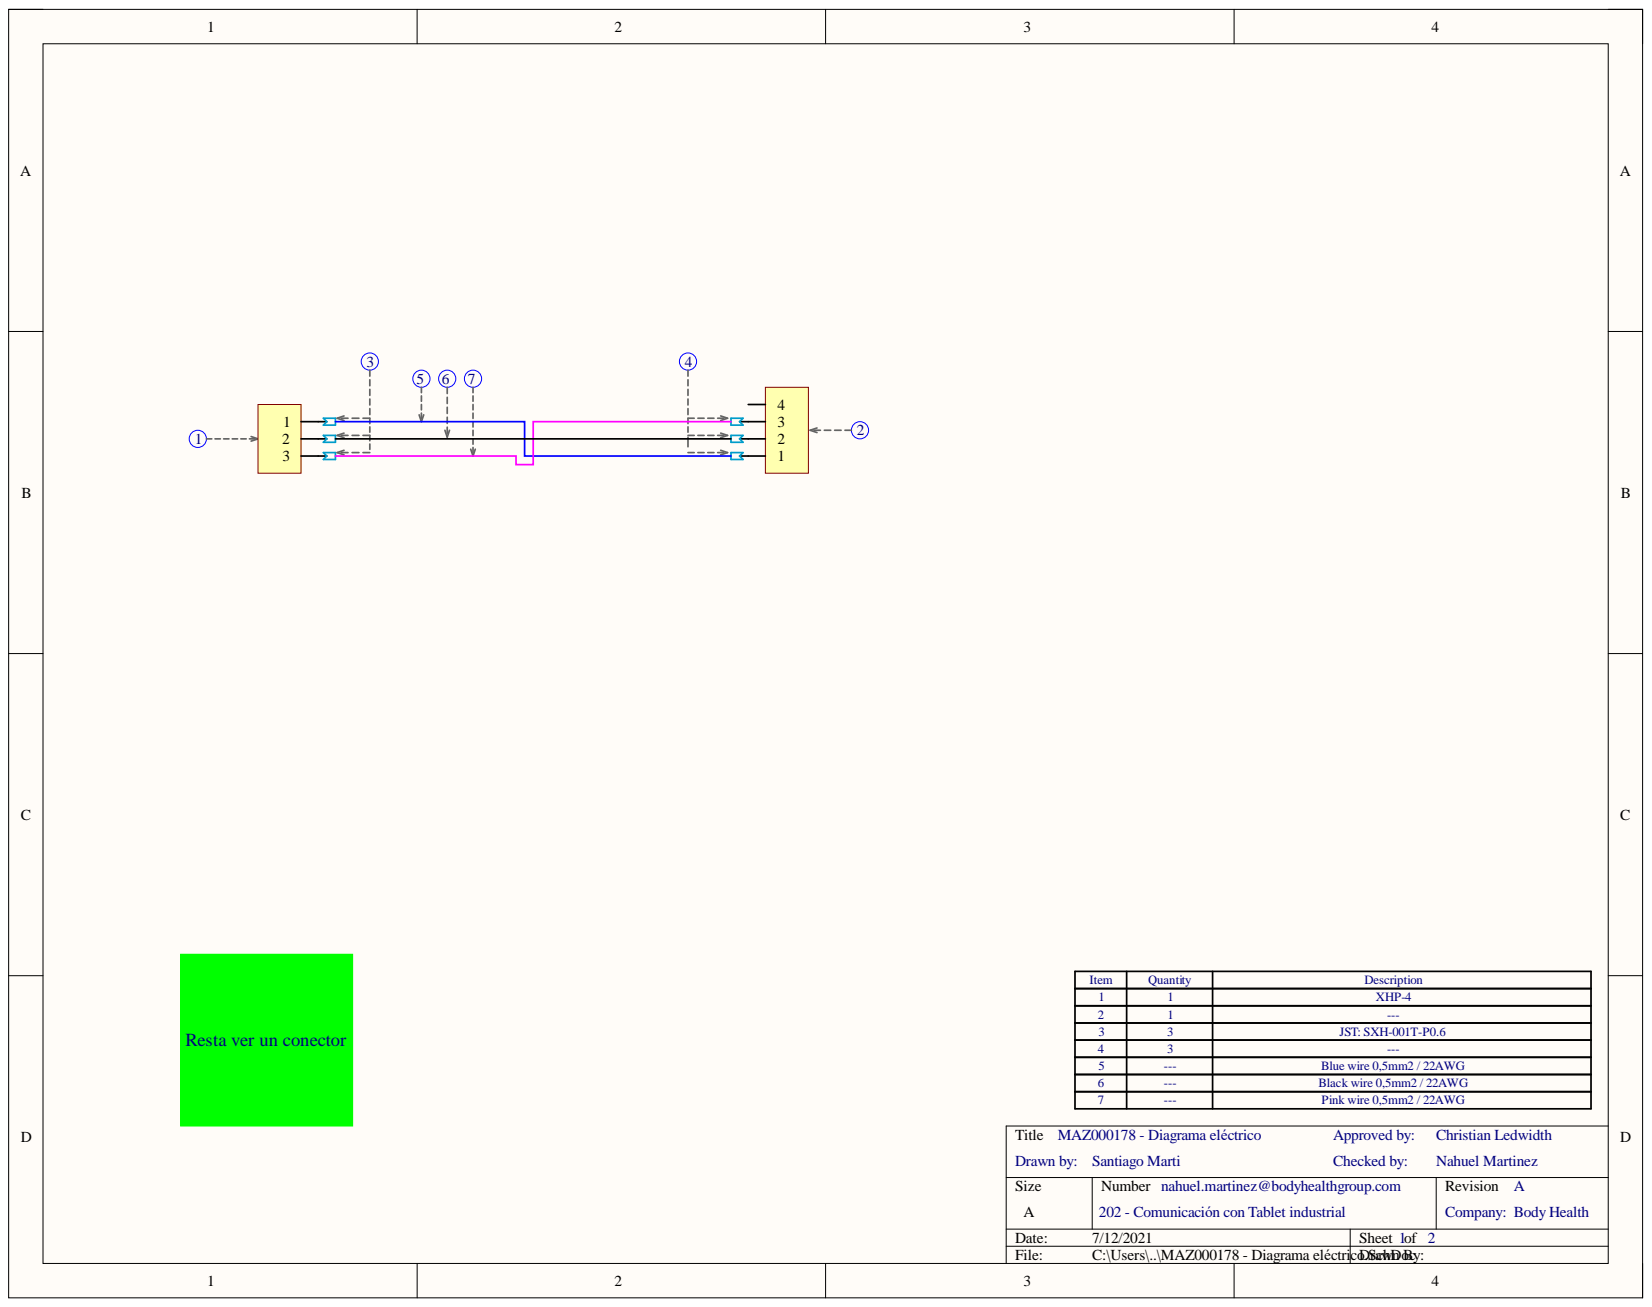
[picture p52: page 1]

Item | Quantity | Description
1 | 1 | XHP-4
2 | 1 | ---
3 | 3 | JST: SXH-001T-P0.6
4 | 3 | ---
5 | --- | Blue wire 0,5mm2 / 22AWG
6 | --- | Black wire 0,5mm2 / 22AWG
7 | --- | Pink wire 0,5mm2 / 22AWG

Resta ver un conector

Size A | Number nahuel.martinez@bodyhealthgroup.com 202 - Comunicación con Tablet industrial | Revision A Company: Body Health

Date: 7/12/2021 | Sheet of 1 2
File: C:\Users\..\MAZ000178 - Diagrama eléctricoDr.ScawhDon Bcy:
