jnahuel-developer/Probador-de-cables/Cables/02. Terminados - PDF/MAZ000178 - Diagrama físico.pdf

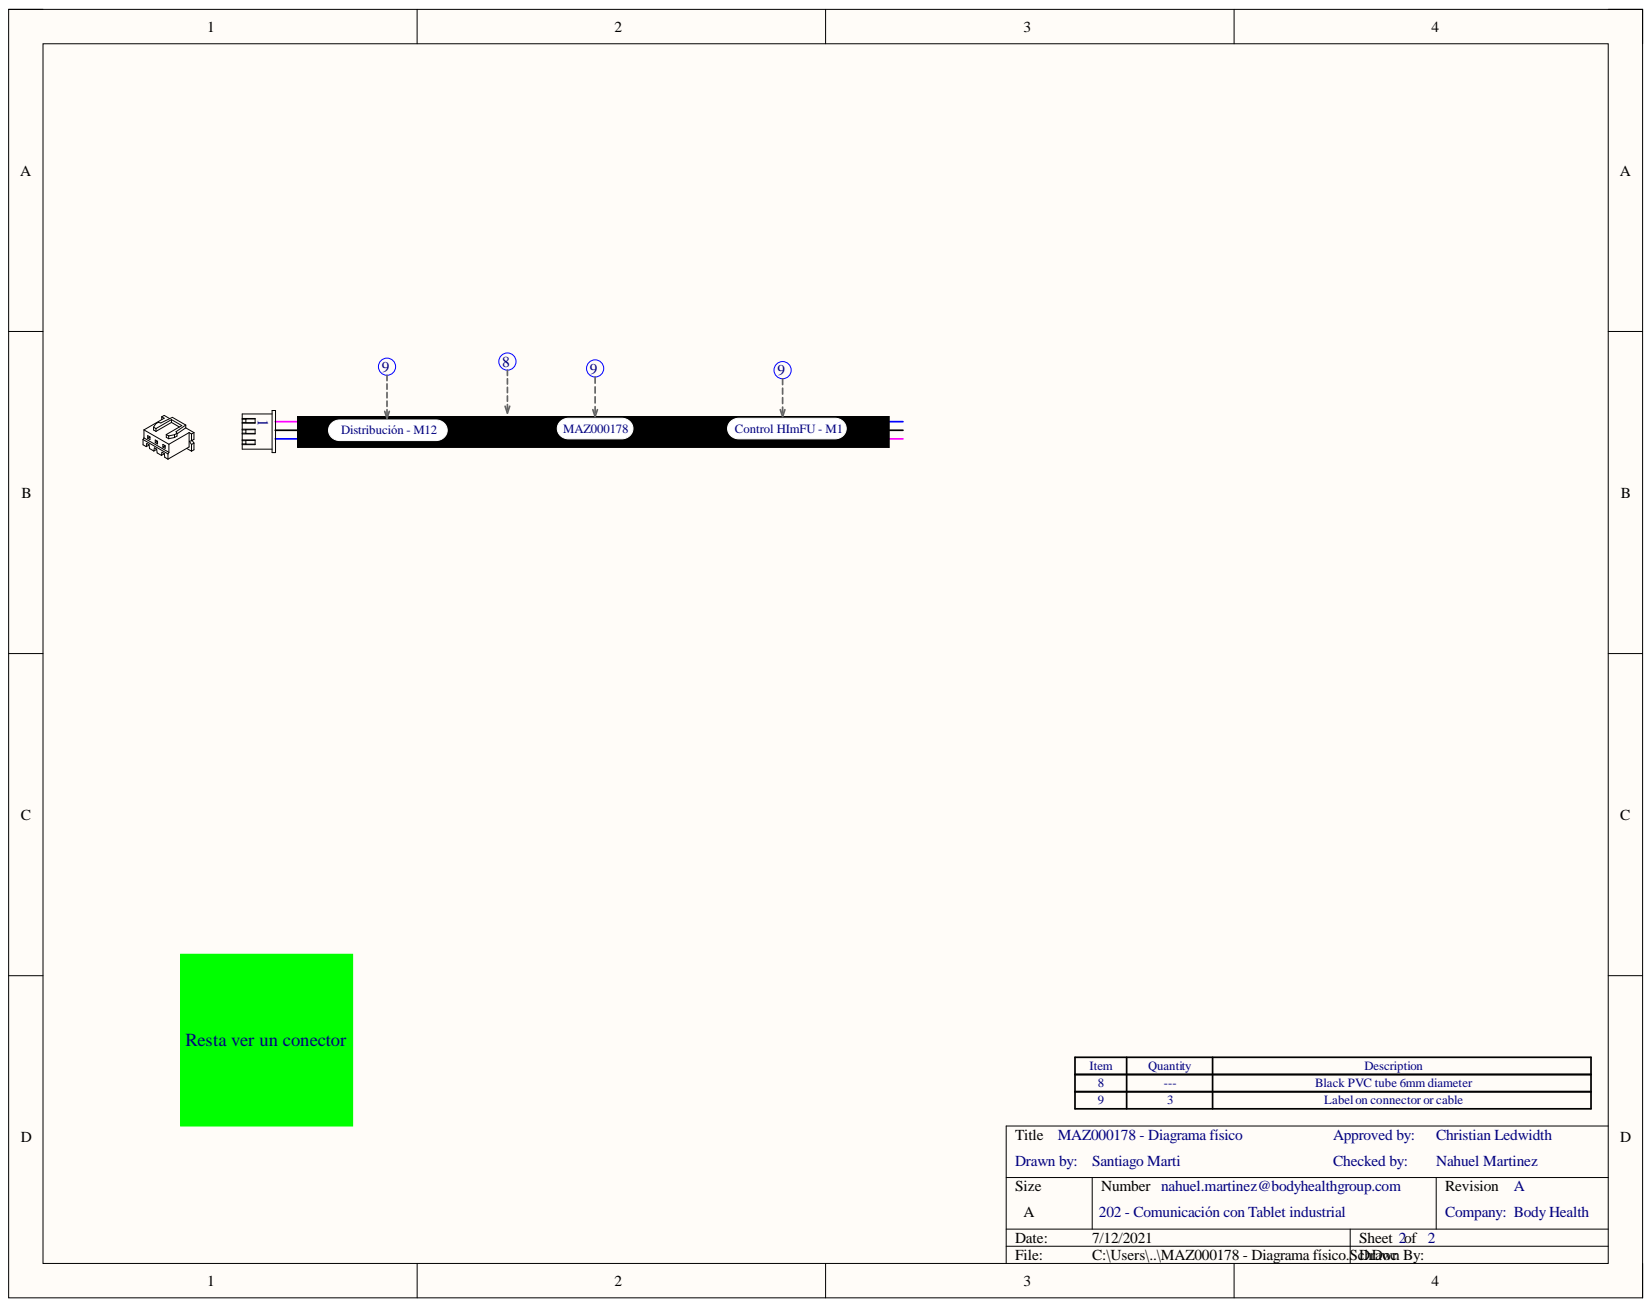
[picture p53: page 1]

Resta ver un conector

Item | Quantity | Description
8 | --- | Black PVC tube 6mm diameter
9 | 3 | Label on connector or cable

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

Date: 7/12/2021 | Sheet of 2 2
File: C:\Users\..\MAZ000178 - Diagrama físico.ScDrhDoawcn By:
