jnahuel-developer/Probador-de-cables/Cables/02. Terminados - PDF/MAZ000179 - Diagrama eléctrico.pdf

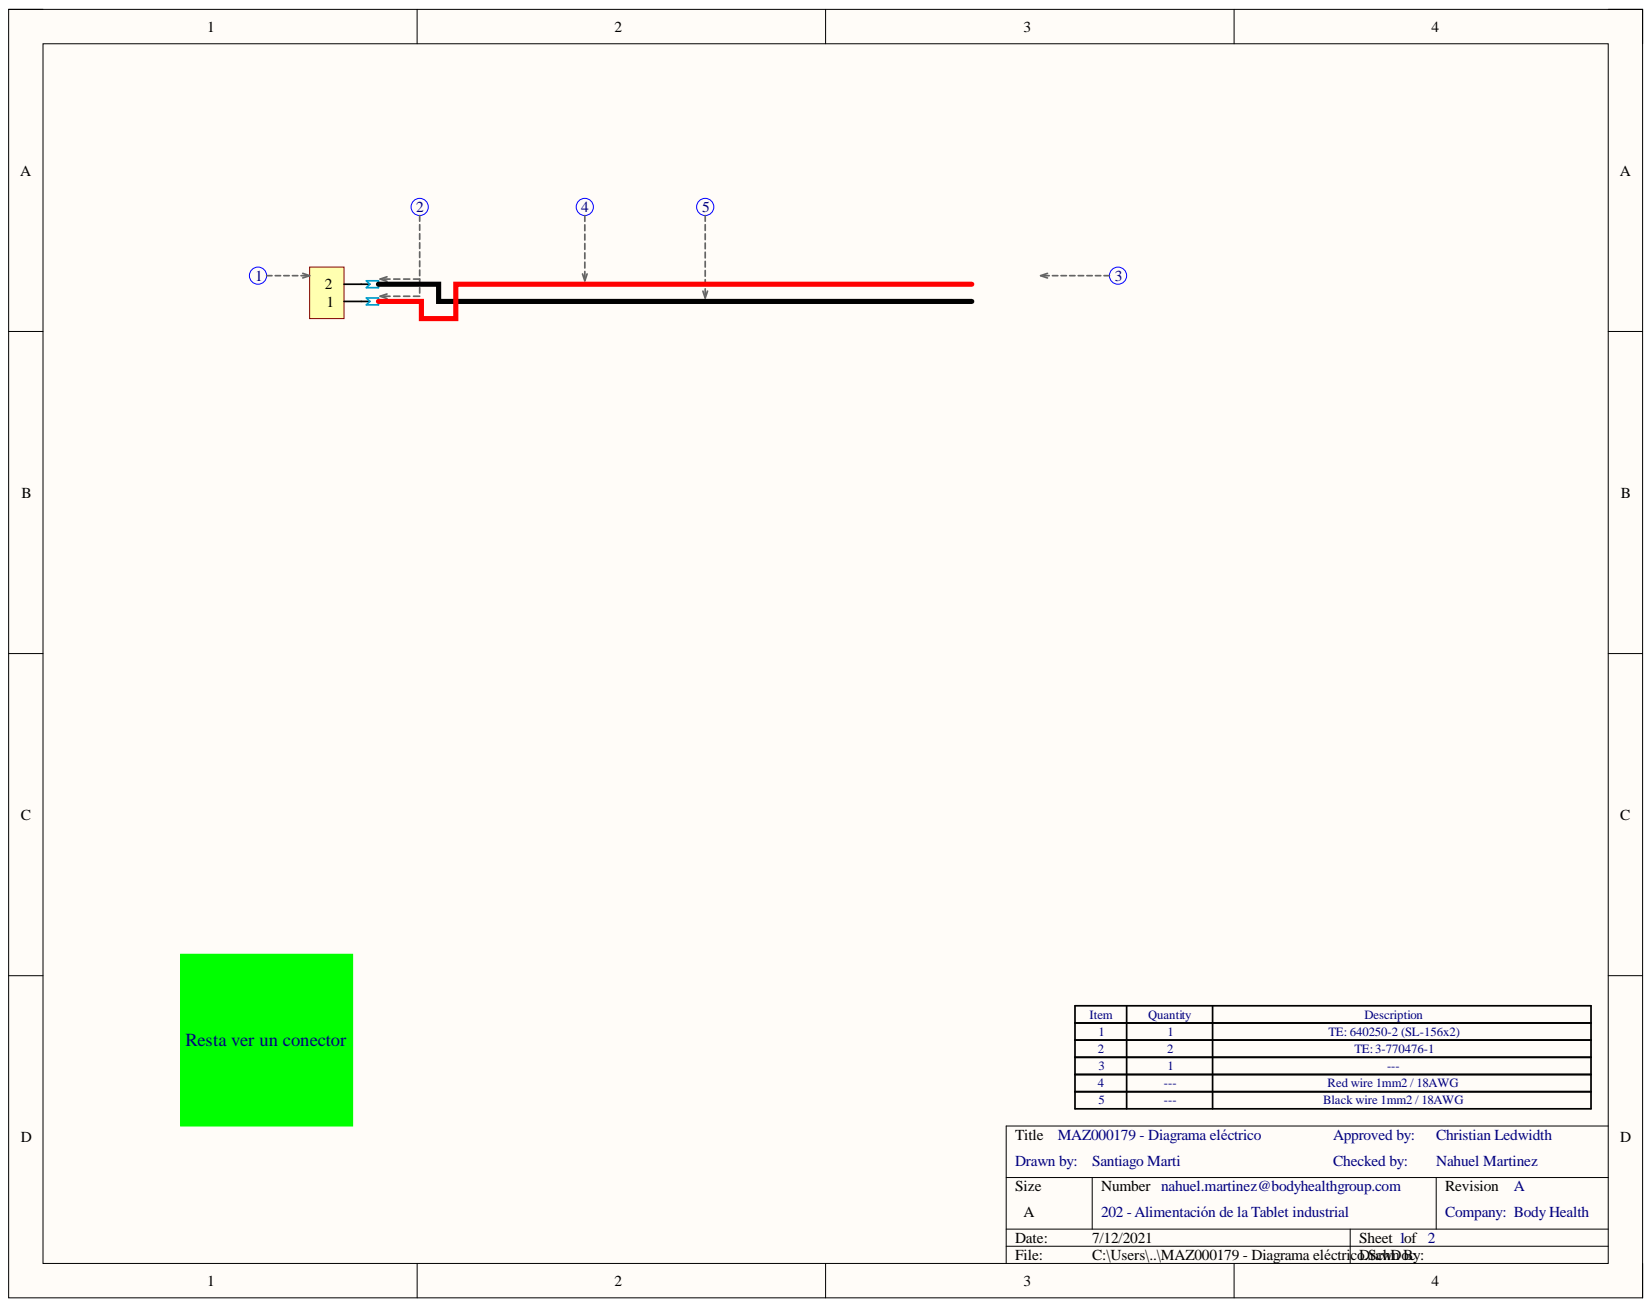
[picture p54: page 1]

Item | Quantity | Description
1 | 1 | TE: 640250-2 (SL-156x2)
2 | 2 | TE: 3-770476-1
3 | 1 | ---
4 | --- | Red wire 1mm2 / 18AWG
5 | --- | Black wire 1mm2 / 18AWG

Resta ver un conector

Size A | Number nahuel.martinez@bodyhealthgroup.com 202 - Alimentación de la Tablet industrial | Revision A Company: Body Health

Date: 7/12/2021 | Sheet of 1 2
File: C:\Users\..\MAZ000179 - Diagrama eléctricoDr.ScawhDon Bcy:
