jnahuel-developer/Probador-de-cables/Cables/02. Terminados - PDF/MAZ000180 - Diagrama eléctrico.pdf

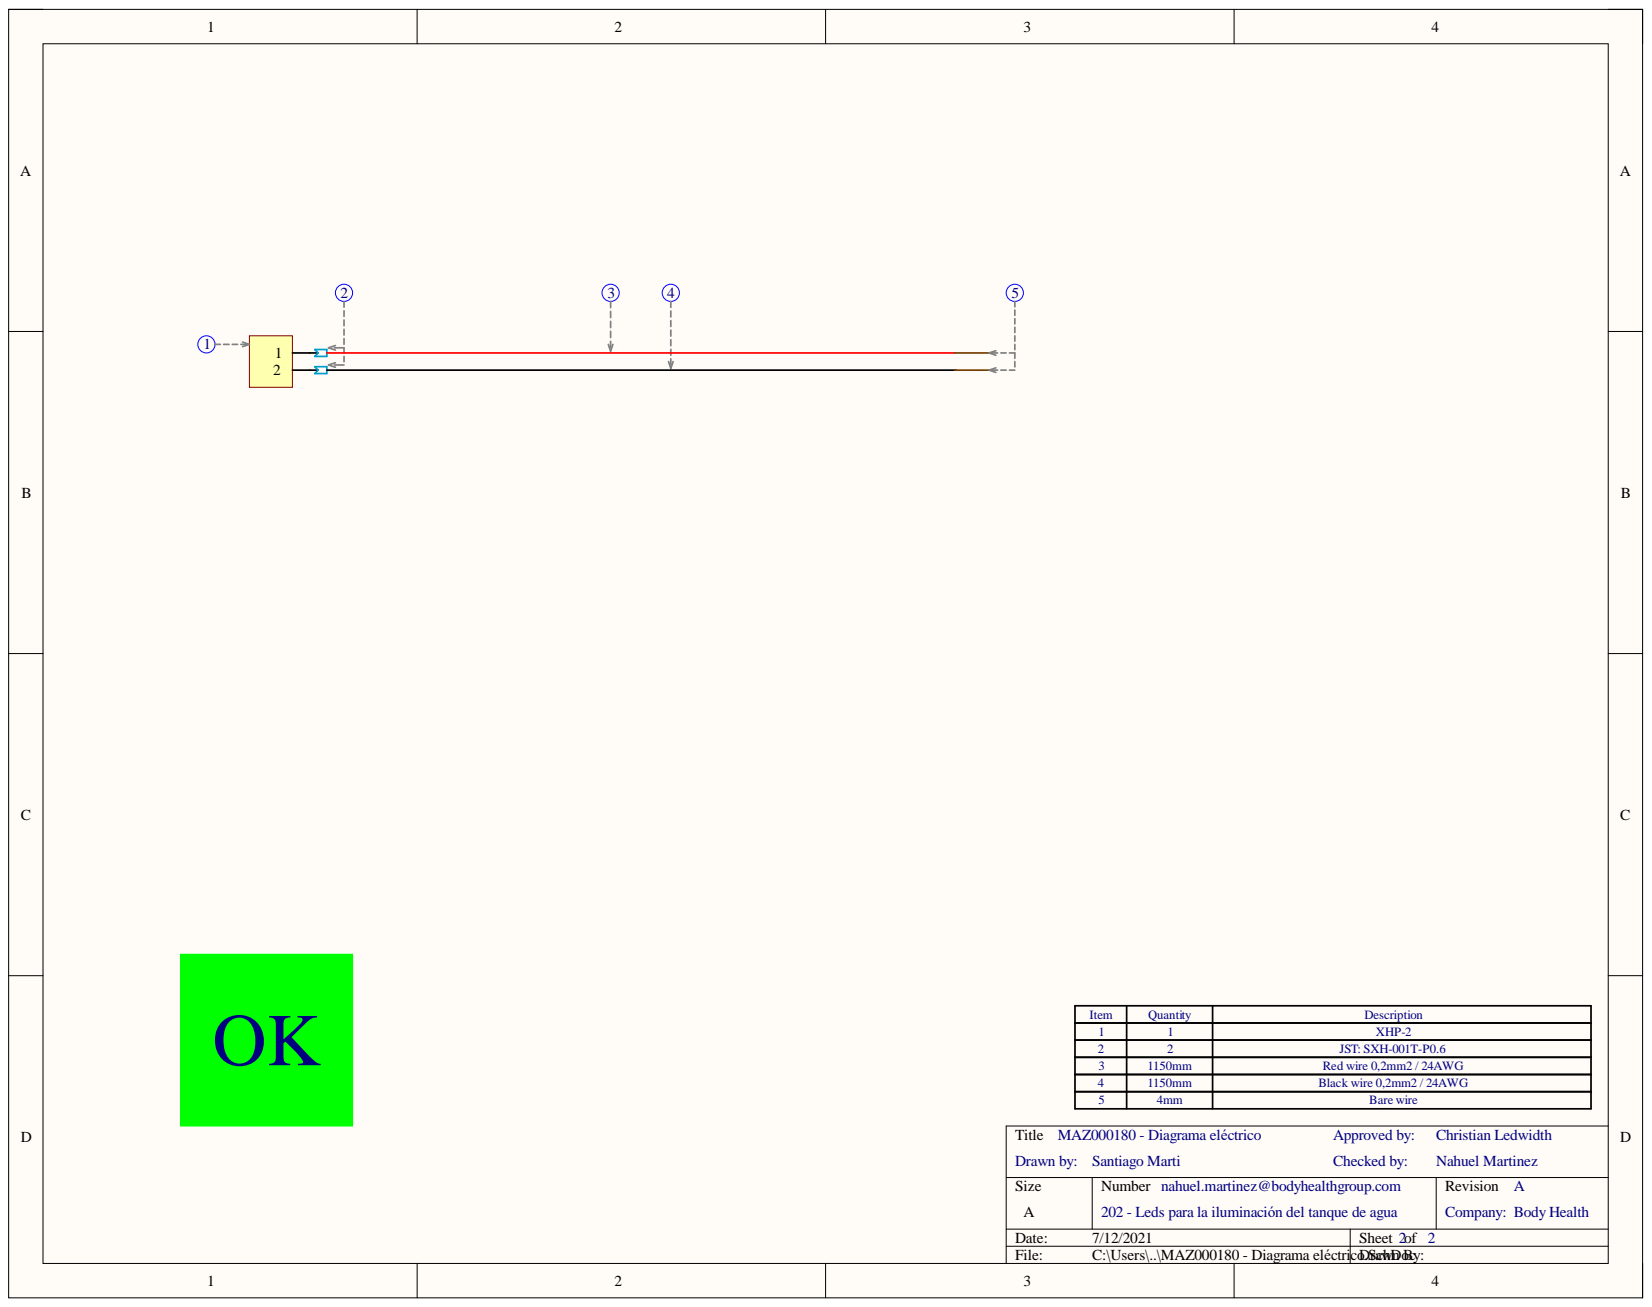
[picture p56: page 1]

Item | Quantity | Description
1 | 1 | XHP-2

3 | 1150mm | Red wire 0,2mm2 / 24AWG
4 | 1150mm | Black wire 0,2mm2 / 24AWG

Size A | Number nahuel.martinez@bodyhealthgroup.com 202 - Leds para la iluminación del tanque de agua | Revision A Company: Body Health

Date: 7/12/2021 | Sheet of 2 2
File: C:\Users\..\MAZ000180 - Diagrama eléctricoDr.ScawhDon Bcy:
