jnahuel-developer/Probador-de-cables/Cables/02. Terminados - PDF/MAZ000181 - Diagrama eléctrico.pdf

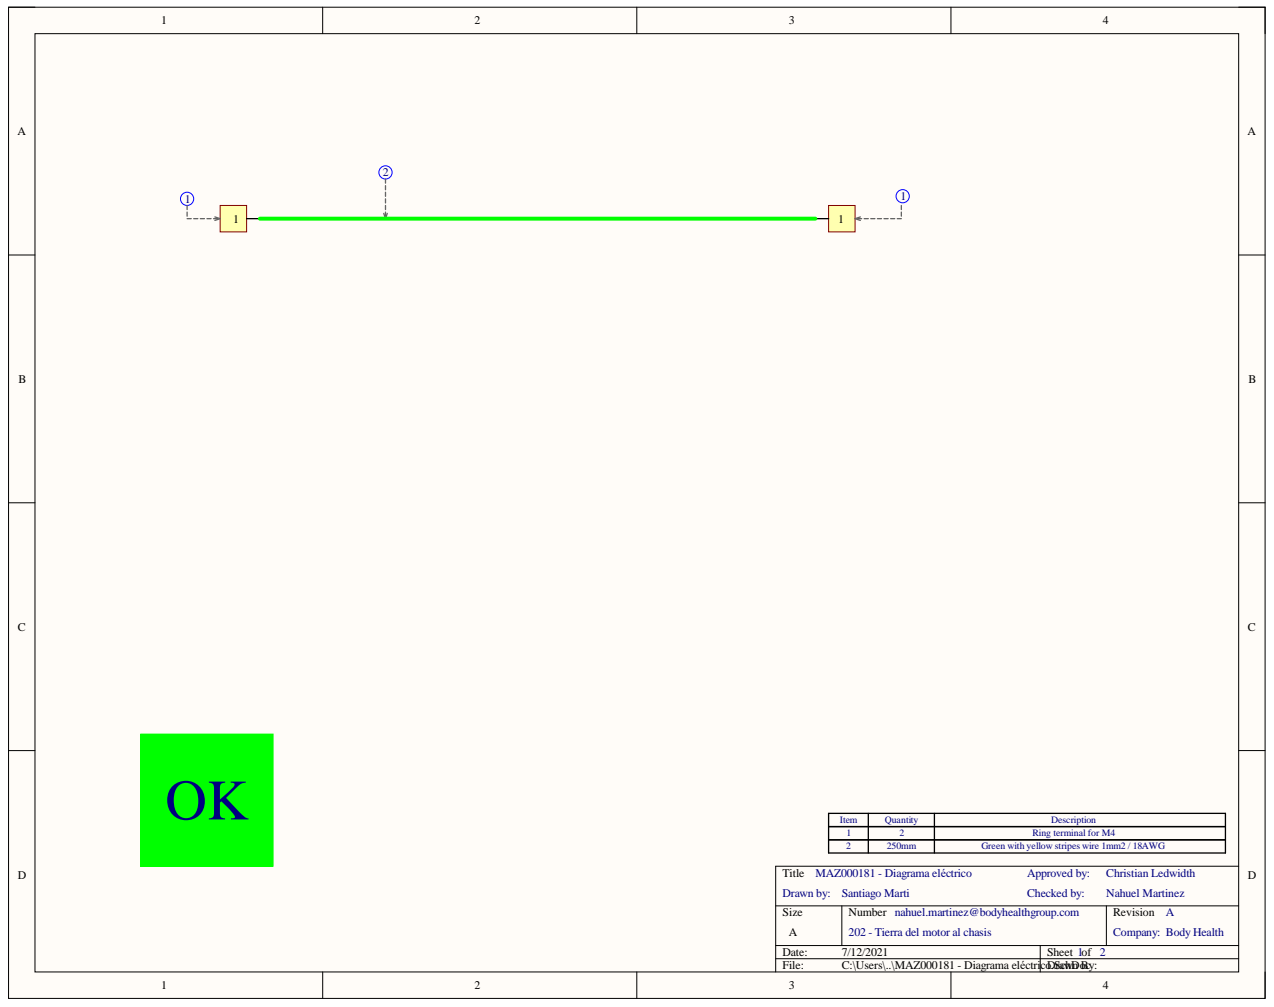
[picture p57: page 1]

Item | Quantity | Description
1 | 2 | Ring terminal for M4
2 | 250mm | Green with yellow stripes wire 1mm2 / 18AWG

Size A | Number nahuel.martinez@bodyhealthgroup.com 202 - Tierra del motor al chasis | Revision A Company: Body Health

Date: 7/12/2021 | Sheet of 1 2
File: C:\Users\..\MAZ000181 - Diagrama eléctricoDr.ScawhDon Bcy:
