jnahuel-developer/Probador-de-cables/Cables/02. Terminados - PDF/MAZ000182 - Diagrama eléctrico.pdf

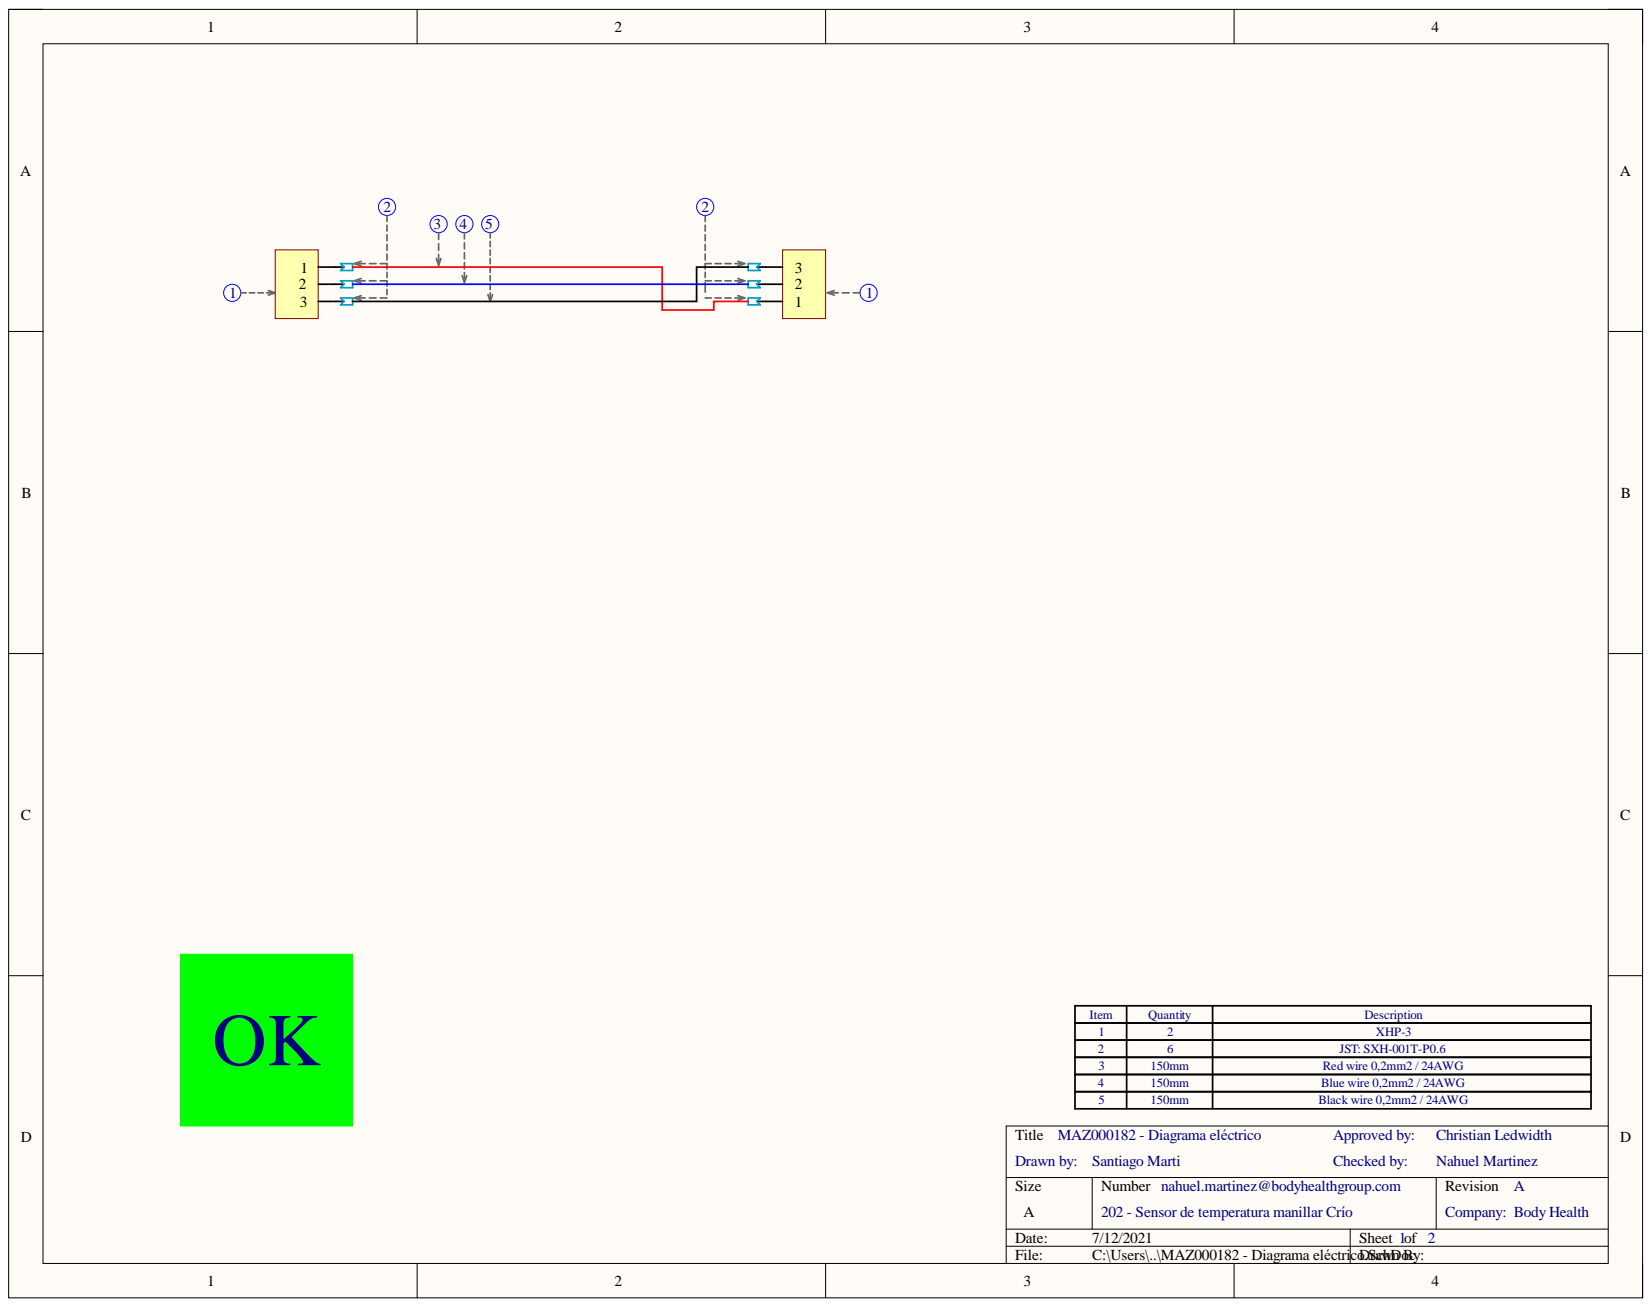
[picture p58: page 1]

Item | Quantity | Description
1 | 2 | XHP-3
2 | 6 | JST: SXH-001T-P0.6
3 | 150mm | Red wire 0,2mm2 / 24AWG
4 | 150mm | Blue wire 0,2mm2 / 24AWG
5 | 150mm | Black wire 0,2mm2 / 24AWG

Size A | Number nahuel.martinez@bodyhealthgroup.com 202 - Sensor de temperatura manillar Crío | Revision A Company: Body Health

Date: 7/12/2021 | Sheet of 1 2
File: C:\Users\..\MAZ000182 - Diagrama eléctricoDr.ScawhDon Bcy:
