jnahuel-developer/Probador-de-cables/Cables/02. Terminados - PDF/MAZ000183 - Diagrama eléctrico.pdf

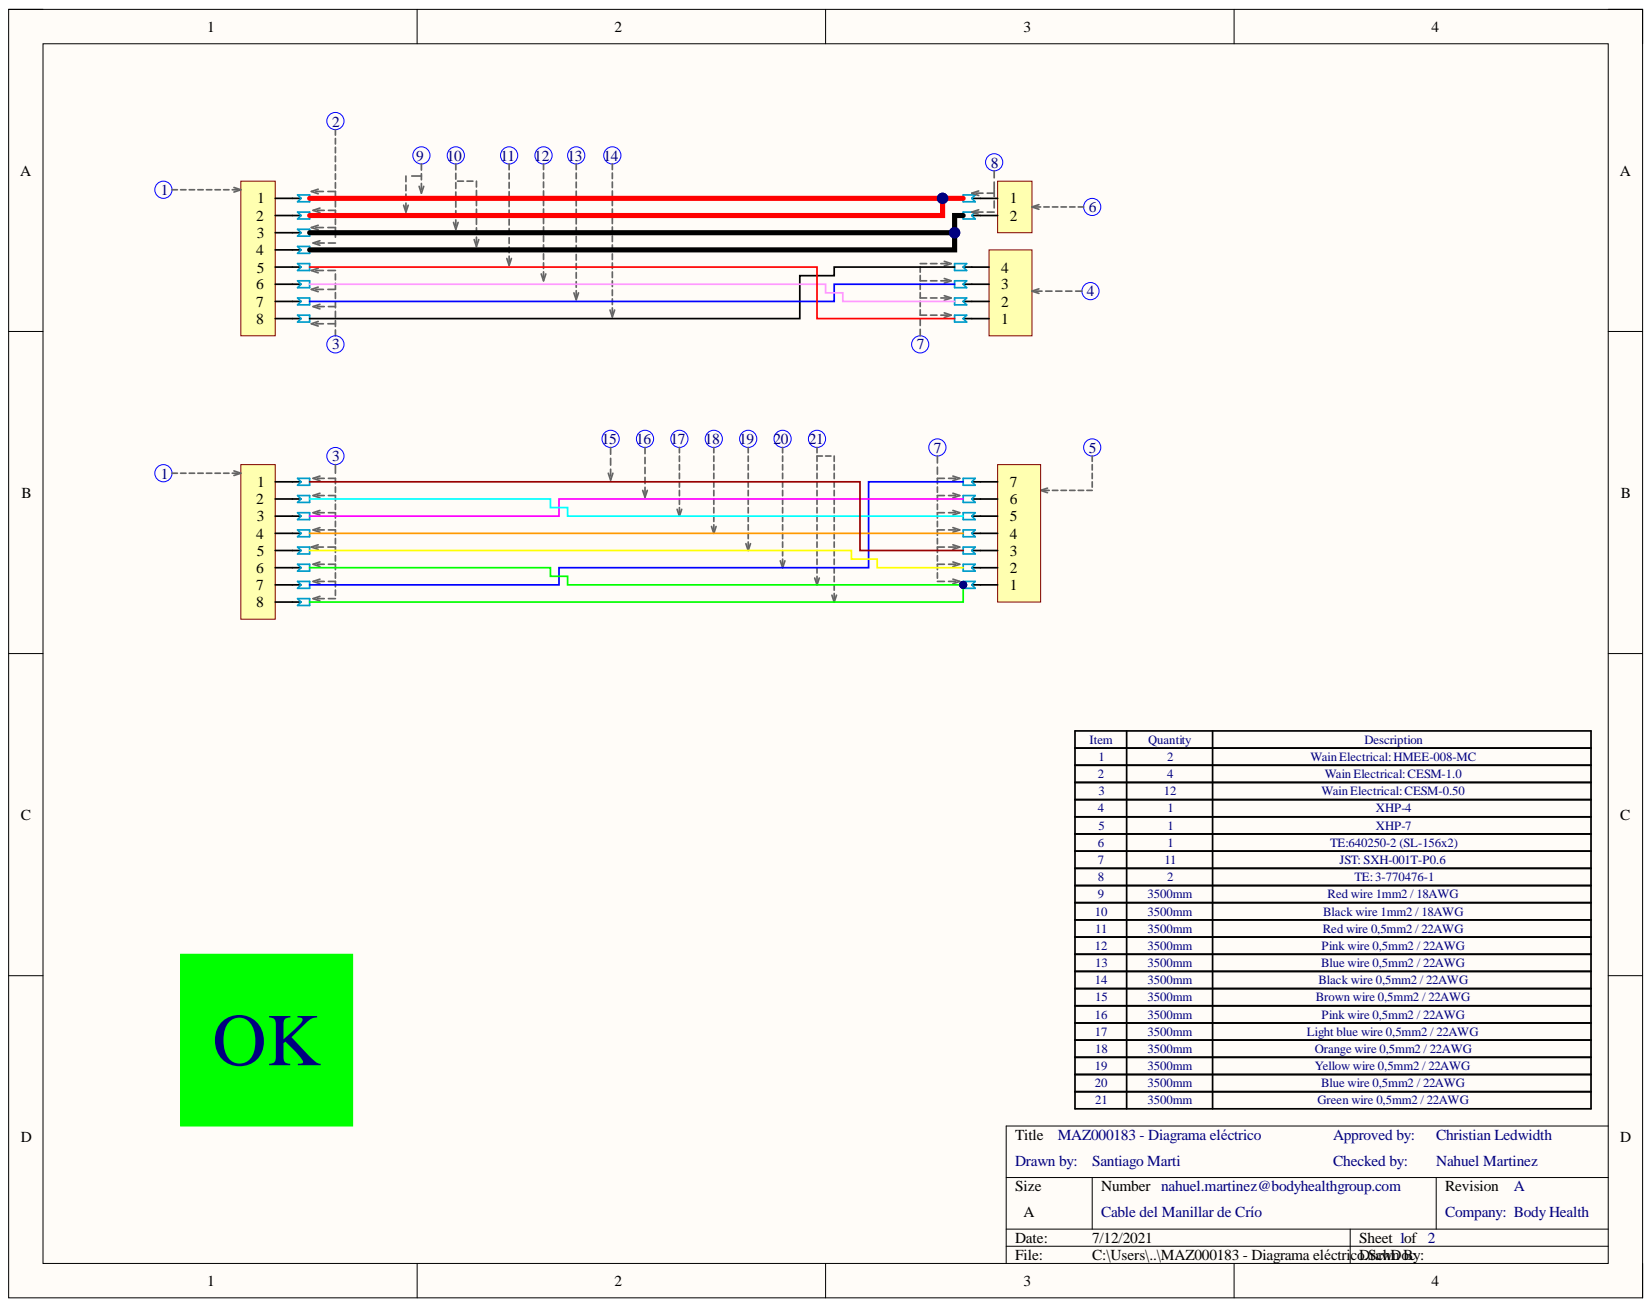
[picture p59: page 1]

Item | Quantity | Description
1 | 2 | Wain Electrical:HMEE-008-MC
2 | 4 | Wain Electrical:CESM-1.0
3 | 12 | Wain Electrical:CESM-0.50
4 | 1 | XHP-4
5 | 1 | XHP-7
6 | 1 | TE:640250-2 (SL-156x2)
7 | 11 | JST: SXH-001T-P0.6
8 | 2 | TE: 3-770476-1
9 | 3500mm | Red wire 1mm2 / 18AWG
10 | 3500mm | Black wire 1mm2 / 18AWG
11 | 3500mm | Red wire 0,5mm2 / 22AWG
12 | 3500mm | Pink wire 0,5mm2 / 22AWG

14 | 3500mm | Black wire 0,5mm2 / 22AWG
15 | 3500mm | Brown wire 0,5mm2 / 22AWG
16 | 3500mm | Pink wire 0,5mm2 / 22AWG
17 | 3500mm | Light blue wire 0,5mm2 / 22AWG
18 | 3500mm | Orange wire 0,5mm2 / 22AWG
19 | 3500mm | Yellow wire 0,5mm2 / 22AWG
20 | 3500mm | Blue wire 0,5mm2 / 22AWG
21 | 3500mm | Green wire 0,5mm2 / 22AWG

Size A | Number nahuel.martinez@bodyhealthgroup.com Cable del Manillar de Crío | Revision A Company: Body Health

Date: 7/12/2021 | Sheet of 1 2
File: C:\Users\..\MAZ000183 - Diagrama eléctricoDr.ScawhDon Bcy:
