jnahuel-developer/Probador-de-cables/Cables/02. Terminados - PDF/MAZ000184 - Diagrama físico.pdf

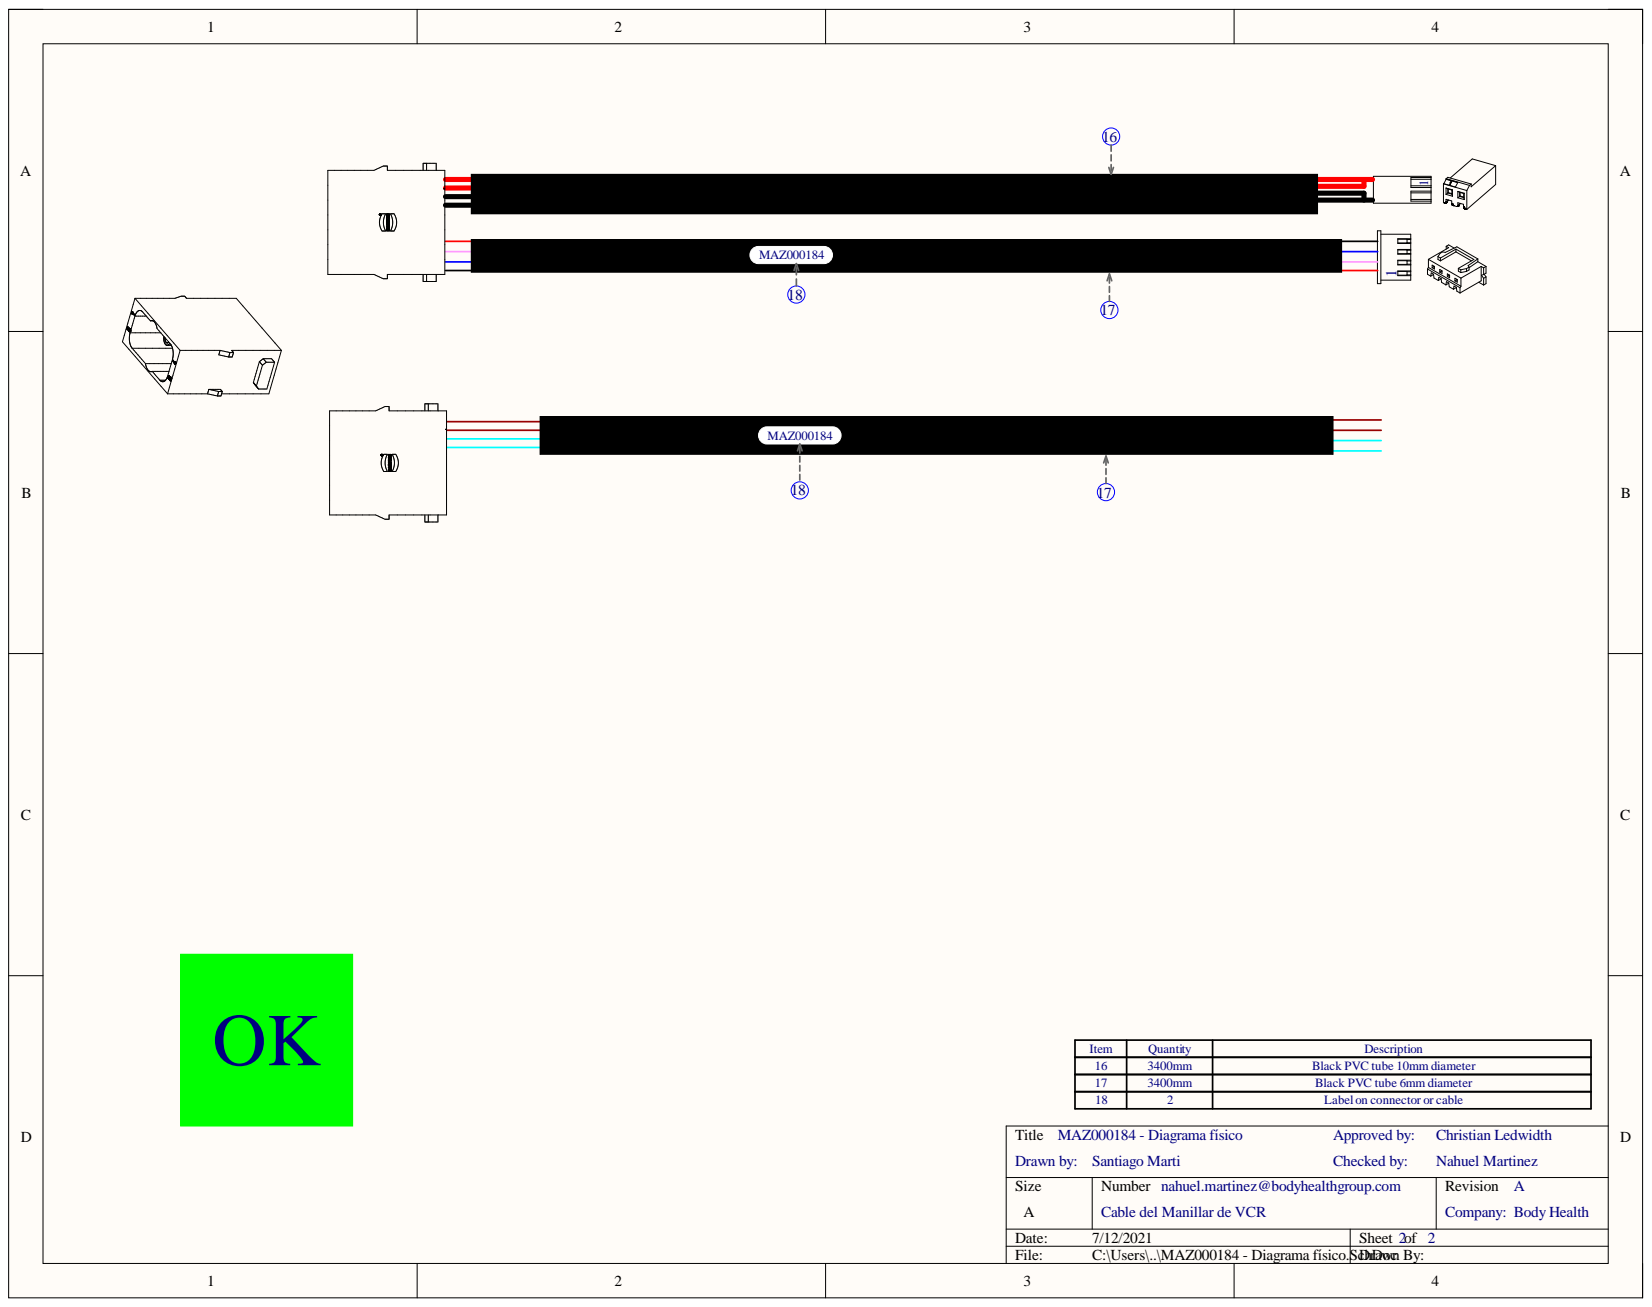
[picture p62: page 1]

Item | Quantity | Description
16 | 3400mm | Black PVC tube 10mm diameter
17 | 3400mm | Black PVC tube 6mm diameter
18 | 2 | Label on connector or cable

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

Date: 7/12/2021 | Sheet of 2 2
File: C:\Users\..\MAZ000184 - Diagrama físico.ScDrhDoawcn By:
