jnahuel-developer/Probador-de-cables/Cables/02. Terminados - PDF/MAZ000185 - Diagrama eléctrico.pdf

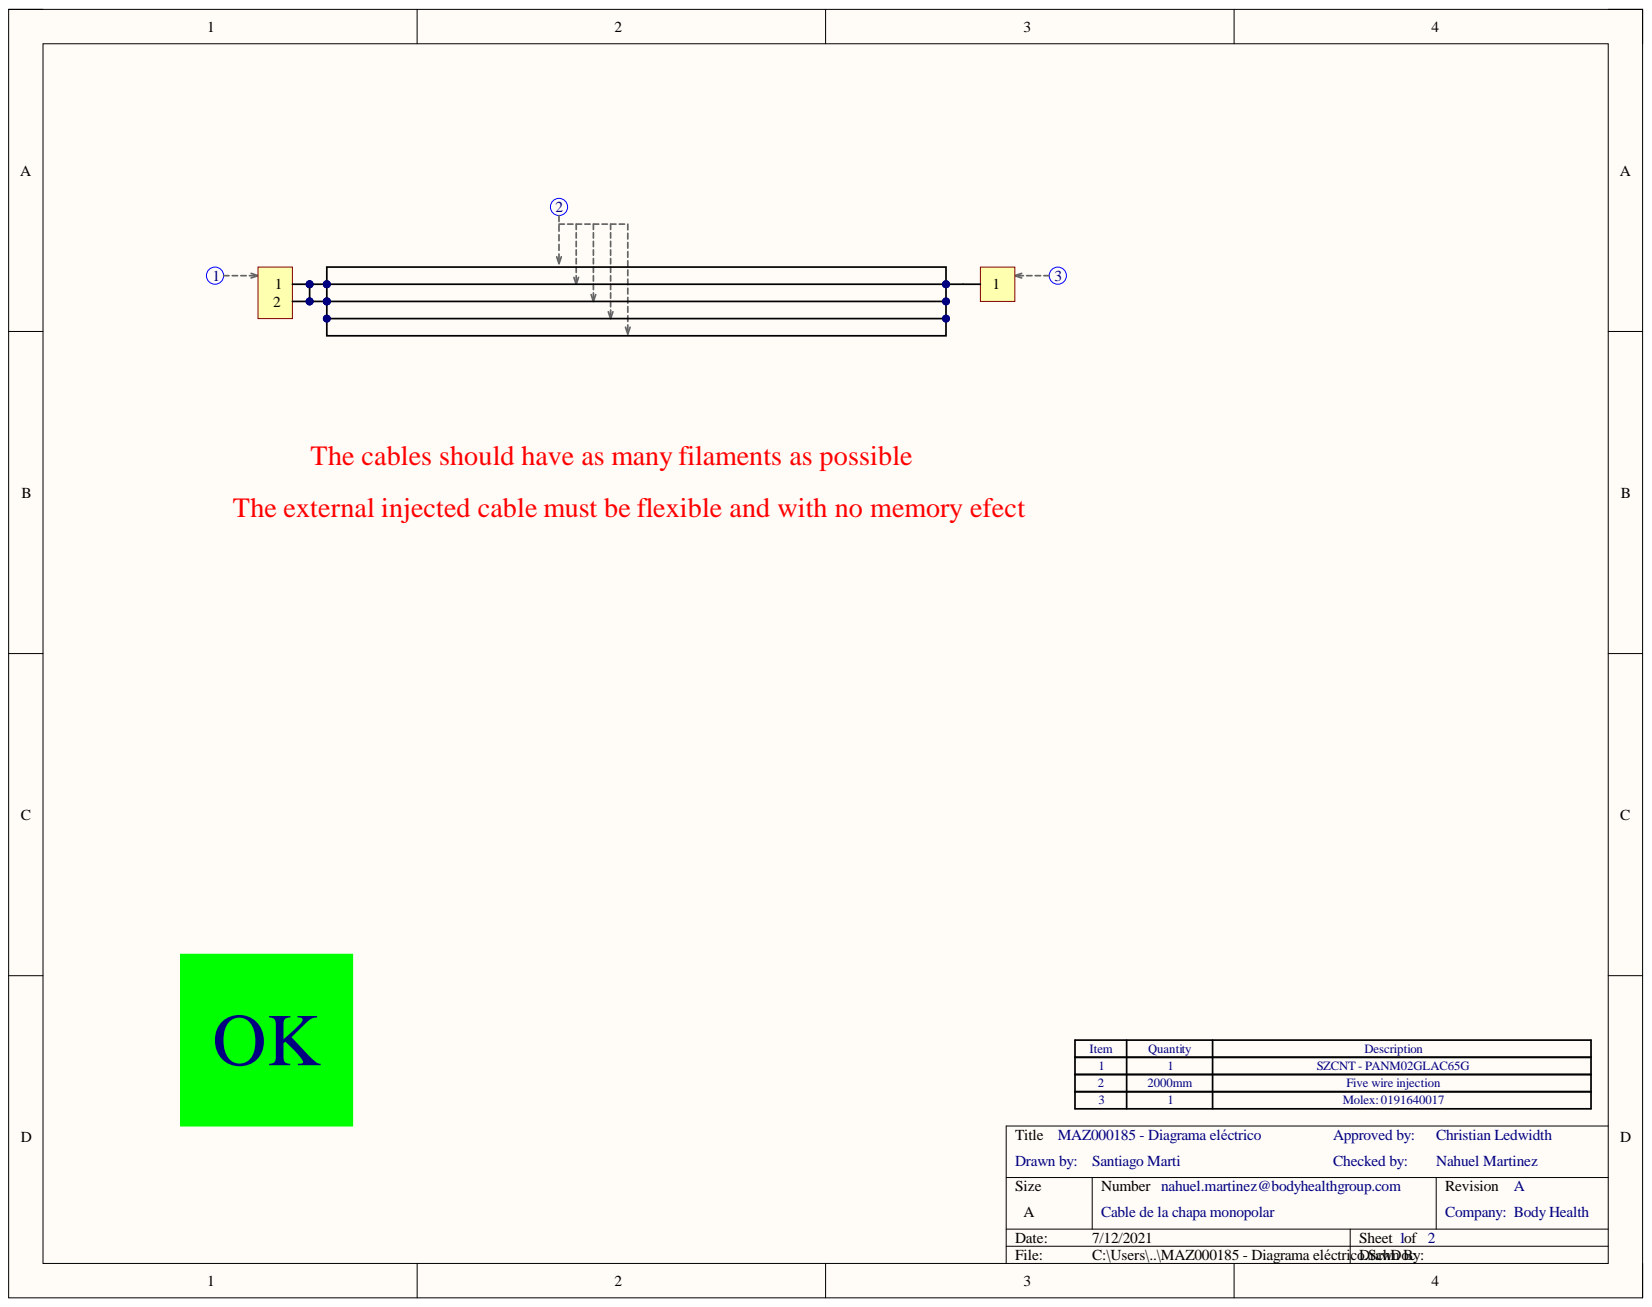
[picture p63: page 1]

The cables should have as many filaments as possible

The external injected cable must be flexible and with no memory efect

Item | Quantity | Description
1 | 1 | SZCNT - PANM02GLAC65G
2 | 2000mm | Five wire injection
3 | 1 | Molex: 0191640017

Size A | Number nahuel.martinez@bodyhealthgroup.com Cable de la chapa monopolar | Revision A Company: Body Health

Date: 7/12/2021 | Sheet of 1 2
File: C:\Users\..\MAZ000185 - Diagrama eléctricoDr.ScawhDon Bcy:
