jnahuel-developer/Probador-de-cables/Cables/02. Terminados - PDF/MAZ000185 - Diagrama físico.pdf

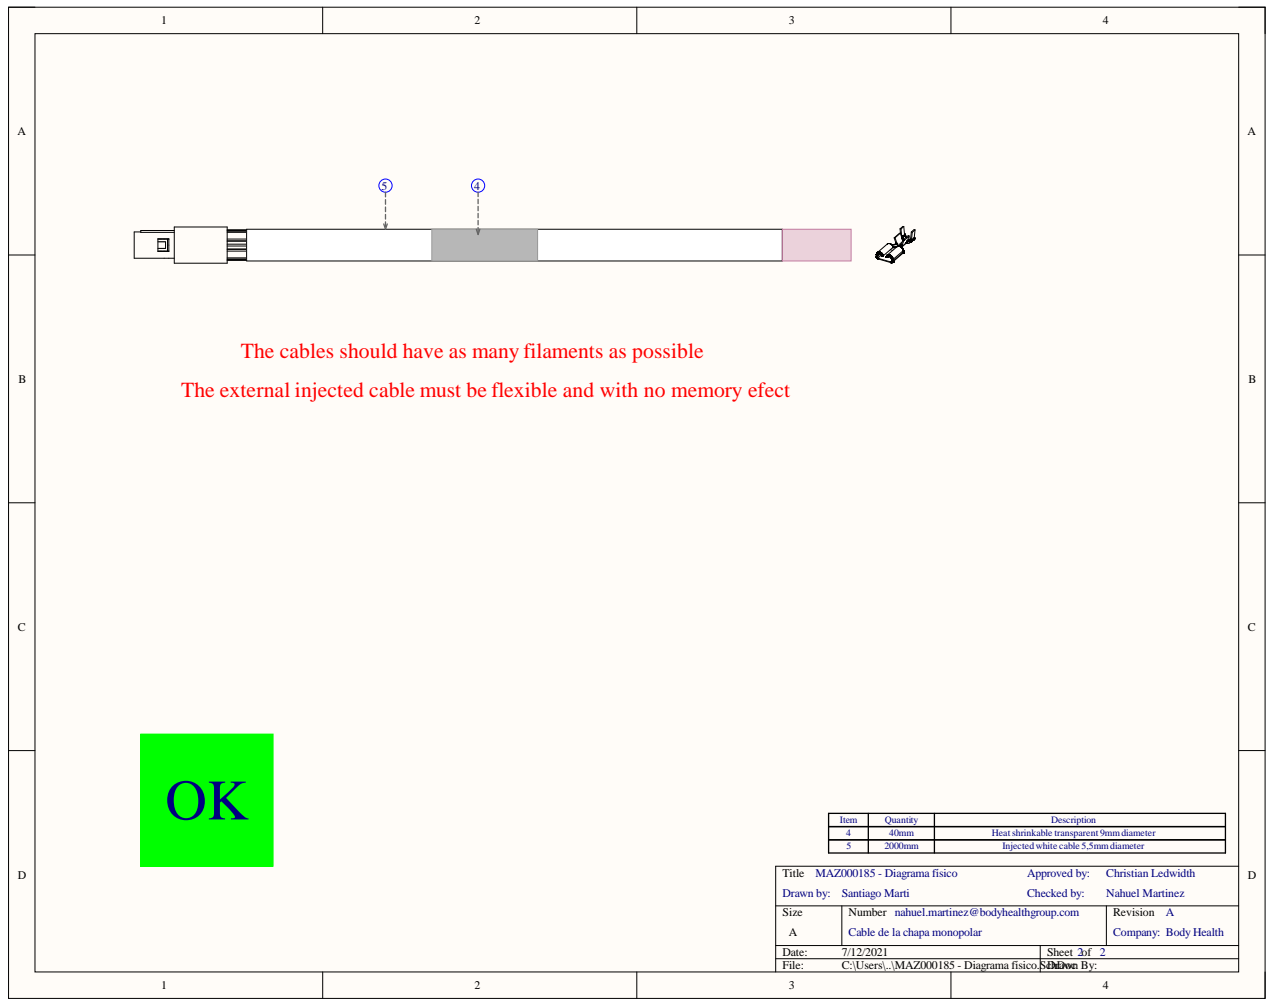
[picture p64: page 1]

The cables should have as many filaments as possible

The external injected cable must be flexible and with no memory efect

Item | Quantity | Description
4 | 40mm | Heatshrinkable transparent 9mmdiameter
5 | 2000mm | Injected white cable 5,5mmdiameter

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

Date: 7/12/2021 | Sheet of 2 2
File: C:\Users\..\MAZ000185 - Diagrama físico.ScDrhDoawcn By:
