jnahuel-developer/Probador-de-cables/Cables/02. Terminados - PDF/MAZ000186 - Diagrama eléctrico.pdf

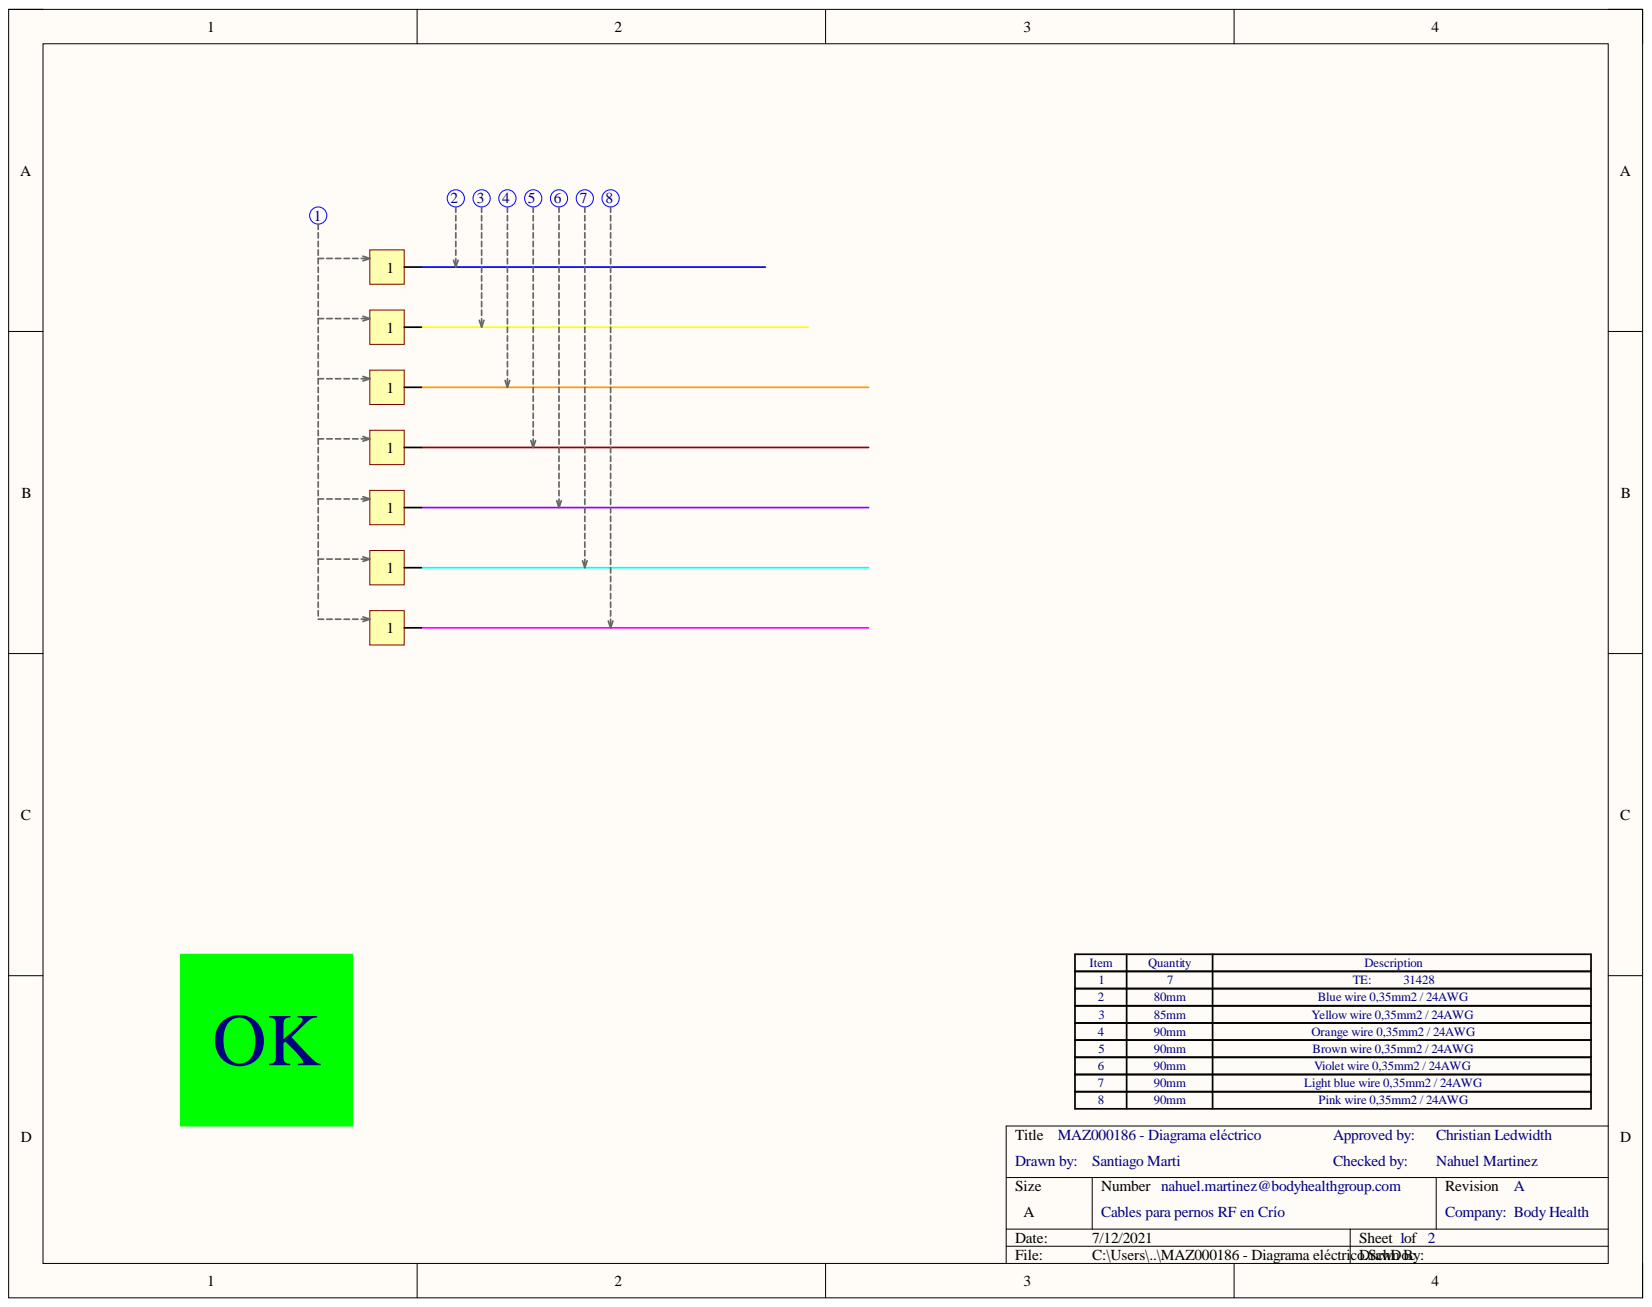
[picture p65: page 1]

1 | 7 | TE: 31428
2 | 80mm | Blue wire 0,35mm2 / 24AWG
3 | 85mm | Yellow wire 0,35mm2 / 24AWG
4 | 90mm | Orange wire 0,35mm2 / 24AWG
5 | 90mm | Brown wire 0,35mm2 / 24AWG
6 | 90mm | Violet wire 0,35mm2 / 24AWG
7 | 90mm | Light blue wire 0,35mm2 / 24AWG
8 | 90mm | Pink wire 0,35mm2 / 24AWG

Size A | Number nahuel.martinez@bodyhealthgroup.com Cables para pernos RF en Crío | Revision A Company: Body Health

Date: 7/12/2021 | Sheet of 1 2
File: C:\Users\..\MAZ000186 - Diagrama eléctricoDr.ScawhDon Bcy:
