jnahuel-developer/Probador-de-cables/Cables/02. Terminados - PDF/MAZ000186 - Diagrama físico.pdf

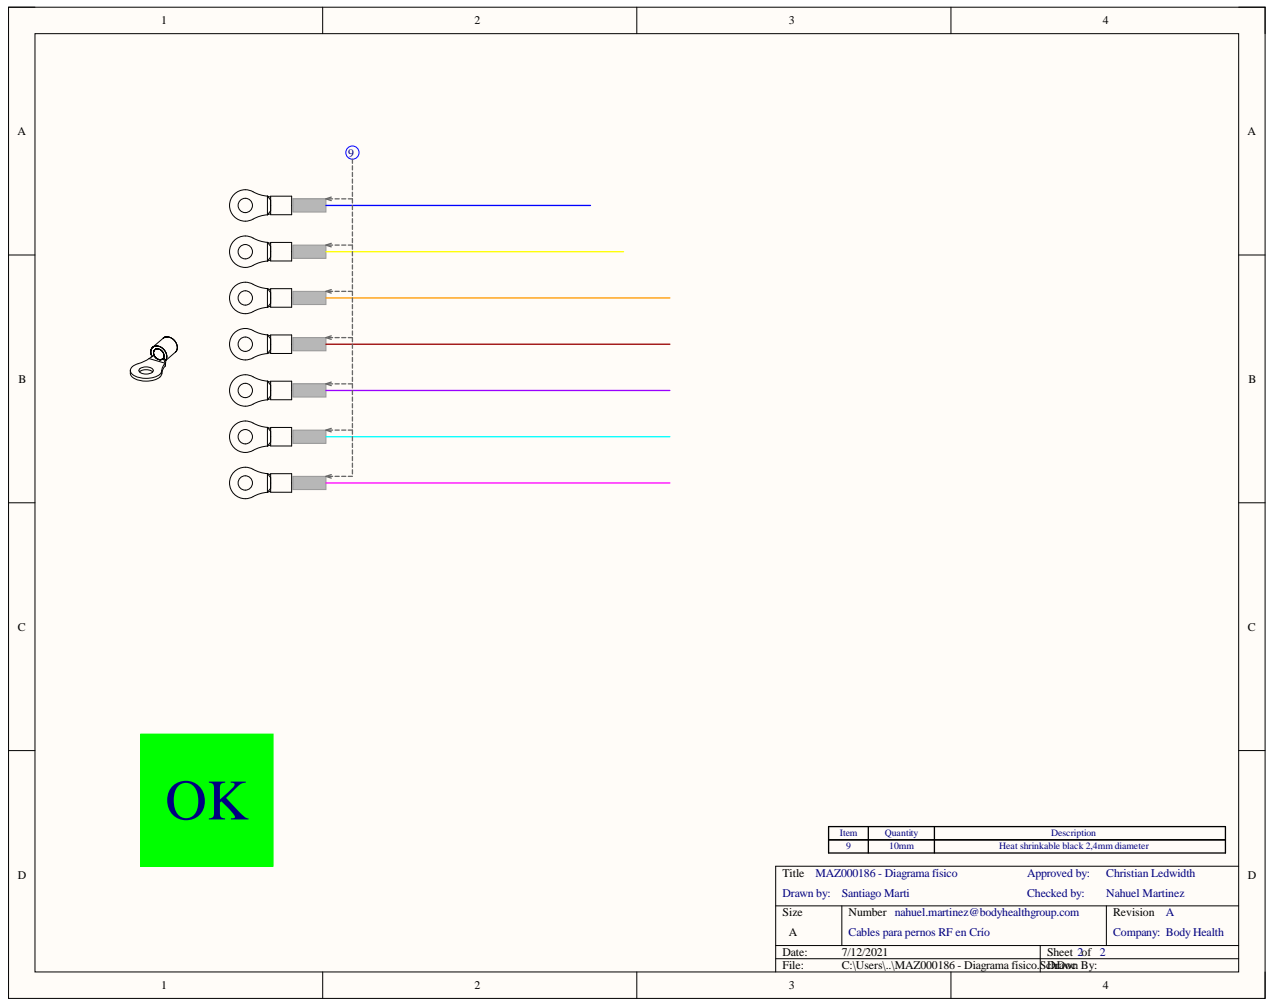
[picture p66: page 1]

Item | Quantity | Description
9 | 10mm | Heat shrinkable black 2,4mm diameter

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

Date: 7/12/2021 | Sheet of 2 2
File: C:\Users\..\MAZ000186 - Diagrama físico.ScDrhDoawcn By:
