jnahuel-developer/Probador-de-cables/Cables/02. Terminados - PDF/MAZ000187 - Diagrama eléctrico.pdf

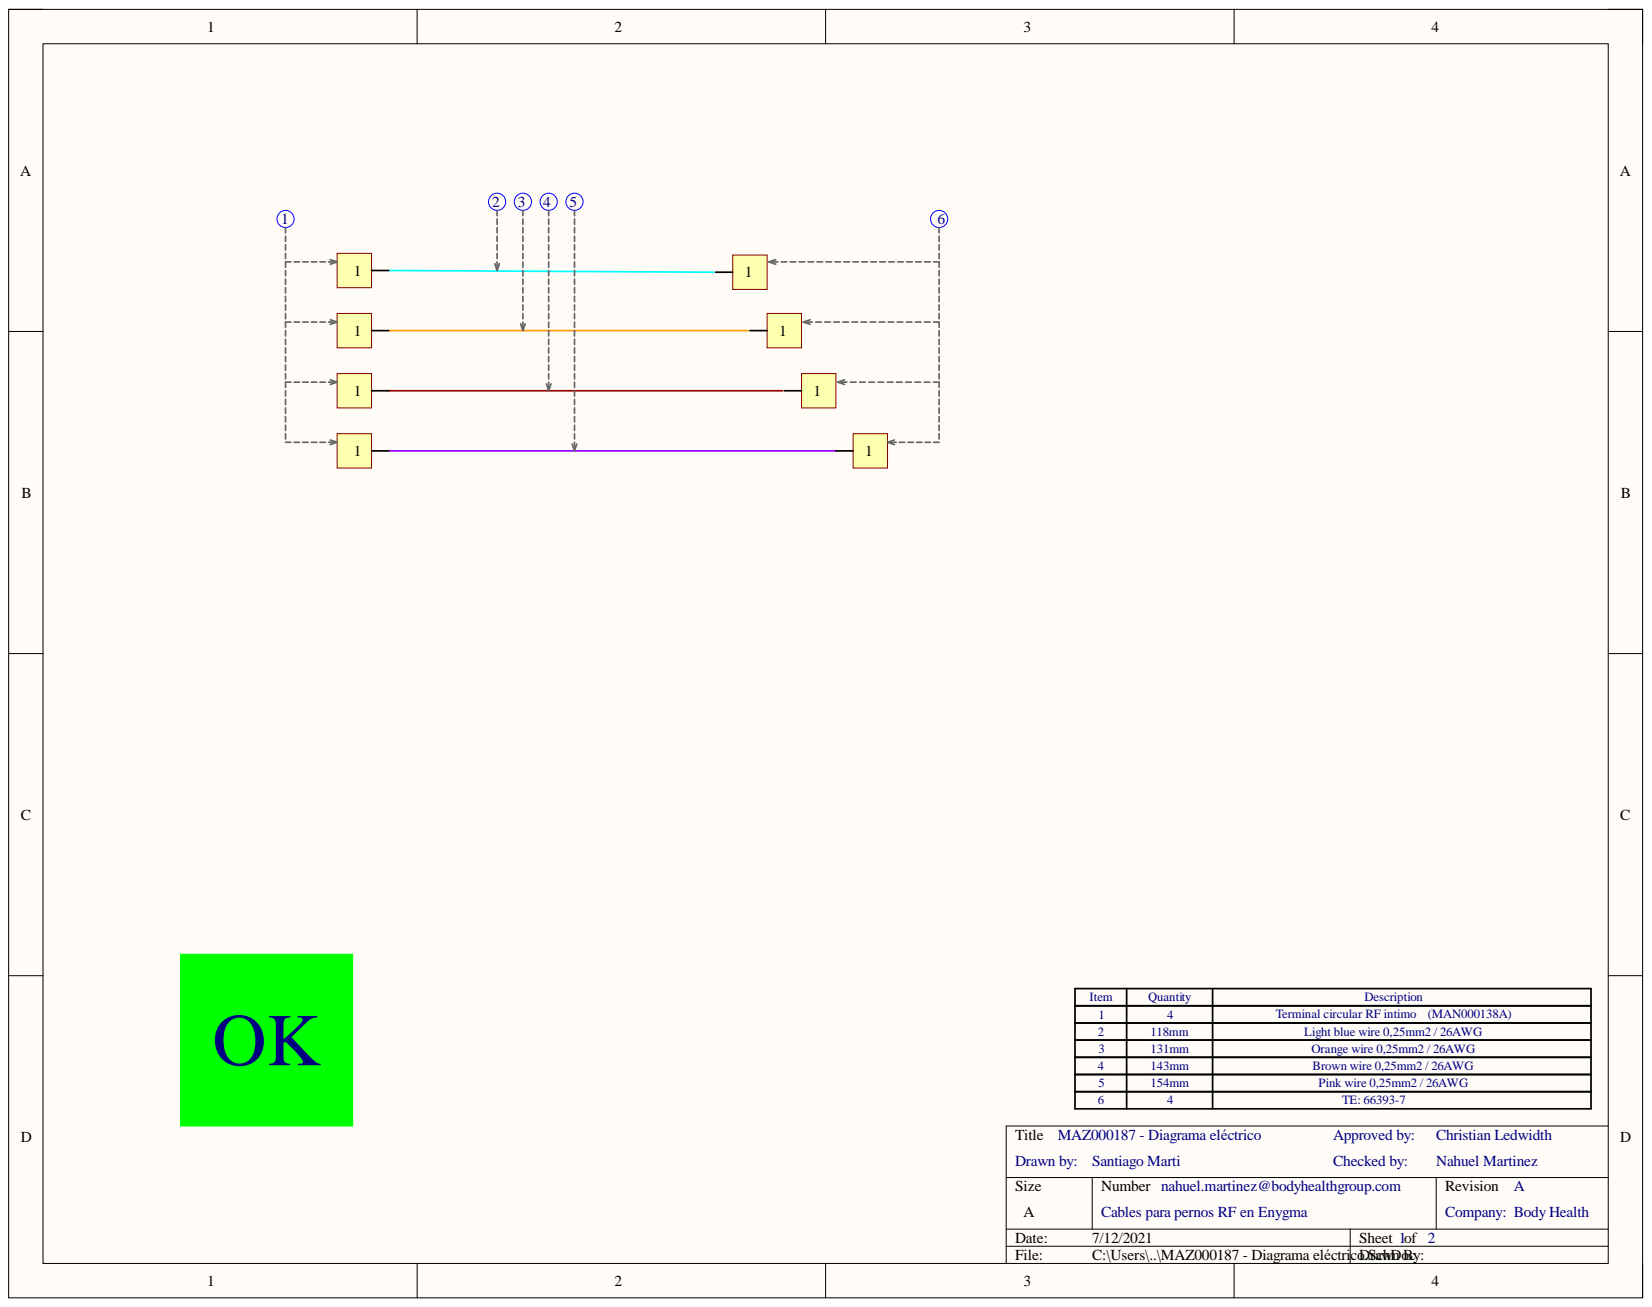
[picture p67: page 1]

Item | Quantity | Description
1 | 4 | Terminal circular RF intimo (MAN000138A)

3 | 131mm | Orange wire 0,25mm2 / 26AWG
4 | 143mm | Brown wire 0,25mm2 / 26AWG

Size A | Number nahuel.martinez@bodyhealthgroup.com Cables para pernos RF en Enygma | Revision A Company: Body Health

Date: 7/12/2021 | Sheet of 1 2
File: C:\Users\..\MAZ000187 - Diagrama eléctricoDr.ScawhDon Bcy:
