jnahuel-developer/Probador-de-cables/Cables/02. Terminados - PDF/MAZ000187 - Diagrama físico.pdf

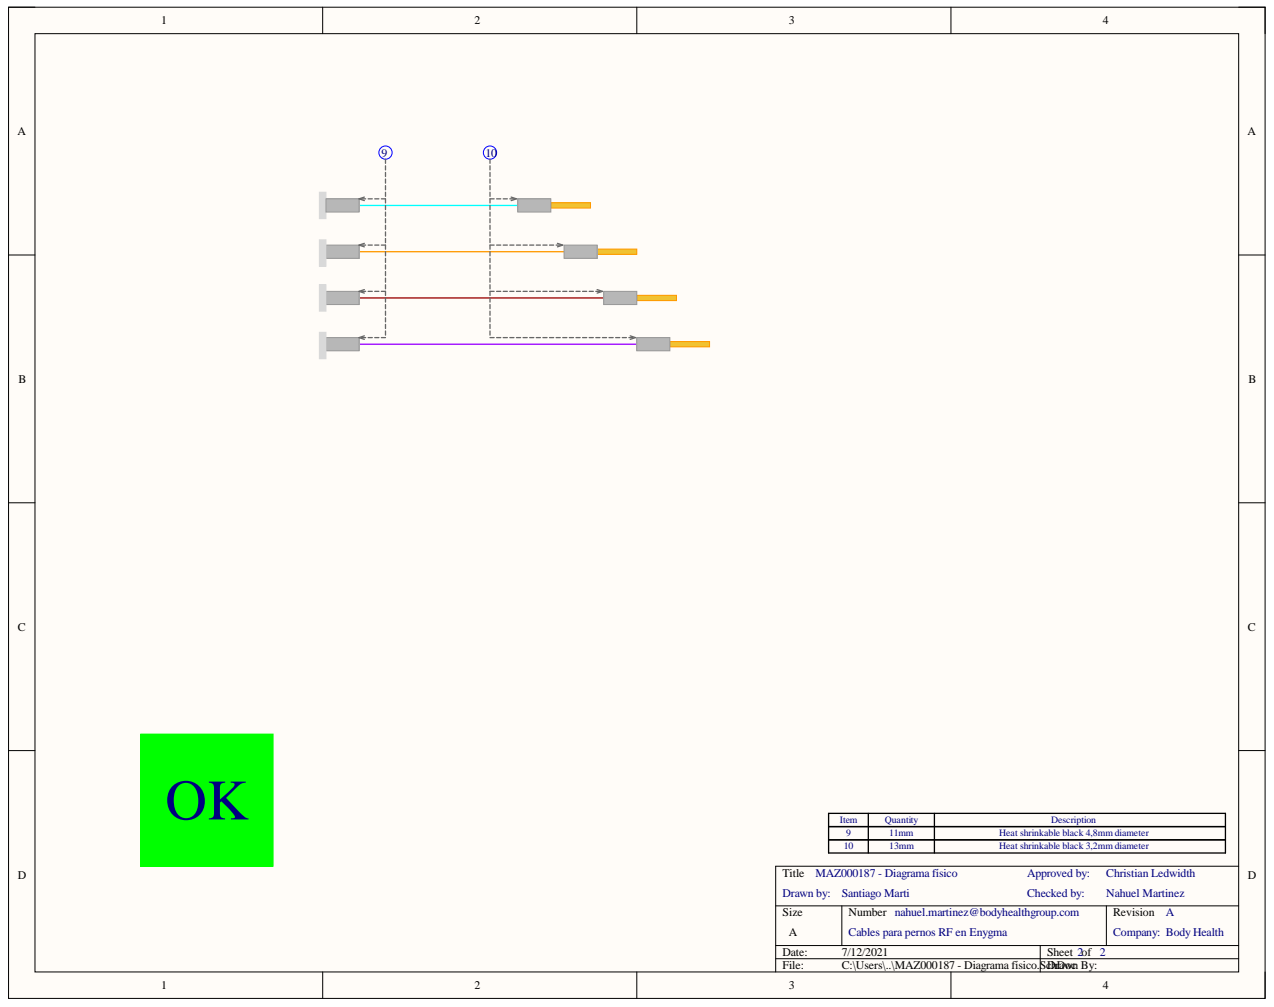
[picture p68: page 1]

Item | Quantity | Description
9 | 11mm | Heat shrinkable black 4,8mm diameter
10 | 13mm | Heat shrinkable black 3,2mm diameter

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

Date: 7/12/2021 | Sheet of 2 2
File: C:\Users\..\MAZ000187 - Diagrama físico.ScDrhDoawcn By:
